barnabyosborne-cmyk/Hp42s_calc/firmware/components/plus42core/core_main.cc

/*****************************************************************************
 * Plus42 -- an enhanced HP-42S calculator simulator
 * Copyright (C) 2004-2026  Thomas Okken
 *
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
 * You should have received a copy of the GNU General Public License
 * along with this program; if not, see http://www.gnu.org/licenses/.
 *****************************************************************************/

#include <stdio.h>
#include <stdlib.h>
#include <string.h>
#include <stdarg.h>
#include <errno.h>

#include "core_main.h"
#include "core_commands2.h"
#include "core_commands4.h"
#include "core_commands7.h"
#include "core_commands8.h"
#include "core_commandsa.h"
#include "core_display.h"
#include "core_display.h"
#include "core_equations.h"
#include "core_helpers.h"
#include "core_keydown.h"
#include "core_math1.h"
#include "core_sto_rcl.h"
#include "core_tables.h"
#include "core_variables.h"
#include "shell.h"
#include "shell_spool.h"

#ifndef BCD_MATH
// We need these locally for BID128->double conversion
#include "bid_conf.h"
#include "bid_functions.h"
#endif

#ifdef WINDOWS
FILE *my_fopen(const char *name, const char *mode);
int my_rename(const char *oldname, const char *newname);
int my_remove(const char *name);
#else
#define my_fopen fopen
#define my_rename rename
#define my_remove remove
#endif


void set_shift(bool state) {
    if (mode_shift != state) {
        mode_shift = state;
        set_annunciators(-1, state, -1, -1, -1, -1);
    }
}

static bool initialized = false;
bool quitting = false;

static void continue_running();
static void stop_interruptible();
static bool handle_error(int error);

int repeating = 0;
int repeating_shift;
int repeating_key;

static int4 oldpc;
static char ann_hold = 0; // 0 = delay; 1 = flush; 2 = normal
bool start_eqn_cursor = false;
int skin_flags = -1;
bool force_redisplay = false;

core_settings_struct core_settings;

struct pending_equation {
    pgm_index idx;
    int4 pc;
    int4 length;
    char *text;
    pending_equation *next;
    bool compatMode;
    bool eval;
};

static pending_equation *eq_queue = NULL;

static void delete_pending_equations() {
    while (eq_queue != NULL) {
        pending_equation *peq = eq_queue;
        eq_queue = peq->next;
        free(peq->text);
        free(peq);
    }
}

static void handle_pending_equations() {
    while (eq_queue != NULL) {
        pending_equation *peq = eq_queue;
        int errpos;
        equation_data *eqd = new_equation_data(peq->text, peq->length, peq->compatMode, &errpos, -1);
        if (eqd == NULL && errpos == -1) {
            /* TODO: Insufficient Memory message */
            delete_pending_equations();
            return;
        }
        pgm_index saved_prgm = current_prgm;
        current_prgm = peq->idx;
        arg_struct arg;
        if (eqd != NULL) {
            arg.type = peq->eval ? ARGTYPE_IND_NUM : ARGTYPE_NUM;
            arg.val.num = eqd->eqn_index;
            store_command_after(&peq->pc, CMD_EMBED, &arg, NULL);
        } else {
            arg.type = ARGTYPE_XSTR;
            arg.length = peq->length;
            arg.val.xstr = peq->text;
            store_command_after(&peq->pc, CMD_XSTR, &arg, NULL);
        }
        current_prgm = saved_prgm;

        eq_queue = peq->next;
        free(peq->text);
        free(peq);
    }
}

void core_init(int *rows, int *cols, int read_saved_state, const char *state_file_name) {

    /* Possible values for read_saved_state:
     * 0: state file not present (Memory Clear)
     * 1: state file present and looks OK so far
     * 2: state file present but not OK (State File Corrupt)
     */

    phloat_init();

    char *state_file_name_crash = NULL;
    if (read_saved_state == 1) {
        // Before loading state, rename the state file by appending .crash
        // to its name. We'll rename it back, right after loading is done.
        // This way, if we crash while loading state, we end up with a
        // renamed state file, so the next time the app is run, it will
        // launch with Memory Clear rather than just crashing on startup over
        // and over, and, on iOS and Android, needing to be deleted and
        // reinstalled.
        size_t bufsize = strlen(state_file_name) + 24;
        state_file_name_crash = (char *) malloc(bufsize);
        uint4 date, time;
        int weekday;
        shell_get_time_date(&time, &date, &weekday);
        snprintf(state_file_name_crash, bufsize, "%s.%08u%08u.crash", state_file_name, date, time);
        my_rename(state_file_name, state_file_name_crash);
        gfile = my_fopen(state_file_name_crash, "rb");
        if (gfile == NULL)
            read_saved_state = 0;
    } else
        gfile = NULL;

    bool clear, too_new = false;
    int reason = 0;
    if (read_saved_state != 1 || !load_state(&clear, &too_new)) {
        reason = too_new ? 2 : (read_saved_state != 0 && !clear) ? 1 : 0;
        requested_disp_r = 8;
        requested_disp_c = 22;
        if (!display_exists())
            display_alloc(requested_disp_r, requested_disp_c);
        hard_reset(reason);
        force_redisplay = true;
    }
    if (gfile != NULL)
        fclose(gfile);
    if (state_file_name_crash != NULL) {
        if (reason == 0) {
            my_rename(state_file_name_crash, state_file_name);
        } else {
            char *tmp = (char *) malloc(strlen(state_file_name_crash) + 3);
            strcpy(tmp, state_file_name_crash);
            tmp[strlen(state_file_name_crash) - 6] = 0;
            strcat(tmp, reason == 1 ? ".corrupt" : ".too_new");
            my_rename(state_file_name_crash, tmp);
            free(tmp);
        }
        free(state_file_name_crash);
    }

    initialized = true;
    quitting = false;

    *rows = requested_disp_r;
    *cols = requested_disp_c;
    shell_set_skin_mode(eqn_alt_keys() ? flags.f.decimal_point ? 1 : 2 : 0);
    #if defined(ANDROID) || defined(IPHONE)
    mode_popup_unknown = true;
    #endif

    ann_hold = 1;
}

void core_save_state(const char *state_file_name) {
    if (mode_interruptible != NULL)
        stop_interruptible();
    set_running(false);

    size_t bufsize = strlen(state_file_name) + 24;
    char *state_file_name_crash = (char *) malloc(bufsize);
    uint4 date, time;
    int weekday;
    shell_get_time_date(&time, &date, &weekday);
    snprintf(state_file_name_crash, bufsize, "%s.%08u%08u.crash", state_file_name, date, time);

    gfile = my_fopen(state_file_name_crash, "wb");
    if (gfile != NULL) {
        bool success = save_state();
        fclose(gfile);
        if (success) {
            my_remove(state_file_name);
            my_rename(state_file_name_crash, state_file_name);
        }
    }
}

void core_cleanup() {
    if (!initialized)
        return;

    initialized = false;
    reset_math();
    free_vartype(varmenu_eqn);
    varmenu_eqn = NULL;
    free_vartype(matedit_x);
    matedit_x = NULL;
    current_prgm.set(root->id, 0);
    for (int i = 0; i <= sp; i++)
        free_vartype(stack[i]);
    sp = -1;
    free(stack);
    stack = NULL;
    stack_capacity = 0;
    free_vartype(lastx);
    lastx = NULL;
    clear_rtns_vars_and_prgms();
    clean_vartype_pools();
}

void set_annunciators(int updn, int shf, int prt, int run, int g, int rad) {
    if (!initialized || quitting)
        return;

    if (ann_hold == 2)
        shell_annunciators(updn, shf, prt, run, g, rad);
}

void core_repaint_display(int rows, int cols, int sflags) {
    if (!initialized || quitting)
        return;

    if (ann_hold == 1) {
        /* This used to be at the end of core_init(), but now that we're
         * calling that function before loading the skin, the initial
         * annunciator update has to be delayed.
         */
        shell_annunciators(mode_updown,
                           mode_shift,
                           0 /*print*/,
                           mode_running,
                           !flags.f.rad && flags.f.grad,
                           flags.f.rad || flags.f.grad);
        ann_hold = 2;
    }

    if (start_eqn_cursor) {
        eqn_restart_cursor();
        start_eqn_cursor = false;
    }

    if (sflags != -1 && sflags != skin_flags) {
        skin_flags = sflags;
        force_redisplay = true;
    }

    if (display_alloc(rows, cols) || (force_redisplay && !mode_plot_viewer))
        redisplay();
    else
        repaint_display();
    force_redisplay = false;
}

bool core_menu() {
    return mode_clall || get_front_menu() != MENU_NONE || eqn_active();
}

bool alpha_active() {
    int menu = get_front_menu();
    return menu >= MENU_ALPHA1 && menu <= MENU_ALPHA_MISC2;
}

int core_alpha_menu() {
    return !mode_getkey && alpha_active() ? 1 : eqn_editing() ? 2 : 0;
}

bool core_hex_menu() {
    return get_front_menu() == MENU_BASE_A_THRU_F;
}

int core_special_menu_key(int which) {
    return special_menu_key(which);
}

static bool core_keydown_2(int key, bool *enqueued, int *repeat);

bool core_keydown(int key, bool *enqueued, int *repeat) {
    if (key >= 1024 && key != 1034) {
        int code = key - 1024;
        char ubuf[5];
        int n = 0;
        if (code < 128) {
            ubuf[n++] = code;
        } else if (code < 2048) {
            ubuf[n++] = (code >> 6) | 0xc0;
            ubuf[n++] = (code & 63) | 0x80;
        } else if (code < 65536) {
            ubuf[n++] = (code >> 12) | 0xe0;
            ubuf[n++] = ((code >> 6) & 63) | 0x80;
            ubuf[n++] = (code & 63) | 0x80;
        } else if (code < 1114112) {
            ubuf[n++] = (code >> 18) | 0xf0;
            ubuf[n++] = ((code >> 12) & 63) | 0x80;
            ubuf[n++] = ((code >> 6) & 63) | 0x80;
            ubuf[n++] = (code & 63) | 0x80;
        } else {
            fail:
            set_shift(false);
            squeak();
            return core_keydown_2(0, enqueued, repeat);
        }
        ubuf[n] = 0;
        char hpbuf[5];
        int len = ascii2hp(hpbuf, 1, ubuf);
        if (len == 0)
            goto fail;
        if (hpbuf[0] == 31 && code != 0x2022 && code != 0xb7)
            // Unsupported character
            goto fail;
        key = 1024 + (hpbuf[0] & 255);
    }
    return core_keydown_2(key, enqueued, repeat);
}

bool core_keydown_command(const char *name, int type, bool *enqueued, int *repeat) {
    char hpname[70];
    int len = ascii2hp(hpname, 63, name);
    if (type == 2) {
        int ch = hpname[0] & 255;
        if (len == 0) {
            ch = 0;
            set_shift(false);
            squeak();
        }
        return core_keydown_2(ch == 0 ? 0 : ch + 1024, enqueued, repeat);
    } else {
        int cmd;
        if (type == 0) {
            if (string_equals(hpname, len, "NULL", 4)) {
                cmd = CMD_NONE;
                set_shift(false);
            } else {
                cmd = find_builtin(hpname, len);
                if (cmd == CMD_NONE) {
                    set_shift(false);
                    squeak();
                }
            }
        } else {
            if (len == 0 || len > 7) {
                cmd = CMD_NONE;
                set_shift(false);
                squeak();
            } else {
                memcpy(dcm_lbl + 1, hpname, len);
                dcm_lbl[0] = len;
                cmd = CMD_NULL; // Magic value to trigger XEQ "dcm_lbl"
            }
        }
        return core_keydown_2(cmd == CMD_NONE ? 0 : cmd + 2048, enqueued, repeat);
    }
}

static bool core_keydown_2(int key, bool *enqueued, int *repeat) {

    *enqueued = 0;
    *repeat = 0;

    if (!initialized || quitting)
        return false;

    if (key != 0)
        no_keystrokes_yet = false;

    int eqr = eqn_keydown(key, repeat);
    if (eqr != 0) {
        if (eqr != 2)
            // CALC not pressed; prevent key timeouts
            *enqueued = 1;
        return eqr == 3;
    }

    if (mode_plot_viewer) {
        *enqueued = 1;
        return plot_keydown(key, repeat);
    }

    if (key == KEY_SHIFT) {
        set_shift(!mode_shift);
        if (!mode_menu_static) {
            int menuid = get_front_menu();
            if (menuid == MENU_TOP_FCN || menuid == MENU_PGM_FCN1 || menuid == MENU_STAT1
                    || menuid == MENU_BASE2 || menuid == MENU_BASE3
                    || menuid == MENU_CUSTOM1 || menuid == MENU_CUSTOM2 || menuid == MENU_CUSTOM3)
                redisplay();
        }
        return (mode_running && !mode_getkey && !mode_pause) || keybuf_head != keybuf_tail;
    }

    if (mode_pause) {
        if (key == 0)
            return false;
        mode_pause = false;
        set_running(false);
        if (!mode_shift && (key == KEY_RUN || key == KEY_EXIT)) {
            redisplay();
            return false;
        }
    }

    if (mode_interruptible != NULL) {
        /* We're in the middle of an interruptible function
         * (e.g., INVRT, PRP); queue up any keystrokes and invoke
         * the appropriate callback to keep the function moving along
         */
        int error;
        bool keep_running;
        if (key != 0) {
            /* Enqueue... */
            *enqueued = 1;
            if (key == KEY_EXIT ||
                    (mode_stoppable && !mode_shift && key == KEY_RUN)) {
                keybuf_tail = keybuf_head;
                stop_interruptible();
                return false;
            } else {
                if (((keybuf_head + 1) & 15) != keybuf_tail) {
                    if (mode_shift)
                        key = -key;
                    keybuf[keybuf_head] = key;
                    keybuf_head = (keybuf_head + 1) & 15;
                }
            }
            set_shift(false);
        }
        error = mode_interruptible(false);
        if (error == ERR_INTERRUPTIBLE)
            /* Still not done */
            return true;
        mode_interruptible = NULL;
        keep_running = handle_error(error);
        if (mode_running) {
            if (!keep_running)
                set_running(false);
        } else {
            set_annunciators(-1, -1, -1, 0, -1, -1);
            pending_command = CMD_NONE;
        }
        if (mode_running || keybuf_tail != keybuf_head)
            return true;
        else {
            redisplay();
            return false;
        }
    }

    if (mode_running && !mode_getkey) {
        /* We're running; queue up any keystrokes and invoke
         * continue_running() to keep the program moving along
         */
        if (key != 0) {
            if (key == KEY_EXIT) {
                keybuf_tail = keybuf_head;
                set_shift(false);
                set_running(false);
                pending_command = CMD_CANCELLED;
                return false;
            }
            /* Enqueue... */
            *enqueued = 1;
            if (!mode_shift && key == KEY_RUN) {
                keybuf_tail = keybuf_head;
                set_running(false);
                redisplay();
                return false;
            }
            if (((keybuf_head + 1) & 15) != keybuf_tail) {
                if (mode_shift)
                    key = -key;
                keybuf[keybuf_head] = key;
                keybuf_head = (keybuf_head + 1) & 15;
            }
            set_shift(false);
        }
        continue_running();
        if ((mode_running && !mode_getkey && !mode_pause) || keybuf_tail != keybuf_head)
            return true;
        else {
            if (mode_getkey)
                /* Technically, the program is still running, but we turn
                 * off the 'running' annunciator so that the user has some
                 * cue that they may now type. (Actually, I'm doing it
                 * purely because the HP-42S does it, too!)
                 */
                set_annunciators(-1, -1, -1, 0, -1, -1);
            else if (!mode_pause)
                redisplay();
            return false;
        }
    }

    /* If we get here, mode_running must be false.
     * or a program is running but hanging in GETKEY;
     */

    if (keybuf_tail != keybuf_head) {
        /* We're not running, or a program is waiting in GETKEY;
         * feed queued-up keystroke to keydown()
         */
        int oldshift = 0;
        int oldkey = keybuf[keybuf_tail];
        if (oldkey < 0) {
            oldkey = -oldkey;
            oldshift = 1;
        }
        keybuf_tail = (keybuf_tail + 1) & 15;
        /* If we're in GETKEY mode, the 'running' annunciator is off;
         * see the code circa 30 lines back.
         * We now turn it back on since program execution resumes.
         */
        if (mode_getkey && mode_running)
            set_annunciators(-1, -1, -1, 1, -1, -1);
        /* Feed the dequeued key to the usual suspects */
        keydown(oldshift, oldkey);
        core_keyup();
        /* We've just de-queued a key; may have to enqueue
         * one as well, if the user is actually managing to
         * type while we're unwinding the keyboard buffer
         */
        if (key != 0) {
            if (((keybuf_head + 1) & 15) != keybuf_tail) {
                if (mode_shift)
                    key = -key;
                keybuf[keybuf_head] = key;
                keybuf_head = (keybuf_head + 1) & 15;
            }
            set_shift(false);
        }
        return (mode_running && !mode_getkey) || keybuf_head != keybuf_tail;
    }

    /* No program is running, or it is running but waiting for a
     * keystroke (GETKEY); handle any new keystroke that has just come in
     */
    if (key != 0) {
        int shift = mode_shift;
        set_shift(false);
        if (mode_getkey && mode_running)
            set_annunciators(-1, -1, -1, 1, -1, -1);
        keydown(shift, key);
        if (repeating != 0) {
            *repeat = repeating;
            repeating = 0;
        }
        return mode_running && !mode_getkey;
    }

    /* Nothing going on at all! */
    return false;
}

int dequeue_key() {
    if (keybuf_tail == keybuf_head)
        return 0;
    int key = keybuf[keybuf_tail];
    keybuf_tail = (keybuf_tail + 1) & 15;
    bool shift = key < 0;
    if (shift)
        key = -key;
    if (key > 2048) {
        key = find_cmd_getkey_mapping(key - 2048);
        if (key == 0)
            squeak();
    }
    else if (shift)
        key += 37;
    return key;
}

int core_repeat() {
    if (!initialized || quitting)
        return 0;

    int r = eqn_repeat();
    if (r != -1)
        return r;
    if (mode_plot_viewer) {
        r = plot_repeat();
        if (r != -1)
            return r;
    }
    keydown(repeating_shift, repeating_key);
    int rpt = repeating;
    repeating = 0;
    return rpt;
}

void core_keytimeout1() {
    if (!initialized || quitting)
        return;

    if (pending_command == CMD_LINGER1 || pending_command == CMD_LINGER2)
        return;
    if (pending_command == CMD_RUN || pending_command == CMD_SST
            || pending_command == CMD_SST_UP || pending_command == CMD_SST_RT) {
        int saved_pending_command = pending_command;
        if (pc == -1)
            pc = 0;
        move_prgm_highlight(1);
        flags.f.prgm_mode = 2; /* HACK - magic value to tell redisplay() */
                               /* not to suppress option menu highlights */
        pending_command = CMD_NONE;
        redisplay();
        flags.f.prgm_mode = 0;
        pending_command = saved_pending_command;
    } else if (pending_command != CMD_NONE && pending_command != CMD_CANCELLED
            && (cmd_array[pending_command].flags & FLAG_NO_SHOW) == 0) {
        bool saved_prgm_mode = flags.f.prgm_mode;
        flags.f.prgm_mode = 0;
        redisplay(2);
        flags.f.prgm_mode = saved_prgm_mode;
    }
}

void core_keytimeout2() {
    if (!initialized || quitting)
        return;

    if (pending_command == CMD_LINGER1 || pending_command == CMD_LINGER2)
        return;
    remove_program_catalog = 0;
    if (pending_command != CMD_NONE && pending_command != CMD_CANCELLED
            && (cmd_array[pending_command].flags & FLAG_NO_SHOW) == 0) {
        pending_command = CMD_NULL;
        bool saved_prgm_mode = flags.f.prgm_mode;
        flags.f.prgm_mode = 0;
        redisplay(2);
        flags.f.prgm_mode = saved_prgm_mode;
        pending_command = CMD_CANCELLED;
    }
}

bool core_timeout3(bool repaint) {
    if (!initialized || quitting)
        return false;

    if (eqn_timeout())
        return false;
    if (mode_pause) {
        if (repaint) {
            /* The PSE ended normally */
            mode_pause = false;
            if (mode_goose >= 0)
                mode_goose = -1 - mode_goose;
        }
        return true;
    }
    /* Remove the output of SHOW, MEM, or shift-VARMENU from the display */
    if (pending_command == CMD_LINGER1)
        pending_command = CMD_CANCELLED;
    else if (pending_command == CMD_LINGER2) {
        clear_message();
        pending_command = CMD_NONE;
        if (repaint)
            redisplay();
    }
    return false;
}

static void print_equation_segment(int4 pc) {
    if (current_prgm.dir != eq_dir->id)
        return;
    equation_data *eqd = eq_dir->prgms[current_prgm.idx].eq_data;
    if (eqd->map == NULL)
        return;
    int4 pos = eqd->map->lookup(pc2line(pc));
    if (pos == -1)
        return;
    static int4 last_eqn = -1;
    static int4 last_pos = -1;
    if (eqd->eqn_index == last_eqn && pos == last_pos)
        return;
    last_eqn = eqd->eqn_index;
    last_pos = pos;
    int w = flags.f.double_wide_print ? 12 : 24;
    int apos = flags.f.double_wide_print ? 4 : 9;
    char line[24];
    for (int i = 0; i < apos; i++) {
        int n = i + pos - apos;
        line[i] = n < 0 ? ' ' : eqd->text[n];
    }
    line[apos] = 6;
    for (int i = apos + 1; i < w; i++) {
        int n = i + pos - apos - 1;
        line[i] = n >= eqd->length ? ' ' : eqd->text[n];
    }
    print_text(line, w, true);
}

bool core_keyup() {
    if (!initialized || quitting)
        return false;

    if (mode_pause) {
        /* The only way this can happen is if they key in question was Shift */
        return false;
    }

    int error = ERR_NONE;

    if (pending_command == CMD_LINGER1 || pending_command == CMD_LINGER2) {
        pending_command = CMD_LINGER2;
        return mode_running || keybuf_head != keybuf_tail;
    }

    if (pending_command == CMD_SILENT_OFF) {
#ifdef IPHONE
        if (off_enabled()) {
            shell_always_on(0);
            quitting = true;
            shell_powerdown();
        } else {
            set_running(false);
            squeak();
        }
#else
        shell_always_on(0);
        quitting = true;
        shell_powerdown();
#endif
        pending_command = CMD_NONE;
        return false;
    }

    if (pending_command == CMD_NONE)
        return mode_running || mode_interruptible != NULL || keybuf_head != keybuf_tail;

    if (remove_program_catalog) {
        if (mode_transientmenu == MENU_CATALOG)
            set_menu(MENULEVEL_TRANSIENT, MENU_NONE);
        else if (mode_plainmenu == MENU_CATALOG)
            set_menu(MENULEVEL_PLAIN, MENU_NONE);
        remove_program_catalog = 0;
    }

    if (pending_command == CMD_CANCELLED || pending_command == CMD_NULL) {
        pending_command = CMD_NONE;
        redisplay();
        return mode_running || keybuf_head != keybuf_tail;
    }

    mode_varmenu = pending_command == CMD_VMSTO
                    || pending_command == CMD_VMSTO2
                    || pending_command == CMD_VMSOLVE
                    || pending_command == CMD_VMEXEC;

    if (input_length > 0) {
        /* INPUT active */
        if (pending_command == CMD_RUN || pending_command == CMD_SST
                || pending_command == CMD_SST_UP || pending_command == CMD_SST_RT) {
            int err;
            if (sp == -1) {
                vartype_real zero;
                zero.type = TYPE_REAL;
                zero.x = 0;
                stack[++sp] = (vartype *) &zero;
                err = generic_sto(&input_arg, 0);
                sp--;
            } else {
                err = generic_sto(&input_arg, 0);
            }
            input_length = 0;
            if (err != ERR_NONE) {
                pending_command = CMD_NONE;
                display_error(err);
                redisplay();
                return mode_running || keybuf_head != keybuf_tail;
            }
        } else if (pending_command == CMD_GTO
                || pending_command == CMD_GTODOT
                || pending_command == CMD_GTODOTDOT
                || pending_command == CMD_RTN)
            /* NOTE: set_running(true) also ends INPUT mode, so commands that
             * cause program execution to start do not have to be handled here.
             */
            input_length = 0;
    }

    if (pending_command == CMD_VMEXEC) {
        eqn_end();
        string_copy(reg_alpha, &reg_alpha_length,
                    pending_command_arg.val.text, pending_command_arg.length);
        goto do_run;
    }
    if (pending_command == CMD_PMEXEC) {
        eqn_end();
        vartype *v;
        if (pending_command_arg.type == ARGTYPE_EQN) {
            equation_data *eqdata = eq_dir->prgms[pending_command_arg.val.num].eq_data;
            int len = eqdata->length > 44 ? 44 : eqdata->length;
            string_copy(reg_alpha, &reg_alpha_length, eqdata->text, len);
            v = new_equation(eqdata);
        } else {
            string_copy(reg_alpha, &reg_alpha_length,
                        pending_command_arg.val.text, pending_command_arg.length);
            v = new_string(pending_command_arg.val.text, pending_command_arg.length);
        }
        // This is an incompatible change from the original PGMMENU, strictly speaking,
        // since it only returned the label name in ALPHA. I have to do something in
        // order to accommodate equations, though. So, if a program is selected, I
        // return it in ALPHA, as before, but I *also* return it as a string in X.
        // My hope is that no one will depend on the contents of the stack right after
        // PGMMENU, since the user is in normal interactive mode while the menu is
        // active.
        // Of course the scenario of the user going into the equation editor, selecting
        // an equation, and pressing CALC, is entirely new, so what we do in that case
        // isn't really an issue from a compatibility point of view. So, I'm copying as
        // much of the equation as I can into ALPHA, and placing the equation itself
        // in X.
        if (v != NULL)
            recall_result(v);
        goto do_run;
    }
    if (pending_command == CMD_RUN || pending_command == CMD_SST_UP) {
        do_run:
        if ((flags.f.trace_print || flags.f.normal_print)
                && flags.f.printer_exists)
            print_command(pending_command, &pending_command_arg);
        if (pending_command == CMD_SST_UP)
            step_out();
        pending_command = CMD_NONE;
        if (pc == -1)
            pc = 0;
        set_running(true);
        return true;
    }

    if (pending_command == CMD_SST || pending_command == CMD_SST_RT) {
        int cmd;
        arg_struct arg;
        oldpc = pc;
        if (pc == -1)
            pc = 0;
        get_next_command(&pc, &cmd, &arg, 1, NULL);
        if (pending_command == CMD_SST_RT
                && (cmd == CMD_XEQ || cmd == CMD_XEQL || cmd == CMD_EVAL
                    || cmd == CMD_EVALN || cmd == CMD_SOLVE || cmd == CMD_INTEG)) {
            pc = oldpc;
            step_over();
            goto do_run;
        }
        if ((flags.f.trace_print || flags.f.normal_print)
                && flags.f.printer_exists) {
            if (cmd == CMD_LBL)
                print_text(NULL, 0, true);
            print_equation_segment(oldpc);
            print_program_line(current_prgm, oldpc);
        }
        mode_disable_stack_lift = false;
        set_running(true);
        error = handle(cmd, &arg);
        set_running(false);
        mode_pause = false;
    } else {
        if ((flags.f.trace_print || flags.f.normal_print)
                && flags.f.printer_exists)
            print_command(pending_command, &pending_command_arg);
        mode_disable_stack_lift = false;
        error = handle(pending_command, &pending_command_arg);
        mode_pause = false;
        if (pending_command >= CMD_ROW_PLUS && pending_command <= CMD_COL_MINUS || pending_command == CMD_SETDS) {
            pending_command = CMD_LINGER2;
            shell_request_timeout3(2000);
            redisplay();
            return false;
        }
    }

    if (quitting)
        return false;

    if (error == ERR_INTERRUPTIBLE) {
        set_annunciators(-1, -1, -1, 1, -1, -1);
        pending_command = CMD_NONE;
        return true;
    }

    handle_error(error);
    pending_command = CMD_NONE;
    if (!mode_getkey && !mode_pause)
        redisplay();
    return (mode_running && !mode_getkey && !mode_pause) || keybuf_head != keybuf_tail;
}

bool core_powercycle() {
    bool need_redisplay = false;

    if (mode_interruptible != NULL)
        stop_interruptible();

    no_keystrokes_yet = true;

    keybuf_tail = keybuf_head;
    set_shift(false);
    #if (!defined(ANDROID) && !defined(IPHONE))
    shell_always_on(0);
    #endif
    pending_command = CMD_NONE;

    if (mode_getkey) {
        /* A real HP-42S can't be switched off while GETKEY is active: pressing
         * OFF on the keyboard returns code 70 and stops program execution; and
         * when the auto-poweroff timeout expires, code 70 is returned but
         * program execution continues.
         * Since Free42 can be shut down in a way the HP-42S can't, by exiting
         * the application, I have to fake it a bit; I put 70 in X as if the
         * user had done OFF twice on a real 42S.
         */
        vartype *seventy = new_real(70);
        if (seventy != NULL) {
            if (recall_result(seventy) != ERR_NONE)
                goto nomem;
            flags.f.stack_lift_disable = 0;
        } else {
            nomem:
            display_error(ERR_INSUFFICIENT_MEMORY);
            flags.f.auto_exec = 0;
        }
        if (!flags.f.auto_exec)
            need_redisplay = true;
        mode_getkey = false;
    }

    if (flags.f.auto_exec) {
        if (mode_command_entry)
            finish_command_entry(false);
        if (flags.f.prgm_mode) {
            if (mode_alpha_entry) {
                pc = incomplete_saved_pc;
                prgm_highlight_row = incomplete_saved_highlight_row;
            } else if (mode_number_entry) {
                arg_struct arg;
                arg.type = ARGTYPE_DOUBLE;
                arg.val_d = entered_number;
                cmdline[cmdline_length] = 0;
                store_command(pc, CMD_NUMBER, &arg, cmdline);
                move_prgm_highlight(1);
            }
            flags.f.prgm_mode = false;
        }
        mode_alpha_entry = false;
        mode_number_entry = false;
        set_menu(MENULEVEL_ALPHA, MENU_NONE);
        set_running(true);
        flags.f.auto_exec = 0;
        need_redisplay = false;
    } else {
        if (mode_running) {
            set_running(false);
            need_redisplay = true;
        }
    }

#ifdef BCD_MATH
    if (need_redisplay || state_file_number_format != NUMBER_FORMAT_BID128)
        redisplay();
#else
    if (need_redisplay || state_file_number_format != NUMBER_FORMAT_BINARY)
        redisplay();
#endif

    return mode_running;
}

char *core_list_programs() {
    int bufsize = 1024;
    char *buf = (char *) malloc(bufsize);
    if (buf == NULL)
        return NULL;
    int lastidx = -1;
    int bufptr = 4;
    int label;
    int count = 0;
    for (label = 0; label < cwd->labels_count; label++) {
        int len = cwd->labels[label].length;
        char name[51];
        int namelen = 0;
        int end = 0;
        int i;

        if (len == 0) {
            if (cwd->labels[label].prgm == lastidx)
                continue;
            if (label == cwd->labels_count - 1) {
                string2buf(name, 51, &namelen, ".END.", 5);
                namelen = 5;
            } else {
                string2buf(name, 51, &namelen, "END", 3);
                namelen = 3;
            }
            end = 1;
        } else {
            name[namelen++] = '"';
            namelen += hp2ascii(name + namelen, cwd->labels[label].name, len);
            name[namelen++] = '"';
            end = cwd->labels[label + 1].length == 0;
        }

        lastidx = cwd->labels[label].prgm;

        if (bufptr + namelen + 1 >= bufsize) {
            bufsize += 1024;
            char *newbuf = (char *) realloc(buf, bufsize);
            if (newbuf == NULL) {
                if (bufptr > 0 && buf[bufptr - 1] != 0) {
                    buf[bufptr - 1] = 0;
                    count++;
                }
                goto done;
            }
            buf = newbuf;
        }
        for (i = 0; i < namelen; i++)
            buf[bufptr++] = name[i];
        if (end) {
            buf[bufptr++] = 0;
            count++;
        } else {
            buf[bufptr++] = ' ';
        }
    }
    done:
    buf[0] = (char) (count >> 24);
    buf[1] = (char) (count >> 16);
    buf[2] = (char) (count >> 8);
    buf[3] = (char) count;
    return buf;
}

static void export_hp42s(int index) {
    int4 pc = 0;
    int cmd;
    arg_struct arg;
    pgm_index saved_prgm = current_prgm;
    unsigned char code_flags, code_name, code_std_1, code_std_2;
    char cmdbuf[50];
    int cmdlen;
    char buf[1000];
    int buflen = 0;
    int i;

    current_prgm.set(cwd->id, index);
    do {
        const char *orig_num;
        get_next_command(&pc, &cmd, &arg, 0, &orig_num);
        code_flags = (cmd_array[cmd].flags & (FLAG_SPECIAL | FLAG_ILLEGAL)) >> 5;
        code_name = cmd_array[cmd].scode;
        code_std_1 = cmd_array[cmd].code1;
        code_std_2 = cmd_array[cmd].code2;
        cmdlen = 0;
        switch (code_flags) {
            case 1:
                /* A command that requires some special attention */
                if (cmd == CMD_STO) {
                    if (arg.type == ARGTYPE_NUM && arg.val.num <= 15)
                        cmdbuf[cmdlen++] = 0x30 + arg.val.num;
                    else
                        goto normal;
                } else if (cmd == CMD_RCL) {
                    if (arg.type == ARGTYPE_NUM && arg.val.num <= 15)
                        cmdbuf[cmdlen++] = 0x20 + arg.val.num;
                    else
                        goto normal;
                } else if (cmd == CMD_FIX || cmd == CMD_SCI || cmd == CMD_ENG) {
                    char byte2;
                    if (arg.type != ARGTYPE_NUM || arg.val.num <= 9)
                        goto normal;
                    cmdbuf[cmdlen++] = (char) 0xf1;
                    if (arg.val.num == 10) {
                        switch (cmd) {
                            case CMD_FIX: byte2 = (char) 0xd5; break;
                            case CMD_SCI: byte2 = (char) 0xd6; break;
                            case CMD_ENG: byte2 = (char) 0xd7; break;
                        }
                    } else {
                        switch (cmd) {
                            case CMD_FIX: byte2 = (char) 0xe5; break;
                            case CMD_SCI: byte2 = (char) 0xe6; break;
                            case CMD_ENG: byte2 = (char) 0xe7; break;
                        }
                    }
                    cmdbuf[cmdlen++] = byte2;
                } else if (cmd == CMD_SIZE) {
                    cmdbuf[cmdlen++] = (char) 0xf3;
                    cmdbuf[cmdlen++] = (char) 0xf7;
                    cmdbuf[cmdlen++] = arg.val.num >> 8;
                    cmdbuf[cmdlen++] = arg.val.num;
                } else if (cmd == CMD_EMBED) {
                    int4 id = saving_state ? arg.val.num
                            : eq_dir->prgms[arg.val.num].eq_data->compatMode ? -2 : -1;
                    cmdbuf[cmdlen++] = (char) 0xf6;
                    cmdbuf[cmdlen++] = (char) 0xa7;
                    cmdbuf[cmdlen++] = (char) (arg.type == ARGTYPE_NUM ? 0x76 : 0x7e);
                    cmdbuf[cmdlen++] = id >> 24;
                    cmdbuf[cmdlen++] = id >> 16;
                    cmdbuf[cmdlen++] = id >> 8;
                    cmdbuf[cmdlen++] = id;
                    if (!saving_state) {
                        /* Flush cmdbuf, because the XSTR logic bypasses it */
                        for (i = 0; i < cmdlen; i++)
                            buf[buflen++] = cmdbuf[i];
                        cmdlen = 0;
                        equation_data *eqd = eq_dir->prgms[arg.val.num].eq_data;
                        arg.val.xstr = eqd->text;
                        arg.length = eqd->length > 65535 ? 65535 : eqd->length;
                        goto do_xstr;
                    }
                } else if (cmd == CMD_LBL) {
                    if (arg.type == ARGTYPE_NUM) {
                        if (arg.val.num <= 14)
                            cmdbuf[cmdlen++] = 0x01 + arg.val.num;
                        else
                            goto normal;
                    } else if (arg.type == ARGTYPE_STR) {
                        cmdbuf[cmdlen++] = (char) 0xc0;
                        cmdbuf[cmdlen++] = 0x00;
                        cmdbuf[cmdlen++] = 0xf1 + arg.length;
                        cmdbuf[cmdlen++] = 0x00;
                        for (i = 0; i < arg.length; i++)
                            cmdbuf[cmdlen++] = arg.val.text[i];
                    } else
                        goto normal;
                } else if (cmd == CMD_INPUT) {
                    if (arg.type == ARGTYPE_IND_NUM
                            || arg.type == ARGTYPE_IND_STK)
                        code_std_2 = 0xee;
                    goto normal;
                } else if (cmd == CMD_XEQ) {
                    if (arg.type == ARGTYPE_NUM || arg.type == ARGTYPE_STK
                                                || arg.type == ARGTYPE_LCLBL) {
                        code_std_1 = 0xe0;
                        code_std_2 = 0x00;
                        goto normal;
                    } else if (arg.type == ARGTYPE_STR) {
                        cmdbuf[cmdlen++] = 0x1e;
                        cmdbuf[cmdlen++] = 0xf0 + arg.length;
                        for (i = 0; i < arg.length; i++)
                            cmdbuf[cmdlen++] = arg.val.text[i];
                    } else
                        goto normal;
                } else if (cmd == CMD_GTO) {
                    if (arg.type == ARGTYPE_NUM && arg.val.num <= 14) {
                        cmdbuf[cmdlen++] = 0xb1 + arg.val.num;
                        cmdbuf[cmdlen++] = 0x00;
                    } else if (arg.type == ARGTYPE_NUM
                                        || arg.type == ARGTYPE_STK
                                        || arg.type == ARGTYPE_LCLBL) {
                        code_std_1 = 0xd0;
                        code_std_2 = 0x00;
                        goto normal;
                    } else if (arg.type == ARGTYPE_IND_NUM
                                        || arg.type == ARGTYPE_IND_STK) {
                        cmdbuf[cmdlen++] = (char) 0xae;
                        if (arg.type == ARGTYPE_IND_NUM)
                            arg.type = ARGTYPE_NUM;
                        else
                            arg.type = ARGTYPE_STK;
                        goto non_string_suffix;
                    } else if (arg.type == ARGTYPE_STR) {
                        cmdbuf[cmdlen++] = 0x1d;
                        cmdbuf[cmdlen++] = 0xf0 + arg.length;
                        for (i = 0; i < arg.length; i++)
                            cmdbuf[cmdlen++] = arg.val.text[i];
                    } else
                        goto normal;
                } else if (cmd == CMD_END) {
                    cmdbuf[cmdlen++] = (char) 0xc0;
                    cmdbuf[cmdlen++] = 0x00;
                    cmdbuf[cmdlen++] = 0x0d;
                } else if (cmd == CMD_N_PLUS_U) {
                    cmdbuf[cmdlen++] = (char) 0xa6;
                    cmdbuf[cmdlen++] = (char) 0xf7;
                    if (arg.type != ARGTYPE_NONE)
                        goto do_number;
                } else if (cmd == CMD_NUMBER) {
                    do_number:
                    const char *p;
                    if (orig_num != NULL)
                        p = orig_num;
                    else
                        p = phloat2program(arg.val_d);
                    char c;
                    while ((c = *p++) != 0) {
                        if (c >= '0' && c <= '9')
                            cmdbuf[cmdlen++] = 0x10 + c - '0';
                        else if (c == '.' || c == ',')
                            cmdbuf[cmdlen++] = 0x1a;
                        else if (c == 24)
                            cmdbuf[cmdlen++] = 0x1b;
                        else if (c == '-')
                            cmdbuf[cmdlen++] = 0x1c;
                        else
                            /* Should not happen */
                            continue;
                    }
                    cmdbuf[cmdlen++] = 0x00;
                    if (cmd == CMD_N_PLUS_U) {
                        for (i = 0; i < cmdlen; i++)
                            buf[buflen++] = cmdbuf[i];
                        cmdlen = 0;
                        goto do_xstr;
                    }
                } else if (cmd == CMD_STRING) {
                    cmdbuf[cmdlen++] = 0xf0 + arg.length;
                    for (i = 0; i < arg.length; i++)
                        cmdbuf[cmdlen++] = arg.val.text[i];
                } else if (cmd >= CMD_ASGN01 && cmd <= CMD_ASGN18) {
                    cmdbuf[cmdlen++] = 0xf2 + arg.length;
                    cmdbuf[cmdlen++] = (char) 0xc0;
                    for (i = 0; i < arg.length; i++)
                        cmdbuf[cmdlen++] = arg.val.text[i];
                    cmdbuf[cmdlen++] = cmd - CMD_ASGN01;
                } else if ((cmd >= CMD_KEY1G && cmd <= CMD_KEY9G)
                            || (cmd >= CMD_KEY1X && cmd <= CMD_KEY9X)) {
                    int keyg = cmd <= CMD_KEY9G;
                    int keynum = cmd - (keyg ? CMD_KEY1G : CMD_KEY1X) + 1;
                    if (arg.type == ARGTYPE_STR || arg.type == ARGTYPE_IND_STR){
                        cmdbuf[cmdlen++] = 0xf2 + arg.length;
                        cmdbuf[cmdlen++] = keyg ? 0xc3 : 0xc2;
                        if (arg.type == ARGTYPE_IND_STR)
                            cmdbuf[cmdlen - 1] += 8;
                        cmdbuf[cmdlen++] = keynum;
                        for (i = 0; i < arg.length; i++)
                            cmdbuf[cmdlen++] = arg.val.text[i];
                    } else {
                        cmdbuf[cmdlen++] = (char) 0xf3;
                        cmdbuf[cmdlen++] = keyg ? 0xe3 : 0xe2;
                        cmdbuf[cmdlen++] = keynum;
                        goto non_string_suffix;
                    }
                } else if (cmd == CMD_XROM) {
                    if (arg.type == ARGTYPE_NUM) {
                        cmdbuf[cmdlen++] = (char) (0xa0 + ((arg.val.num >> 8) & 7));
                        cmdbuf[cmdlen++] = (char) arg.val.num;
                    } else {
                        cmdbuf[cmdlen++] = (char) (0xf0 + arg.length);
                        for (int i = 0; i < arg.length; i++)
                            cmdbuf[cmdlen++] = arg.val.text[i];
                    }
                } else if (cmd == CMD_XSTR) {
                    do_xstr:
                    int len = arg.length;
                    if (len == 0) {
                        cmdbuf[cmdlen++] = (char) 0xf2;
                        cmdbuf[cmdlen++] = (char) 0xa7;
                        cmdbuf[cmdlen++] = (char) 0x41;
                    } else {
                        /* Writing directly to 'buf' here, not using 'cmdbuf', */
                        /* since XSTR can be very long and may not fit in one  */
                        /* piece.                                              */
                        const char *ptr = arg.val.xstr;
                        while (len > 0) {
                            if (buflen + 16 > 1000 - 50) {
                                if (fwrite(buf, 1, buflen, gfile) != buflen)
                                    goto done;
                                buflen = 0;
                            }
                            int slen = len <= 13 ? len : 13;
                            buf[buflen++] = (char) (0xf2 + slen);
                            buf[buflen++] = (char) 0xa7;
                            buf[buflen++] = (char) (slen < len ? 0x49 : 0x41);
                            memcpy(buf + buflen, ptr, slen);
                            buflen += slen;
                            ptr += slen;
                            len -= slen;
                        }
                    }
                } else if (cmd == CMD_GTOL) {
                    cmdbuf[cmdlen++] = (char) 0xf4;
                    cmdbuf[cmdlen++] = (char) 0xa7;
                    cmdbuf[cmdlen++] = (char) 0x32;
                    cmdbuf[cmdlen++] = arg.val.num >> 8;
                    cmdbuf[cmdlen++] = arg.val.num;
                } else if (cmd == CMD_XEQL) {
                    cmdbuf[cmdlen++] = (char) 0xf4;
                    cmdbuf[cmdlen++] = (char) 0xa7;
                    cmdbuf[cmdlen++] = (char) 0x33;
                    cmdbuf[cmdlen++] = arg.val.num >> 8;
                    cmdbuf[cmdlen++] = arg.val.num;
                } else {
                    /* Shouldn't happen */
                    continue;
                }
                break;
            case 0:
            normal:
                if (arg.type == ARGTYPE_STR || arg.type == ARGTYPE_IND_STR) {
                    int i;
                    if ((code_name & 0x80) == 0) {
                        cmdbuf[cmdlen++] = 0xf0 + arg.length + 2;
                        cmdbuf[cmdlen++] = (char) 0xa7;
                    } else {
                        cmdbuf[cmdlen++] = 0xf0 + arg.length + 1;
                    }
                    cmdbuf[cmdlen++] = arg.type == ARGTYPE_STR ? code_name
                                                            : code_name + 8;
                    for (i = 0; i < arg.length; i++)
                        cmdbuf[cmdlen++] = arg.val.text[i];
                } else {
                    unsigned char suffix;
                    if (code_std_1 != 0) {
                        if (code_std_1 == 0xf2 && (code_std_2 & 0x80) == 0) {
                            cmdbuf[cmdlen++] = (char) 0xf3;
                            cmdbuf[cmdlen++] = (char) 0xa7;
                        } else {
                            cmdbuf[cmdlen++] = code_std_1;
                        }
                    }
                    cmdbuf[cmdlen++] = code_std_2;

                    non_string_suffix:
                    suffix = 0;
                    switch (arg.type) {
                        case ARGTYPE_NONE:
                            goto no_suffix;
                        case ARGTYPE_IND_NUM:
                            suffix = 0x80;
                        case ARGTYPE_NUM:
                            suffix += arg.val.num;
                            break;
                        case ARGTYPE_IND_STK:
                            suffix = 0x80;
                        case ARGTYPE_STK:
                            switch (arg.val.stk) {
                                case 'X': suffix += 0x73; break;
                                case 'Y': suffix += 0x72; break;
                                case 'Z': suffix += 0x71; break;
                                case 'T': suffix += 0x70; break;
                                case 'L': suffix += 0x74; break;
                                default:
                                    /* Shouldn't happen */
                                    continue;
                            }
                            break;
                        case ARGTYPE_LCLBL:
                            if (arg.val.lclbl >= 'A' && arg.val.lclbl <= 'J')
                                suffix = arg.val.lclbl - 'A' + 0x66;
                            else if (arg.val.lclbl >= 'a' &&
                                                        arg.val.lclbl <= 'e')
                                suffix = arg.val.lclbl - 'a' + 0x7b;
                            else
                                /* Shouldn't happen */
                                continue;
                            break;
                        default:
                            /* Shouldn't happen */
                            /* Values not handled above are ARGTYPE_NEG_NUM,
                             * which is converted to ARGTYPE_NUM by
                             * get_next_command(); ARGTYPE_DOUBLE, which only
                             * occurs with CMD_NUMBER, which is handled in the
                             * special-case section, above;
                             * and ARGTYPE_LBLINDEX, which is converted to
                             * ARGTYPE_STR before being stored in a program.
                             */
                            continue;
                    }
                    cmdbuf[cmdlen++] = suffix;
                    no_suffix:
                    ;
                }
                break;
            case 2:
            default:
                /* Illegal command */
                continue;
        }
        if (buflen + cmdlen > 1000 - 50) {
            if (fwrite(buf, 1, buflen, gfile) != buflen)
                goto done;
            buflen = 0;
        }
        for (i = 0; i < cmdlen; i++)
            buf[buflen++] = cmdbuf[i];
    } while (cmd != CMD_END && pc < cwd->prgms[index].size);
    if (buflen > 0)
        fwrite(buf, 1, buflen, gfile);
    done:
    current_prgm = saved_prgm;
}

int4 core_program_size(int prgm_index) {
    int4 pc = 0;
    int cmd;
    arg_struct arg;
    pgm_index saved_prgm = current_prgm;
    unsigned char code_flags, code_name, code_std_1, code_std_2;
    int4 size = 0;

    current_prgm.set(cwd->id, prgm_index);
    do {
        const char *orig_num;
        get_next_command(&pc, &cmd, &arg, 0, &orig_num);
        code_flags = (cmd_array[cmd].flags & (FLAG_SPECIAL | FLAG_ILLEGAL)) >> 5;
        code_name = cmd_array[cmd].scode;
        code_std_1 = cmd_array[cmd].code1;
        code_std_2 = cmd_array[cmd].code2;
        switch (code_flags) {
            case 1:
                /* A command that requires some special attention */
                if (cmd == CMD_STO) {
                    if (arg.type == ARGTYPE_NUM && arg.val.num <= 15)
                        size += 1;
                    else
                        goto normal;
                } else if (cmd == CMD_RCL) {
                    if (arg.type == ARGTYPE_NUM && arg.val.num <= 15)
                        size += 1;
                    else
                        goto normal;
                } else if (cmd == CMD_FIX || cmd == CMD_SCI || cmd == CMD_ENG) {
                    goto normal;
                } else if (cmd == CMD_SIZE) {
                    size += 4;
                } else if (cmd == CMD_LBL) {
                    if (arg.type == ARGTYPE_NUM) {
                        if (arg.val.num <= 14)
                            size += 1;
                        else
                            goto normal;
                    } else if (arg.type == ARGTYPE_STR) {
                        size += arg.length + 4;
                    } else
                        goto normal;
                } else if (cmd == CMD_INPUT) {
                    goto normal;
                } else if (cmd == CMD_XEQ) {
                    if (arg.type == ARGTYPE_NUM || arg.type == ARGTYPE_STK
                                                || arg.type == ARGTYPE_LCLBL) {
                        size += 3;
                    } else if (arg.type == ARGTYPE_STR) {
                        size += arg.length + 2;
                    } else
                        goto normal;
                } else if (cmd == CMD_GTO) {
                    if (arg.type == ARGTYPE_NUM && arg.val.num <= 14) {
                        size += 2;
                    } else if (arg.type == ARGTYPE_NUM
                                        || arg.type == ARGTYPE_STK
                                        || arg.type == ARGTYPE_LCLBL) {
                        size += 3;
                    } else if (arg.type == ARGTYPE_STR) {
                        size += arg.length + 2;
                    } else
                        goto normal;
                } else if (cmd == CMD_END) {
                    /* Not counted for the line 00 total */
                } else if (cmd == CMD_NUMBER) {
                    const char *p;
                    if (orig_num != NULL)
                        p = orig_num;
                    else
                        p = phloat2program(arg.val_d);
                    size += (int) strlen(p) + 1;
                } else if (cmd == CMD_STRING) {
                    size += arg.length + 1;
                } else if (cmd >= CMD_ASGN01 && cmd <= CMD_ASGN18) {
                    size += arg.length + 3;
                } else if ((cmd >= CMD_KEY1G && cmd <= CMD_KEY9G)
                            || (cmd >= CMD_KEY1X && cmd <= CMD_KEY9X)) {
                    if (arg.type == ARGTYPE_STR || arg.type == ARGTYPE_IND_STR)
                        size += arg.length + 3;
                    else
                        size += 4;
                } else if (cmd == CMD_N_PLUS_U) {
                    size += 2;
                    if (arg.type != ARGTYPE_NONE) {
                        /* Add NUMBER and XSTR */
                        const char *p;
                        if (orig_num != NULL)
                            p = orig_num;
                        else
                            p = phloat2program(arg.val_d);
                        size += (int) strlen(p) + 1;
                        int n = (arg.length + 12) / 13;
                        if (n == 0)
                            n = 1;
                        size += arg.length + n * 3;
                    }
                } else if (cmd == CMD_XROM) {
                    if (arg.type == ARGTYPE_NUM)
                        size += 2;
                    else
                        size += arg.length + 1;
                } else if (cmd == CMD_XSTR) {
                    int n = (arg.length + 12) / 13;
                    if (n == 0)
                        n = 1;
                    size += arg.length + n * 3;
                } else if (cmd == CMD_EMBED) {
                    equation_data *eqd = eq_dir->prgms[arg.val.num].eq_data;
                    int len = eqd->length > 65535 ? 65535 : eqd->length;
                    int n = (len + 12) / 13;
                    size += len + n * 3 + 7;
                } else if (cmd == CMD_GTOL || cmd == CMD_XEQL) {
                    size += 5;
                } else {
                    /* Shouldn't happen */
                    continue;
                }
                break;
            case 0:
            normal:
                if (arg.type == ARGTYPE_STR || arg.type == ARGTYPE_IND_STR) {
                    size += arg.length + 2;
                    if ((code_name & 0x80) == 0)
                        /* Extra extension */
                        size += 1;
                } else {
                    size += code_std_1 == 0 ? 1 : 2;
                    if (arg.type != ARGTYPE_NONE)
                        size += 1;
                    if (code_std_1 == 0xf2 && (code_std_2 & 0x80) == 0)
                        /* Extra extension */
                        size += 1;
                }
                break;
            case 2:
            default:
                /* Illegal command */
                continue;
        }
    } while (cmd != CMD_END && pc < cwd->prgms[prgm_index].size);
    current_prgm = saved_prgm;
    return size;
}

void core_export_programs(int count, const int *indexes, const char *raw_file_name) {
    if (raw_file_name != NULL) {
#ifdef IPHONE
        if (strncmp(raw_file_name, "mem:", 4) == 0) {
            char *buf;
            ssize_t size;
            memcpy(&buf, raw_file_name + 5, sizeof(char *));
            memcpy(&size, raw_file_name + 13, sizeof(ssize_t));
            gfile = fmemopen(buf, size, "wb");
        } else {
#endif
            gfile = my_fopen(raw_file_name, "wb");
            if (gfile == NULL) {
                char msg[1024];
                int err = errno;
                snprintf(msg, 1024, "Could not open \"%s\" for writing: %s (%d)", raw_file_name, strerror(err), err);
                shell_message(msg);
                return;
            }
#ifdef IPHONE
        }
#endif
    }
    for (int i = 0; i < count; i++) {
        int p = indexes[i];
        export_hp42s(p);
    }
    if (raw_file_name != NULL) {
        if (ferror(gfile))
            shell_message("An error occurred during program export.");
        fclose(gfile);
    }
}

static int hp42tofree42[] = {
    /* Flag values: 0 = simple 1-byte command; 1 = 1-byte command with
     * embedded argument; 2 = 2-byte command, argument follows;
     * 3 = everything else, special case handling required.
     */

    /* 00-0F */
    /* NULL, LBL 00-14 */
    CMD_NULL  | 0x3000,
    CMD_LBL   | 0x1000,
    CMD_LBL   | 0x1000,
    CMD_LBL   | 0x1000,
    CMD_LBL   | 0x1000,
    CMD_LBL   | 0x1000,
    CMD_LBL   | 0x1000,
    CMD_LBL   | 0x1000,
    CMD_LBL   | 0x1000,
    CMD_LBL   | 0x1000,
    CMD_LBL   | 0x1000,
    CMD_LBL   | 0x1000,
    CMD_LBL   | 0x1000,
    CMD_LBL   | 0x1000,
    CMD_LBL   | 0x1000,
    CMD_LBL   | 0x1000,

    /* 10-1F */
    /* 0-9, ., E, -, GTO "", XEQ "", W "" */
    CMD_NULL  | 0x3000,
    CMD_NULL  | 0x3000,
    CMD_NULL  | 0x3000,
    CMD_NULL  | 0x3000,
    CMD_NULL  | 0x3000,
    CMD_NULL  | 0x3000,
    CMD_NULL  | 0x3000,
    CMD_NULL  | 0x3000,
    CMD_NULL  | 0x3000,
    CMD_NULL  | 0x3000,
    CMD_NULL  | 0x3000,
    CMD_NULL  | 0x3000,
    CMD_NULL  | 0x3000,
    CMD_NULL  | 0x3000,
    CMD_NULL  | 0x3000,
    CMD_NULL  | 0x3000,

    /* 20-2F */
    /* RCL 00-15 */
    CMD_RCL   | 0x1000,
    CMD_RCL   | 0x1000,
    CMD_RCL   | 0x1000,
    CMD_RCL   | 0x1000,
    CMD_RCL   | 0x1000,
    CMD_RCL   | 0x1000,
    CMD_RCL   | 0x1000,
    CMD_RCL   | 0x1000,
    CMD_RCL   | 0x1000,
    CMD_RCL   | 0x1000,
    CMD_RCL   | 0x1000,
    CMD_RCL   | 0x1000,
    CMD_RCL   | 0x1000,
    CMD_RCL   | 0x1000,
    CMD_RCL   | 0x1000,
    CMD_RCL   | 0x1000,

    /* 30-3F */
    /* STO 00-15 */
    CMD_STO   | 0x1000,
    CMD_STO   | 0x1000,
    CMD_STO   | 0x1000,
    CMD_STO   | 0x1000,
    CMD_STO   | 0x1000,
    CMD_STO   | 0x1000,
    CMD_STO   | 0x1000,
    CMD_STO   | 0x1000,
    CMD_STO   | 0x1000,
    CMD_STO   | 0x1000,
    CMD_STO   | 0x1000,
    CMD_STO   | 0x1000,
    CMD_STO   | 0x1000,
    CMD_STO   | 0x1000,
    CMD_STO   | 0x1000,
    CMD_STO   | 0x1000,

    /* 40-4F */
    CMD_ADD         | 0x0000,
    CMD_SUB         | 0x0000,
    CMD_MUL         | 0x0000,
    CMD_DIV         | 0x0000,
    CMD_X_LT_Y      | 0x0000,
    CMD_X_GT_Y      | 0x0000,
    CMD_X_LE_Y      | 0x0000,
    CMD_SIGMAADD    | 0x0000,
    CMD_SIGMASUB    | 0x0000,
    CMD_HMSADD      | 0x0000,
    CMD_HMSSUB      | 0x0000,
    CMD_MOD         | 0x0000,
    CMD_PERCENT     | 0x0000,
    CMD_PERCENT_CH  | 0x0000,
    CMD_TO_REC      | 0x0000,
    CMD_TO_POL      | 0x0000,

    /* 50-5F */
    CMD_LN         | 0x0000,
    CMD_SQUARE     | 0x0000,
    CMD_SQRT       | 0x0000,
    CMD_Y_POW_X    | 0x0000,
    CMD_CHS        | 0x0000,
    CMD_E_POW_X    | 0x0000,
    CMD_LOG        | 0x0000,
    CMD_10_POW_X   | 0x0000,
    CMD_E_POW_X_1  | 0x0000,
    CMD_SIN        | 0x0000,
    CMD_COS        | 0x0000,
    CMD_TAN        | 0x0000,
    CMD_ASIN       | 0x0000,
    CMD_ACOS       | 0x0000,
    CMD_ATAN       | 0x0000,
    CMD_TO_DEC     | 0x0000,

    /* 60-6F */
    CMD_INV     | 0x0000,
    CMD_ABS     | 0x0000,
    CMD_FACT    | 0x0000,
    CMD_X_NE_0  | 0x0000,
    CMD_X_GT_0  | 0x0000,
    CMD_LN_1_X  | 0x0000,
    CMD_X_LT_0  | 0x0000,
    CMD_X_EQ_0  | 0x0000,
    CMD_IP      | 0x0000,
    CMD_FP      | 0x0000,
    CMD_TO_RAD  | 0x0000,
    CMD_TO_DEG  | 0x0000,
    CMD_TO_HMS  | 0x0000,
    CMD_TO_HR   | 0x0000,
    CMD_RND     | 0x0000,
    CMD_TO_OCT  | 0x0000,

    /* 70-7F */
    CMD_CLSIGMA  | 0x0000,
    CMD_SWAP     | 0x0000,
    CMD_PI       | 0x0000,
    CMD_CLST     | 0x0000,
    CMD_RUP      | 0x0000,
    CMD_RDN      | 0x0000,
    CMD_LASTX    | 0x0000,
    CMD_CLX      | 0x0000,
    CMD_X_EQ_Y   | 0x0000,
    CMD_X_NE_Y   | 0x0000,
    CMD_SIGN     | 0x0000,
    CMD_X_LE_0   | 0x0000,
    CMD_MEAN     | 0x0000,
    CMD_SDEV     | 0x0000,
    CMD_AVIEW    | 0x0000,
    CMD_CLD      | 0x0000,

    /* 80-8F */
    CMD_DEG     | 0x0000,
    CMD_RAD     | 0x0000,
    CMD_GRAD    | 0x0000,
    CMD_ENTER   | 0x0000,
    CMD_STOP    | 0x0000,
    CMD_RTN     | 0x0000,
    CMD_BEEP    | 0x0000,
    CMD_CLA     | 0x0000,
    CMD_ASHF    | 0x0000,
    CMD_PSE     | 0x0000,
    CMD_CLRG    | 0x0000,
    CMD_AOFF    | 0x0000,
    CMD_AON     | 0x0000,
    CMD_OFF     | 0x0000,
    CMD_PROMPT  | 0x0000,
    CMD_ADV     | 0x0000,

    /* 90-9F */
    CMD_RCL       | 0x2000,
    CMD_STO       | 0x2000,
    CMD_STO_ADD   | 0x2000,
    CMD_STO_SUB   | 0x2000,
    CMD_STO_MUL   | 0x2000,
    CMD_STO_DIV   | 0x2000,
    CMD_ISG       | 0x2000,
    CMD_DSE       | 0x2000,
    CMD_VIEW      | 0x2000,
    CMD_SIGMAREG  | 0x2000,
    CMD_ASTO      | 0x2000,
    CMD_ARCL      | 0x2000,
    CMD_FIX       | 0x2000,
    CMD_SCI       | 0x2000,
    CMD_ENG       | 0x2000,
    CMD_TONE      | 0x2000,

    /* A0-AF */
    /* XROM (+ 42S ext), GTO/XEQ IND, SPARE1 */
    CMD_NULL   | 0x3000,
    CMD_NULL   | 0x3000,
    CMD_NULL   | 0x3000,
    CMD_NULL   | 0x3000,
    CMD_NULL   | 0x3000,
    CMD_NULL   | 0x3000,
    CMD_NULL   | 0x3000,
    CMD_NULL   | 0x3000,
    CMD_SF     | 0x2000,
    CMD_CF     | 0x2000,
    CMD_FSC_T  | 0x2000,
    CMD_FCC_T  | 0x2000,
    CMD_FS_T   | 0x2000,
    CMD_FC_T   | 0x2000,
    CMD_NULL   | 0x3000,
    CMD_NULL   | 0x3000,

    /* B0-BF */
    /* SPARE2, GTO 00-14 */
    CMD_NULL  | 0x3000,
    CMD_NULL  | 0x3000,
    CMD_NULL  | 0x3000,
    CMD_NULL  | 0x3000,
    CMD_NULL  | 0x3000,
    CMD_NULL  | 0x3000,
    CMD_NULL  | 0x3000,
    CMD_NULL  | 0x3000,
    CMD_NULL  | 0x3000,
    CMD_NULL  | 0x3000,
    CMD_NULL  | 0x3000,
    CMD_NULL  | 0x3000,
    CMD_NULL  | 0x3000,
    CMD_NULL  | 0x3000,
    CMD_NULL  | 0x3000,
    CMD_NULL  | 0x3000,

    /* C0-CF */
    /* GLOBAL */
    CMD_NULL    | 0x3000,
    CMD_NULL    | 0x3000,
    CMD_NULL    | 0x3000,
    CMD_NULL    | 0x3000,
    CMD_NULL    | 0x3000,
    CMD_NULL    | 0x3000,
    CMD_NULL    | 0x3000,
    CMD_NULL    | 0x3000,
    CMD_NULL    | 0x3000,
    CMD_NULL    | 0x3000,
    CMD_NULL    | 0x3000,
    CMD_NULL    | 0x3000,
    CMD_NULL    | 0x3000,
    CMD_NULL    | 0x3000,
    CMD_X_SWAP  | 0x2000,
    CMD_LBL     | 0x2000,

    /* D0-DF */
    /* 3-byte GTO */
    CMD_NULL  | 0x3000,
    CMD_NULL  | 0x3000,
    CMD_NULL  | 0x3000,
    CMD_NULL  | 0x3000,
    CMD_NULL  | 0x3000,
    CMD_NULL  | 0x3000,
    CMD_NULL  | 0x3000,
    CMD_NULL  | 0x3000,
    CMD_NULL  | 0x3000,
    CMD_NULL  | 0x3000,
    CMD_NULL  | 0x3000,
    CMD_NULL  | 0x3000,
    CMD_NULL  | 0x3000,
    CMD_NULL  | 0x3000,
    CMD_NULL  | 0x3000,
    CMD_NULL  | 0x3000,

    /* E0-EF */
    /* 3-byte XEQ */
    CMD_NULL  | 0x3000,
    CMD_NULL  | 0x3000,
    CMD_NULL  | 0x3000,
    CMD_NULL  | 0x3000,
    CMD_NULL  | 0x3000,
    CMD_NULL  | 0x3000,
    CMD_NULL  | 0x3000,
    CMD_NULL  | 0x3000,
    CMD_NULL  | 0x3000,
    CMD_NULL  | 0x3000,
    CMD_NULL  | 0x3000,
    CMD_NULL  | 0x3000,
    CMD_NULL  | 0x3000,
    CMD_NULL  | 0x3000,
    CMD_NULL  | 0x3000,
    CMD_NULL  | 0x3000,

    /* F0-FF */
    /* Strings + 42S ext */
    CMD_NOP  | 0x0000,
    CMD_NULL  | 0x3000,
    CMD_NULL  | 0x3000,
    CMD_NULL  | 0x3000,
    CMD_NULL  | 0x3000,
    CMD_NULL  | 0x3000,
    CMD_NULL  | 0x3000,
    CMD_NULL  | 0x3000,
    CMD_NULL  | 0x3000,
    CMD_NULL  | 0x3000,
    CMD_NULL  | 0x3000,
    CMD_NULL  | 0x3000,
    CMD_NULL  | 0x3000,
    CMD_NULL  | 0x3000,
    CMD_NULL  | 0x3000,
    CMD_NULL  | 0x3000
};

static int hp42ext[] = {
    /* Flag values: 0 = string, 1 = IND string, 2 = suffix, 3 = special,
     * 4 = illegal
     * Values 80-ff are the space used on the HP-42S, that is, strings whose
     * first character has its high bit set. Since the gaps left in that
     * scheme ran out when development of Plus42 started, additional
     * extensions had to be defined, and they are encoded using a7 as the
     * first character, and the opcode in the second character. By keeping
     * that second-character opcode in the range 00-7f, we can still
     * use a single byte lookup for all these extensions.
     */

    /* 00-0F */
    CMD_NULL    | 0x4000,
    CMD_XASTO   | 0x0000,
    CMD_LXASTO  | 0x0000,
    CMD_HEAD    | 0x0000,
    CMD_X_EQ_NN | 0x0000,
    CMD_X_NE_NN | 0x0000,
    CMD_X_LT_NN | 0x0000,
    CMD_X_GT_NN | 0x0000,
    CMD_RENAME  | 0x2000,
    CMD_XASTO   | 0x1000,
    CMD_LXASTO  | 0x1000,
    CMD_HEAD    | 0x1000,
    CMD_X_EQ_NN | 0x1000,
    CMD_X_NE_NN | 0x1000,
    CMD_X_LT_NN | 0x1000,
    CMD_X_GT_NN | 0x1000,

    /* 10-1F */
    CMD_CHDIR   | 0x2000,
    CMD_XASTO   | 0x2000,
    CMD_LXASTO  | 0x2000,
    CMD_HEAD    | 0x2000,
    CMD_X_EQ_NN | 0x2000,
    CMD_X_NE_NN | 0x2000,
    CMD_X_LT_NN | 0x2000,
    CMD_X_GT_NN | 0x2000,
    CMD_X_LE_NN | 0x2000,
    CMD_X_GE_NN | 0x2000,
    CMD_0_EQ_NN | 0x2000,
    CMD_0_NE_NN | 0x2000,
    CMD_0_LT_NN | 0x2000,
    CMD_0_GT_NN | 0x2000,
    CMD_0_LE_NN | 0x2000,
    CMD_0_GE_NN | 0x2000,

    /* 20-2F */
    CMD_X_LE_NN | 0x0000,
    CMD_X_GE_NN | 0x0000,
    CMD_0_EQ_NN | 0x0000,
    CMD_0_NE_NN | 0x0000,
    CMD_0_LT_NN | 0x0000,
    CMD_0_GT_NN | 0x0000,
    CMD_0_LE_NN | 0x0000,
    CMD_0_GE_NN | 0x0000,
    CMD_X_LE_NN | 0x1000,
    CMD_X_GE_NN | 0x1000,
    CMD_0_EQ_NN | 0x1000,
    CMD_0_NE_NN | 0x1000,
    CMD_0_LT_NN | 0x1000,
    CMD_0_GT_NN | 0x1000,
    CMD_0_LE_NN | 0x1000,
    CMD_0_GE_NN | 0x1000,

    /* 30-3F */
    CMD_PGMVAR  | 0x2000,
    CMD_VARMNU1 | 0x2000,
    CMD_NULL    | 0x3000, /* GTOL */
    CMD_NULL    | 0x3000, /* XEQL */
    CMD_GSTO    | 0x0000,
    CMD_GRCL    | 0x0000,
    CMD_EVALN   | 0x2000,
    CMD_EQNSLV  | 0x2000,
    CMD_EQNINT  | 0x2000,
    CMD_EQNVAR  | 0x2000,
    CMD_EQNMENU | 0x2000,
    CMD_EQNMNU1 | 0x2000,
    CMD_RAISE   | 0x1000,
    CMD_RAISE   | 0x2000,
    CMD_CRDIR   | 0x2000,
    CMD_PGDIR   | 0x2000,

    /* 40-4F */
    CMD_PGMVAR  | 0x0000,
    CMD_XSTR    | 0x0000,
    CMD_VARMNU1 | 0x0000,
    CMD_EVALN   | 0x0000,
    CMD_EQNSLV  | 0x0000,
    CMD_EQNINT  | 0x0000,
    CMD_EQNVAR  | 0x0000,
    CMD_EQNMENU | 0x0000,
    CMD_PGMVAR  | 0x1000,
    CMD_XSTR    | 0x1000,
    CMD_VARMNU1 | 0x1000,
    CMD_EVALN   | 0x1000,
    CMD_EQNSLV  | 0x1000,
    CMD_EQNINT  | 0x1000,
    CMD_EQNVAR  | 0x1000,
    CMD_EQNMENU | 0x1000,

    /* 50-5F */
    CMD_EQNMNU1 | 0x0000,
    CMD_CRDIR   | 0x0000,
    CMD_PGDIR   | 0x0000,
    CMD_CHDIR   | 0x0000,
    CMD_RENAME  | 0x0000,
    CMD_PGMPLOT | 0x0000,
    CMD_EQNPLOT | 0x0000,
    CMD_XAXIS   | 0x0000,
    CMD_EQNMNU1 | 0x1000,
    CMD_CRDIR   | 0x1000,
    CMD_PGDIR   | 0x1000,
    CMD_CHDIR   | 0x1000,
    CMD_RENAME  | 0x1000,
    CMD_PGMPLOT | 0x1000,
    CMD_EQNPLOT | 0x1000,
    CMD_XAXIS   | 0x1000,

    /* 60-6F */
    CMD_PGMPLOT | 0x2000,
    CMD_EQNPLOT | 0x2000,
    CMD_XAXIS   | 0x2000,
    CMD_YAXIS   | 0x2000,
    CMD_LCLV    | 0x2000,
    CMD_GETMI   | 0x2000,
    CMD_PUTMI   | 0x2000,
    CMD_GETLI   | 0x2000,
    CMD_PUTLI   | 0x2000,
    CMD_NULL    | 0x4000,
    CMD_NULL    | 0x4000,
    CMD_NULL    | 0x4000,
    CMD_NULL    | 0x4000,
    CMD_NULL    | 0x4000,
    CMD_NULL    | 0x4000,
    CMD_NULL    | 0x4000,

    /* 70-7F */
    CMD_YAXIS | 0x0000,
    CMD_LCLV  | 0x0000,
    CMD_GETMI | 0x0000,
    CMD_PUTMI | 0x0000,
    CMD_GETLI | 0x0000,
    CMD_PUTLI | 0x0000,
    CMD_EMBED | 0x3000,
    CMD_NULL  | 0x4000,
    CMD_YAXIS | 0x1000,
    CMD_LCLV  | 0x1000,
    CMD_GETMI | 0x1000,
    CMD_PUTMI | 0x1000,
    CMD_GETLI | 0x1000,
    CMD_PUTLI | 0x1000,
    CMD_EMBED | 0x3000,
    CMD_NULL  | 0x4000,

    /* 80-8F */
    CMD_VIEW    | 0x0000,
    CMD_STO     | 0x0000,
    CMD_STO_ADD | 0x0000,
    CMD_STO_SUB | 0x0000,
    CMD_STO_MUL | 0x0000,
    CMD_STO_DIV | 0x0000,
    CMD_X_SWAP  | 0x0000,
    CMD_INDEX   | 0x0000,
    CMD_VIEW    | 0x1000,
    CMD_STO     | 0x1000,
    CMD_STO_ADD | 0x1000,
    CMD_STO_SUB | 0x1000,
    CMD_STO_MUL | 0x1000,
    CMD_STO_DIV | 0x1000,
    CMD_X_SWAP  | 0x1000,
    CMD_INDEX   | 0x1000,

    /* 90-9F */
    CMD_MVAR    | 0x0000,
    CMD_RCL     | 0x0000,
    CMD_RCL_ADD | 0x0000,
    CMD_RCL_SUB | 0x0000,
    CMD_RCL_MUL | 0x0000,
    CMD_RCL_DIV | 0x0000,
    CMD_ISG     | 0x0000,
    CMD_DSE     | 0x0000,
    CMD_MVAR    | 0x1000,
    CMD_RCL     | 0x1000,
    CMD_RCL_ADD | 0x1000,
    CMD_RCL_SUB | 0x1000,
    CMD_RCL_MUL | 0x1000,
    CMD_RCL_DIV | 0x1000,
    CMD_ISG     | 0x1000,
    CMD_DSE     | 0x1000,

    /* A0-AF */
    CMD_RTNERR | 0x2000,
    CMD_DROPN  | 0x2000,
    CMD_DUPN   | 0x2000,
    CMD_PICK   | 0x2000,
    CMD_UNPICK | 0x2000,
    CMD_RDNN   | 0x2000,
    CMD_RUPN   | 0x2000,
    CMD_NULL   | 0x3000, /* Extra extensions */
    CMD_SF     | 0x1000,
    CMD_CF     | 0x1000,
    CMD_FSC_T  | 0x1000,
    CMD_FCC_T  | 0x1000,
    CMD_FS_T   | 0x1000,
    CMD_FC_T   | 0x1000,
    CMD_GTO    | 0x1000,
    CMD_XEQ    | 0x1000,

    /* B0-BF */
    CMD_CLV    | 0x0000,
    CMD_PRV    | 0x0000,
    CMD_ASTO   | 0x0000,
    CMD_ARCL   | 0x0000,
    CMD_PGMINT | 0x0000,
    CMD_PGMSLV | 0x0000,
    CMD_INTEG  | 0x0000,
    CMD_SOLVE  | 0x0000,
    CMD_CLV    | 0x1000,
    CMD_PRV    | 0x1000,
    CMD_ASTO   | 0x1000,
    CMD_ARCL   | 0x1000,
    CMD_PGMINT | 0x1000,
    CMD_PGMSLV | 0x1000,
    CMD_INTEG  | 0x1000,
    CMD_SOLVE  | 0x1000,

    /* CO-CF */
    CMD_NULL    | 0x3000, /* ASSIGN */
    CMD_VARMENU | 0x0000,
    CMD_NULL    | 0x3000, /* KEYX name */
    CMD_NULL    | 0x3000, /* KEYG name */
    CMD_DIM     | 0x0000,
    CMD_INPUT   | 0x0000,
    CMD_EDITN   | 0x0000,
    CMD_LSTO    | 0x0000,
    CMD_LASTO   | 0x2000,
    CMD_VARMENU | 0x1000,
    CMD_NULL    | 0x3000, /* KEYX IND name */
    CMD_NULL    | 0x3000, /* KEYG IND name */
    CMD_DIM     | 0x1000,
    CMD_INPUT   | 0x1000,
    CMD_EDITN   | 0x1000,
    CMD_LSTO    | 0x1000,

    /* DO-DF */
    CMD_INPUT    | 0x2000,
    CMD_RCL_ADD  | 0x2000,
    CMD_RCL_SUB  | 0x2000,
    CMD_RCL_MUL  | 0x2000,
    CMD_RCL_DIV  | 0x2000,
    CMD_NULL     | 0x4000, /* FIX 10 */
    CMD_NULL     | 0x4000, /* SCI 10 */
    CMD_NULL     | 0x4000, /* ENG 10 */
    CMD_CLV      | 0x2000,
    CMD_PRV      | 0x2000,
    CMD_INDEX    | 0x2000,
    CMD_SIGMAREG | 0x1000,
    CMD_FIX      | 0x1000,
    CMD_SCI      | 0x1000,
    CMD_ENG      | 0x1000,
    CMD_TONE     | 0x1000,

    /* E0-EF */
    CMD_FUNC   | 0x2000,
    CMD_NULL   | 0x4000,
    CMD_NULL   | 0x3000, /* KEYX suffix */
    CMD_NULL   | 0x3000, /* KEYG suffix */
    CMD_RTNERR | 0x1000,
    CMD_NULL   | 0x4000, /* FIX 11 */
    CMD_NULL   | 0x4000, /* SCI 11 */
    CMD_NULL   | 0x4000, /* ENG 11 */
    CMD_PGMINT | 0x2000,
    CMD_PGMSLV | 0x2000,
    CMD_INTEG  | 0x2000,
    CMD_SOLVE  | 0x2000,
    CMD_DIM    | 0x2000,
    CMD_LSTO   | 0x2000,
    CMD_INPUT  | 0x2000,
    CMD_EDITN  | 0x2000,

    /* F0-FF */
    CMD_CLP     | 0x0000,
    CMD_NULL    | 0x4000, /* XFCN */
    CMD_NULL    | 0x4000, /* GTO . nnnn */
    CMD_NULL    | 0x4000, /* GTO .. */
    CMD_NULL    | 0x4000, /* GTO . "name" */
    CMD_LASTO   | 0x0000,
    CMD_NULL    | 0x4000, /* DEL */
    CMD_NULL    | 0x3000, /* SIZE */
    CMD_VARMENU | 0x2000,
    CMD_DROPN   | 0x1000,
    CMD_DUPN    | 0x1000,
    CMD_PICK    | 0x1000,
    CMD_UNPICK  | 0x1000,
    CMD_LASTO   | 0x1000,
    CMD_RDNN    | 0x1000,
    CMD_RUPN    | 0x1000
};


static bool looks_like_zero(const char *buf) {
    char c;
    while ((c = *buf++) != 0) {
        if (c >= '1' && c <= '9')
            return false;
        if (c == 'E')
            return true;
    }
    return true;
}

static bool parse_number_line(char *buf, phloat *res) {
    if (buf[0] == 'E' || buf[0] == '-' && buf[1] == 'E') {
        char *buf2 = (char *) malloc(strlen(buf) + 2);
        strcpy(buf2 + 1, buf);
        if (buf[0] == 'E') {
            buf2[0] = '1';
        } else {
            buf2[0] = '-';
            buf2[1] = '1';
        }
        int len2 = (int) strlen(buf2);
        if (buf2[len2 - 1] == 'E')
            buf2[len2 - 1] = 0;
        bool success = parse_number_line(buf2, res);
        free(buf2);
        return success;
    }

    /* This isn't very thorough, but the aim is simply to prevent things
     * that start with a valid number character but are clearly not valid
     * numbers from being accepted as number lines. Things like
     * EXACTAMUNDO, for instance, or numbers with attached text like
     * 20five.
     */
    bool seen_e = false;
    for (char *cp = buf; *cp != 0; cp++) {
        char c = *cp;
        if (seen_e && (c == 'E' || c == '.'))
            return false;
        if (c == 'E')
            seen_e = true;
        else if ((c < '0' || c > '9') && c != '.' && c != '+' && c != '-')
            return false;
    }

#ifdef BCD_MATH
    *res = Phloat(buf);
#else
    BID_UINT128 d;
    bid128_from_string(&d, buf);
    bid128_to_binary64(res, &d);
#endif
    if (p_isinf(*res) != 0)
        *res = NAN_1_PHLOAT;
    else if (*res == 0 && !looks_like_zero(buf))
        *res = NAN_2_PHLOAT;
    return true;
}

static void decode_xrom(int byte1, int byte2, int *cmd, arg_struct *arg) {
    /* XROM & parameterless HP-42S extensions.
     * I don't want to build a reverse look-up table
     * for these, so instead I just do a linear search
     * on the cmd_array table.
     */
    uint4 code = (((unsigned int) byte1) << 8) | byte2;
    if (code >= 0x0a679 && code <= 0x0a67e) {
        /* HP-41CX: X=NN? etc. */
        switch (code & 0xf) {
            case 0x9: *cmd = CMD_X_EQ_NN; break;
            case 0xa: *cmd = CMD_X_NE_NN; break;
            case 0xb: *cmd = CMD_X_LT_NN; break;
            case 0xc: *cmd = CMD_X_LE_NN; break;
            case 0xd: *cmd = CMD_X_GT_NN; break;
            case 0xe: *cmd = CMD_X_GE_NN; break;
        }
        arg->type = ARGTYPE_IND_STK;
        arg->val.stk = 'Y';
        return;
    }
    for (int i = 0; i < CMD_SENTINEL; i++)
        if (cmd_array[i].code1 == byte1 && cmd_array[i].code2 == byte2) {
            if ((cmd_array[i].flags & FLAG_HIDDEN) != 0)
                break;
            *cmd = i;
            arg->type = ARGTYPE_NONE;
            return;
        }
    /* Not found; insert XROM instruction */
    *cmd = CMD_XROM;
    arg->type = ARGTYPE_NUM;
    arg->val.num = code & 0x07ff;
}

static void decode_suffix(int cmd, int suffix, arg_struct *arg) {
    bool ind = (suffix & 0x80) != 0;
    suffix &= 0x7f;
    if (!ind && (cmd == CMD_LBL || cmd == CMD_GTO || cmd == CMD_XEQ
                || cmd >= CMD_KEY1G && cmd <= CMD_KEY9X)
            && suffix >= 102 && suffix <= 111) {
        arg->type = ARGTYPE_LCLBL;
        arg->val.lclbl = 'A' + (suffix - 102);
    } else if (!ind && (cmd == CMD_LBL || cmd == CMD_GTO || cmd == CMD_XEQ
                || cmd >= CMD_KEY1G && cmd <= CMD_KEY9X)
            && suffix >= 123) {
        arg->type = ARGTYPE_LCLBL;
        arg->val.lclbl = 'a' + (suffix - 123);
    } else if (suffix >= 112 && suffix <= 116) {
        arg->type = ind ? ARGTYPE_IND_STK : ARGTYPE_STK;
        switch (suffix) {
            case 112: arg->val.stk = 'T'; break;
            case 113: arg->val.stk = 'Z'; break;
            case 114: arg->val.stk = 'Y'; break;
            case 115: arg->val.stk = 'X'; break;
            case 116: arg->val.stk = 'L'; break;
        }
    } else {
        arg->type = ind ? ARGTYPE_IND_NUM : ARGTYPE_NUM;
        arg->val.num = suffix;
    }
}

static void decode_string(unsigned char *buf, int *cmd, arg_struct *arg, char **xstr_buf, int *xstr_len, int *eq_mode, bool *after_end, bool force_new, bool sw_30_94) {
    int pos = 0;
    int byte1 = buf[pos++];
    int byte2 = buf[pos++];
    int str_len = 0;
    bool extra_extension = false;
    bool assign = false;

    if ((byte2 & 0x80) == 0) {
        /* String */
        int i;
        *cmd = CMD_STRING;
        goto string_2;
        xrom_string:
        *cmd = CMD_XROM;
        string_2:
        str_len = byte1 - 0xf0;
        pos--;
        arg->type = ARGTYPE_STR;
        do_string:
        for (i = 0; i < str_len; i++)
            arg->val.text[i] = buf[pos++];
        if (extra_extension) {
            memmove(arg->val.text + 1, arg->val.text, str_len);
            arg->val.text[0] = (char) 0xa7;
            str_len++;
        }
        arg->length = str_len;
        if (assign) {
            assign = false;
            int key = buf[pos++];
            if (key > 17) {
                /* Bad assign... Fix the command to the string
                 * it would have been if I had known this
                 * earlier.
                 */
                for (i = arg->length; i > 0; i--)
                    arg->val.text[i] = arg->val.text[i - 1];
                arg->val.text[0] = (char) 0xc0;
                arg->val.text[arg->length + 1] = key;
                arg->length += 2;
            } else {
                *cmd += key;
            }
        }
        if (*cmd == CMD_XSTR) {
            // XSTR is stored as a sequence of instructions, since
            // it may encode a string of up to 65535 characters, while
            // instructions are limited to 16 bytes, giving a payload
            // of up to 13 characters per instruction.
            char *newbuf;
            newbuf = (char *) realloc(*xstr_buf, *xstr_len + arg->length);
            if (newbuf == NULL && *xstr_len + arg->length != 0) {
                no_mem:
                *cmd = CMD_CANCELLED;
                return;
            }
            *xstr_buf = newbuf;
            memcpy(*xstr_buf + *xstr_len, arg->val.text, arg->length);
            *xstr_len += arg->length;
            if (arg->type == ARGTYPE_IND_STR) {
                *cmd = CMD_NONE;
                return;
            }
            if (sw_30_94)
                switch_30_and_94(*xstr_buf, *xstr_len);
            
            if (*eq_mode == 0) {
                arg->type = ARGTYPE_XSTR;
                arg->length = *xstr_len;
                arg->val.xstr = *xstr_buf;
            } else {
                /* Imported equation */

                /* Queue up equation, to be parsed later and inserted into the code */
                pending_equation *peq = (pending_equation *) malloc(sizeof(pending_equation));
                if (peq == NULL)
                    goto no_mem;
                
                if (*after_end) {
                    goto_dot_dot(force_new);
                    *after_end = false;
                }

                peq->idx = current_prgm;
                peq->pc = pc;
                peq->length = *xstr_len;
                peq->text = *xstr_buf;
                peq->compatMode = *eq_mode == 2 || *eq_mode == 4;
                peq->eval = *eq_mode == 3 || *eq_mode == 4;
                peq->next = eq_queue;
                eq_queue = peq;

                *xstr_buf = NULL;
                *xstr_len = 0;
                *cmd = CMD_NONE;
            }
        }
    } else {
        /* Parameterized HP-42S extension */
        if (byte1 == 0xf1) {
            switch (byte2) {
                case 0xd5: *cmd = CMD_FIX; arg->val.num = 10; break;
                case 0xd6: *cmd = CMD_SCI; arg->val.num = 10; break;
                case 0xd7: *cmd = CMD_ENG; arg->val.num = 10; break;
                case 0xe5: *cmd = CMD_FIX; arg->val.num = 11; break;
                case 0xe6: *cmd = CMD_SCI; arg->val.num = 11; break;
                case 0xe7: *cmd = CMD_ENG; arg->val.num = 11; break;
                default: goto xrom_string;
            }
            arg->type = ARGTYPE_NUM;
            return;
        }
        if (byte2 == 0xa7) {
            byte2 = buf[pos++];
            byte1--;
            extra_extension = true;
        }
        *cmd = hp42ext[byte2];
        int flag = *cmd >> 12;
        *cmd &= 0x0fff;
        if (flag == 0 || flag == 1) {
            arg->type = flag == 0 ? ARGTYPE_STR
                                    : ARGTYPE_IND_STR;
            str_len = byte1 - 0xf1;
            extra_extension = false;
            goto do_string;
        } else if (flag == 2) {
            if (byte1 != 0xf2)
                goto xrom_string;
            int suffix = buf[pos++];
            decode_suffix(*cmd, suffix, arg);
        } else if (flag == 3) {
            int key;
            if (byte2 == 0xc0) {
                /* ASSIGN */
                str_len = byte1 - 0xf2;
                assign = 1;
                *cmd = CMD_ASGN01;
                arg->type = ARGTYPE_STR;
                goto do_string;
            } else if (byte2 == 0xc2 || byte2 == 0xc3
                    || byte2 == 0xca || byte2 == 0xcb) {
                /* KEYG/KEYX name, KEYG/KEYX IND name */
                str_len = byte1 - 0xf2;
                if (str_len == 0)
                    goto xrom_string;
                *cmd = byte2 == 0xc2 || byte2 == 0xca
                        ? CMD_KEY1X : CMD_KEY1G;
                key = buf[pos++];
                if (key < 1 || key > 9) {
                    /* Treat as plain string. Alas, it is
                     * not safe to back up 2 positions, so
                     * I do the whole thing here.
                     */
                    int i;
                    bad_keyg_keyx:
                    *cmd = CMD_STRING;
                    arg->type = ARGTYPE_STR;
                    arg->length = str_len + 2;
                    arg->val.text[0] = byte2;
                    arg->val.text[1] = key;
                    for (i = 2; i < arg->length; i++)
                        arg->val.text[i] = buf[pos++];
                    if (sw_30_94)
                        switch_30_and_94(arg->val.text, arg->length);
                    return;
                }
                *cmd += key - 1;
                arg->type = byte2 == 0xc2 || byte2 == 0xc3
                            ? ARGTYPE_STR : ARGTYPE_IND_STR;
                goto do_string;
            } else if (byte2 == 0xe2 || byte2 == 0xe3) {
                /* KEYG/KEYX suffix */
                if (byte1 != 0xf3)
                    goto xrom_string;
                key = buf[pos++];
                if (key < 1 || key > 9)
                    goto bad_keyg_keyx;
                *cmd = byte2 == 0xe2 ? CMD_KEY1X : CMD_KEY1G;
                *cmd += key - 1;
                int suffix = buf[pos++];
                decode_suffix(*cmd, suffix, arg);
            } else if (byte2 == 0x32 || byte2 == 0x33) {
                /* GTOL/XEQL */
                *cmd = byte2 == 0x32 ? CMD_GTOL : CMD_XEQL;
                two_byte_num:
                if (byte1 != 0xf3)
                    goto xrom_string;
                int hi = buf[pos++];
                int lo = buf[pos++];
                int sz = (hi << 8) | lo;
                arg->type = ARGTYPE_NUM;
                arg->val.num = sz;
            } else if (byte2 == 0x76 || byte2 == 0x7e) {
                /* EMBED */
                if (byte1 != 0xf5)
                    goto xrom_string;
                int4 id = 0;
                for (int i = 0; i < 4; i++)
                    id = (id << 8) | buf[pos++];
                if (id == -1) {
                    *eq_mode = byte2 == 0x76 ? 1 : 3;
                    *cmd = CMD_NONE;
                } else if (id == -2) {
                    *eq_mode = byte2 == 0x76 ? 2 : 4;
                    *cmd = CMD_NONE;
                } else if (id < 0 || !loading_state) {
                    *cmd = CMD_XSTR;
                    arg->type = ARGTYPE_XSTR;
                    arg->length = 18;
                    arg->val.xstr = "<Missing Equation>";
                } else {
                    *cmd = CMD_EMBED;
                    arg->type = byte2 == 0x76 ? ARGTYPE_NUM : ARGTYPE_IND_NUM;
                    arg->val.num = id;
                }
            } else /* byte2 == 0xf7 */ {
                /* SIZE */
                *cmd = CMD_SIZE;
                goto two_byte_num;
            }
        } else /* flag == 4 */ {
            /* Unknown value; store as string XROM */
            goto xrom_string;
        }
    }

    if (sw_30_94 && (arg->type == ARGTYPE_STR || arg->type == ARGTYPE_IND_STR))
        switch_30_and_94(arg->val.text, arg->length);
}

// From core_globals.cc: version of state being imported
extern int4 ver;

void core_import_programs(int num_progs, const char *raw_file_name) {
    int byte1, byte2, suffix;
    int cmd, flag, str_len;
    int done_flag = 0;
    arg_struct arg;
    bool pending_end;
    int eq_mode = 0;

    if (raw_file_name != NULL) {
#ifdef IPHONE
        if (strncmp(raw_file_name, "mem:", 4) == 0) {
            char *buf;
            ssize_t size;
            memcpy(&buf, raw_file_name + 5, sizeof(char *));
            memcpy(&size, raw_file_name + 13, sizeof(ssize_t));
            gfile = fmemopen(buf, size, "rb");
        } else {
#endif
            gfile = my_fopen(raw_file_name, "rb");
            if (gfile == NULL) {
                char msg[1024];
                int err = errno;
                snprintf(msg, 1024, "Could not open \"%s\" for reading: %s (%d)", raw_file_name, strerror(err), err);
                shell_message(msg);
                return;
            }
#ifdef IPHONE
        }
#endif
    }

    set_running(false);
    if (!loading_state)
        clear_all_rtns();

    /* Set print mode to MAN during the import, to prevent store_command()
     * from printing programs as they load
     */
    int saved_trace = flags.f.trace_print;
    int saved_normal = flags.f.normal_print;
    flags.f.trace_print = 0;
    flags.f.normal_print = 0;

    if (loading_state) {
        goto_dot_dot(true);
        pending_end = false;
    } else {
        current_prgm.set(cwd->id, cwd->prgms_count - 1);
        // No initial END needed if last program is empty
        pending_end = cwd->prgms[current_prgm.idx].size > 2;
        if (!pending_end)
            pc = -1;
    }

    char numbuf[50];
    char *xstr_buf = NULL;
    int xstr_len = 0;

    while (!done_flag) {
        skip:
        byte1 = fgetc(gfile);
        if (byte1 == EOF)
            goto done;
        cmd = hp42tofree42[byte1];
        flag = cmd >> 12;
        cmd &= 0x0fff;
        if (flag == 0) {
            arg.type = ARGTYPE_NONE;
        } else if (flag == 1) {
            arg.type = ARGTYPE_NUM;
            arg.val.num = byte1 & 15;
            if (cmd == CMD_LBL)
                arg.val.num--;
        } else if (flag == 2) {
            suffix = fgetc(gfile);
            if (suffix == EOF)
                goto done;
            decode_suffix(cmd, suffix, &arg);
        } else /* flag == 3 */ {
            if (byte1 == 0x00)
                /* NULL */
                goto skip;
            else if (byte1 >= 0x10 && byte1 <= 0x1c) {
                /* Number */
                int numlen = 0;
                do {
                    if (byte1 == 0x1a)
                        byte1 = '.';
                    else if (byte1 == 0x1b)
                        byte1 = 'E';
                    else if (byte1 == 0x1c)
                        byte1 = '-';
                    else
                        byte1 += '0' - 0x10;
                    numbuf[numlen++] = byte1;
                    byte1 = fgetc(gfile);
                } while (byte1 >= 0x10 && byte1 <= 0x1c);
                if (byte1 == EOF)
                    done_flag = 1;
                else if (byte1 != 0x00)
                    ungetc(byte1, gfile);
                numbuf[numlen++] = 0;
                parse_number_line(numbuf, &arg.val_d);
                cmd = CMD_NUMBER;
                arg.type = ARGTYPE_DOUBLE;
            } else if (byte1 == 0x1d || byte1 == 0x1e) {
                cmd = byte1 == 0x1d ? CMD_GTO : CMD_XEQ;
                str_len = fgetc(gfile);
                if (str_len == EOF)
                    goto done;
                else if (str_len < 0xf1) {
                    ungetc(str_len, gfile);
                    goto skip;
                } else
                    str_len -= 0xf0;
                arg.type = ARGTYPE_STR;
                do_string:
                for (int i = 0; i < str_len; i++) {
                    suffix = fgetc(gfile);
                    if (suffix == EOF)
                        goto done;
                    arg.val.text[i] = suffix;
                }
                arg.length = str_len;
                if (raw_file_name == NULL && ver < 44)
                    switch_30_and_94(arg.val.text, arg.length);
            } else if (byte1 == 0x1f) {
                /* "W" function (see HP-41C instruction table */
                goto skip;
            } else if (byte1 >= 0xa0 && byte1 <= 0xa7) {
                /* XROM mm,nn */
                byte2 = fgetc(gfile);
                if (byte2 == EOF)
                    goto done;
                decode_xrom(byte1, byte2, &cmd, &arg);
            } else if (byte1 == 0xae) {
                /* GTO/XEQ IND */
                suffix = fgetc(gfile);
                if (suffix == EOF)
                    goto done;
                if ((suffix & 0x80) != 0)
                    cmd = CMD_XEQ;
                else {
                    cmd = CMD_GTO;
                    suffix |= 0x80;
                }
                decode_suffix(cmd, suffix, &arg);
            } else if (byte1 == 0xaf || byte1 == 0xb0) {
                /* SPARE functions (see HP-41C instruction table */
                goto skip;
            } else if (byte1 >= 0xb1 && byte1 <= 0xbf) {
                /* 2-byte GTO */
                byte2 = fgetc(gfile);
                if (byte2 == EOF)
                    goto done;
                cmd = CMD_GTO;
                arg.type = ARGTYPE_NUM;
                arg.val.num = (byte1 & 15) - 1;
            } else if (byte1 >= 0xc0 && byte1 <= 0xcd) {
                /* GLOBAL */
                byte2 = fgetc(gfile);
                if (byte2 == EOF)
                    goto done;
                str_len = fgetc(gfile);
                if (str_len == EOF)
                    goto done;
                if (str_len < 0xf1) {
                    /* END */
                    cmd = CMD_END;
                    arg.type = ARGTYPE_NONE;
                } else {
                    /* LBL "" */
                    str_len -= 0xf1;
                    byte2 = fgetc(gfile);
                    if (byte2 == EOF)
                        goto done;
                    cmd = CMD_LBL;
                    arg.type = ARGTYPE_STR;
                    goto do_string;
                }
            } else if (byte1 >= 0xd0 && byte1 <= 0xef) {
                /* 3-byte GTO & XEQ */
                byte2 = fgetc(gfile);
                if (byte2 == EOF)
                    goto done;
                suffix = fgetc(gfile);
                if (suffix == EOF)
                    goto done;
                cmd = byte1 <= 0xdf ? CMD_GTO : CMD_XEQ;
                suffix &= 0x7f;
                decode_suffix(cmd, suffix, &arg);
            } else /* byte1 >= 0xf1 && byte1 <= 0xff */ {
                /* Strings and parameterized HP-42S extensions */
                unsigned char buf[16];
                buf[0] = byte1;
                str_len = byte1 - 0xf0;
                for (int i = 0; i < str_len; i++) {
                    int c = fgetc(gfile);
                    if (c == EOF)
                        goto done;
                    buf[i + 1] = c;
                }
                decode_string(buf, &cmd, &arg, &xstr_buf, &xstr_len, &eq_mode, &pending_end, true, raw_file_name == NULL && ver < 44);
                if (cmd == CMD_CANCELLED)
                    goto done;
                if (cmd == CMD_NONE)
                    continue;
            }
        }
        if (pending_end) {
            goto_dot_dot(true);
            pending_end = false;
        }
        eq_mode = 0;
        if (cmd == CMD_END) {
            if (num_progs > 0 && --num_progs == 0)
                break;
            pending_end = true;
        } else {
            store_command_after(&pc, cmd, &arg, numbuf);
            free(xstr_buf);
            xstr_buf = NULL;
            xstr_len = 0;
        }
    }

    done:
    if (!loading_state) {
        rebuild_label_table();
        update_catalog();
    }

    flags.f.trace_print = saved_trace;
    flags.f.normal_print = saved_normal;

    if (raw_file_name != NULL) {
        if (ferror(gfile))
            shell_message("An error occurred during program import.");
        fclose(gfile);
    }
    free(xstr_buf);

    handle_pending_equations();
}

static int complex2buf(char *buf, phloat re, phloat im, bool always_rect, const char *format = NULL) {
    bool polar = !always_rect && flags.f.polar;
    phloat x, y;
    if (polar) {
        generic_r2p(re, im, &x, &y);
        if (p_isinf(x))
            x = POS_HUGE_PHLOAT;
    } else {
        x = re;
        y = im;
    }
    int bufptr = phloat2string(x, buf, 99, 0, 0, 3, 0, MAX_MANT_DIGITS, format);
    if (polar) {
        string2buf(buf, 99, &bufptr, " \342\210\240 ", 5);
    } else {
        if (y >= 0 || p_isinf(y) != 0 || p_isnan(y))
            buf[bufptr++] = '+';
    }
    bufptr += phloat2string(y, buf + bufptr, 99 - bufptr, 0, 0, 3, 0, MAX_MANT_DIGITS, format);
    if (!polar)
        buf[bufptr++] = 'i';
    /* Convert small-caps 'E' to regular 'e' */
    for (int i = 0; i < bufptr; i++)
        if (buf[i] == 24)
            buf[i] = 'e';
    return bufptr;
}

static void serialize_list(textbuf *tb, vartype_list *list, int indent) {
    char buf[50];
    tb_indent(tb, indent);
    tb_write(tb, "{\n", 2);
    indent += 2;
    tb_indent(tb, indent);
    int n = int2string(list->size, buf, 49);
    tb_write(tb, buf, n);
    tb_write(tb, "-Elem List\n", 11);
    for (int i = 0; i < list->size; i++) {
        vartype *elem = list->array->data[i];
        switch (elem->type) {
            case TYPE_NULL: {
                tb_indent(tb, indent);
                tb_write(tb, "null\n", 5);
                break;
            }
            case TYPE_REAL: {
                vartype_real *r = (vartype_real *) elem;
                tb_indent(tb, indent);
                n = real2buf(buf, r->x);
                tb_write(tb, buf, n);
                tb_write(tb, "\n", 1);
                break;
            }
            case TYPE_COMPLEX: {
                vartype_complex *c = (vartype_complex *) elem;
                tb_indent(tb, indent);
                n = complex2buf(buf, c->re, c->im, true);
                tb_write(tb, buf, n);
                tb_write(tb, "\n", 1);
                break;
            }
            case TYPE_STRING:
            case TYPE_EQUATION: {
                const char *text;
                int length;
                char d;
                if (elem->type == TYPE_STRING) {
                    vartype_string *s = (vartype_string *) elem;
                    text = s->txt();
                    length = s->length;
                    d = '"';
                } else {
                    vartype_equation *eq = (vartype_equation *) elem;
                    equation_data *eqd = eq->data;
                    text = eqd->text;
                    length = eqd->length;
                    d = eqd->compatMode ? '`' : '\'';
                }
                tb_indent(tb, indent);
                tb_write(tb, &d, 1);
                char cbuf[5];
                for (int j = 0; j < length; j++) {
                    unsigned char c = text[j];
                    if (c == 10)
                        c = 138;
                    else if (undefined_char(c))
                        c &= 127;
                    if (c == d) {
                        tb_write(tb, "\\", 1);
                        tb_write(tb, &d, 1);
                    } else if (c == '\\') {
                        tb_write(tb, "\\\\", 2);
                    } else {
                        n = hp2ascii(cbuf, (const char *) &c, 1);
                        tb_write(tb, cbuf, n);
                    }
                }
                tb_write(tb, &d, 1);
                tb_write(tb, "\n", 1);
                break;
            }
            case TYPE_REALMATRIX: {
                vartype_realmatrix *rm = (vartype_realmatrix *) elem;
                tb_indent(tb, indent);
                tb_write(tb, "[\n", 2);
                indent += 2;
                tb_indent(tb, indent);
                n = int2string(rm->rows, buf, 49);
                tb_write(tb, buf, n);
                tb_write(tb, "x", 1);
                n = int2string(rm->columns, buf, 49);
                tb_write(tb, buf, n);
                tb_write(tb, " Matrix\n", 8);
                for (int j = 0; j < rm->rows * rm->columns; j++) {
                    tb_indent(tb, indent);
                    if (rm->array->is_string[j]) {
                        tb_write(tb, "\"", 1);
                        char *text;
                        int4 len;
                        get_matrix_string(rm, j, &text, &len);
                        char cbuf[5];
                        for (int k = 0; k < len; k++) {
                            unsigned char c = text[k];
                            if (c == 10)
                                c = 138;
                            else if (undefined_char(c))
                                c &= 127;
                            if (c == '"') {
                                tb_write(tb, "\\\"", 2);
                            } else if (c == '\\') {
                                tb_write(tb, "\\\\", 2);
                            } else {
                                n = hp2ascii(cbuf, (const char *) &c, 1);
                                tb_write(tb, cbuf, n);
                            }
                        }
                        tb_write(tb, "\"\n", 2);
                    } else {
                        n = real2buf(buf, rm->array->data[j]);
                        tb_write(tb, buf, n);
                        tb_write(tb, "\n", 1);
                    }
                }
                indent -= 2;
                tb_indent(tb, indent);
                tb_write(tb, "]\n", 2);
                break;
            }
            case TYPE_COMPLEXMATRIX: {
                vartype_complexmatrix *cm = (vartype_complexmatrix *) elem;
                tb_indent(tb, indent);
                tb_write(tb, "[\n", 2);
                indent += 2;
                tb_indent(tb, indent);
                n = int2string(cm->rows, buf, 49);
                tb_write(tb, buf, n);
                tb_write(tb, "x", 1);
                n = int2string(cm->columns, buf, 49);
                tb_write(tb, buf, n);
                tb_write(tb, " Cpx Matrix\n", 12);
                for (int j = 0; j < cm->rows * cm->columns * 2; j += 2) {
                    tb_indent(tb, indent);
                    n = complex2buf(buf, cm->array->data[j], cm->array->data[j + 1], true);
                    tb_write(tb, buf, n);
                    tb_write(tb, "\n", 1);
                }
                indent -= 2;
                tb_indent(tb, indent);
                tb_write(tb, "]\n", 2);
                break;
            }
            case TYPE_LIST: {
                serialize_list(tb, (vartype_list *) elem, indent);
                break;
            }
            case TYPE_UNIT: {
                vartype_unit *u = (vartype_unit *) elem;
                tb_indent(tb, indent);
                n = real2buf(buf, u->x);
                tb_write(tb, buf, n);
                tb_write(tb, "_", 1);
                char cbuf[5];
                for (int k = 0; k < u->length; k++) {
                    unsigned char c = u->text[k];
                    n = hp2ascii(cbuf, (const char *) &c, 1);
                    tb_write(tb, cbuf, n);
                }
                tb_write(tb, "\n", 1);
                break;
            }
            case TYPE_DIR_REF: {
                tb_indent(tb, indent);
                tb_write(tb, "\"DIR_REF\"\n", 10);
                break;
            }
            case TYPE_PGM_REF: {
                tb_indent(tb, indent);
                tb_write(tb, "\"PGM_REF\"\n", 10);
                break;
            }
            case TYPE_VAR_REF: {
                tb_indent(tb, indent);
                tb_write(tb, "\"VAR_REF\"\n", 10);
                break;
            }
        }
    }
    indent -= 2;
    tb_indent(tb, indent);
    tb_write(tb, "}\n", 2);
}

char *core_copy() {
    if (eqn_active())
        return eqn_copy();

    if (mode_interruptible != NULL)
        stop_interruptible();
    set_running(false);

    textbuf tb;
    tb.buf = NULL;
    tb.size = 0;
    tb.capacity = 0;
    tb.fail = false;

    if (flags.f.prgm_mode) {
        tb_print_current_program(&tb);
        textbuf_finish:
        tb_write_null(&tb);
        if (tb.fail) {
            free(tb.buf);
            display_error(ERR_INSUFFICIENT_MEMORY);
            redisplay();
            return NULL;
        } else
            return tb.buf;
    } else if (alpha_active()) {
        char *buf = (char *) malloc(5 * reg_alpha_length + 1);
        int bufptr = hp2ascii(buf, reg_alpha, reg_alpha_length);
        buf[bufptr] = 0;
        return buf;
    } else if (sp == -1) {
        char *buf = (char *) malloc(1);
        buf[0] = 0;
        return buf;
    } else if (stack[sp]->type == TYPE_REAL) {
        const char *format = core_settings.localized_copy_paste ? number_format() : NULL;
        char *buf = (char *) malloc(50);
        int bufptr = real2buf(buf, ((vartype_real *) stack[sp])->x, format, false);
        buf[bufptr] = 0;
        return buf;
    } else if (stack[sp]->type == TYPE_COMPLEX) {
        const char *format = core_settings.localized_copy_paste ? number_format() : NULL;
        char *buf = (char *) malloc(100);
        vartype_complex *c = (vartype_complex *) stack[sp];
        int bufptr = complex2buf(buf, c->re, c->im, false, format);
        buf[bufptr] = 0;
        return buf;
    } else if (stack[sp]->type == TYPE_STRING) {
        vartype_string *s = (vartype_string *) stack[sp];
        char *buf = (char *) malloc(5 * s->length + 1);
        int bufptr = hp2ascii(buf, s->txt(), s->length);
        buf[bufptr] = 0;
        return buf;
    } else if (stack[sp]->type == TYPE_REALMATRIX) {
        const char *format = core_settings.localized_copy_paste ? number_format() : NULL;
        vartype_realmatrix *rm = (vartype_realmatrix *) stack[sp];
        phloat *data = rm->array->data;
        char *is_string = rm->array->is_string;
        char buf[50];
        int n = 0;
        for (int r = 0; r < rm->rows; r++) {
            for (int c = 0; c < rm->columns; c++) {
                int bufptr;
                if (is_string[n] == 0) {
                    bufptr = real2buf(buf, data[n], format);
                    tb_write(&tb, buf, bufptr);
                } else {
                    char *text;
                    int4 len;
                    get_matrix_string(rm, n, &text, &len);
                    for (int4 i = 0; i < len; i += 10) {
                        int4 seg_len = len - i;
                        if (seg_len > 10)
                            seg_len = 10;
                        bufptr = hp2ascii(buf, text + i, seg_len);
                        tb_write(&tb, buf, bufptr);
                    }
                }
                if (c < rm->columns - 1)
                    tb_write(&tb, "\t", 1);
                n++;
            }
            if (r < rm->rows - 1)
                tb_write(&tb, "\n", 1);
        }
        goto textbuf_finish;
    } else if (stack[sp]->type == TYPE_COMPLEXMATRIX) {
        const char *format = core_settings.localized_copy_paste ? number_format() : NULL;
        vartype_complexmatrix *cm = (vartype_complexmatrix *) stack[sp];
        phloat *data = cm->array->data;
        char buf[100];
        int n = 0;
        for (int r = 0; r < cm->rows; r++) {
            for (int c = 0; c < cm->columns; c++) {
                int bufptr = complex2buf(buf, data[n], data[n + 1], true, format);
                if (c < cm->columns - 1)
                    buf[bufptr++] = '\t';
                tb_write(&tb, buf, bufptr);
                n += 2;
            }
            if (r < cm->rows - 1)
                tb_write(&tb, "\n", 1);
        }
        goto textbuf_finish;
    } else if (stack[sp]->type == TYPE_LIST) {
        serialize_list(&tb, (vartype_list *) stack[sp], 0);
        goto textbuf_finish;
    } else if (stack[sp]->type == TYPE_EQUATION) {
        vartype_equation *eq = (vartype_equation *) stack[sp];
        equation_data *eqd = eq->data;
        char *buf = (char *) malloc(5 * eqd->length + 1);
        int bufptr = hp2ascii(buf, eqd->text, eqd->length);
        buf[bufptr] = 0;
        return buf;
    } else if (stack[sp]->type == TYPE_UNIT) {
        const char *format = core_settings.localized_copy_paste ? number_format() : NULL;
        vartype_unit *u = (vartype_unit *) stack[sp];
        char *buf = (char *) malloc(50 + u->length);
        if (buf == NULL) {
            display_error(ERR_INSUFFICIENT_MEMORY);
            redisplay();
            return NULL;
        }
        int bufptr = real2buf(buf, u->x, format);
        buf[bufptr++] = ' ';
        bufptr += hp2ascii(buf + bufptr, u->text, u->length);
        buf[bufptr] = 0;
        return buf;
    } else if (stack[sp]->type == TYPE_DIR_REF || stack[sp]->type == TYPE_PGM_REF || stack[sp]->type == TYPE_VAR_REF) {
        char *buf = (char *) malloc(8);
        if (buf != NULL) {
            switch (stack[sp]->type) {
                case TYPE_DIR_REF: strcpy(buf, "DIR_REF"); break;
                case TYPE_PGM_REF: strcpy(buf, "PGM_REF"); break;
                case TYPE_VAR_REF: strcpy(buf, "VAR_REF"); break;
            }
        }
        return buf;
    } else {
        // Shouldn't happen: unrecognized data type
        return NULL;
    }
}

const char *STR_INF = "<Infinity>";
const char *STR_NEG_INF = "<-Infinity>";
const char *STR_NAN = "<Not a Number>";

static int scan_number(const char *buf, int len, int pos, const char *format, bool no_sep = false) {
    if (buf[pos] == '<' || len > 1 && (buf[pos] == '-' || buf[pos] == '+') && buf[pos + 1] == '<') {
        int off = buf[pos] == '<' ? 0 : 1;
        if (len >= 10 + off && strncmp(buf + pos + off, STR_INF, 10) == 0)
            return pos + off + 10;
        else if (len >= 11 + off && strncmp(buf + pos + off, STR_NEG_INF, 11) == 0)
            return pos + off + 11;
        else if (len >= 14 + off && strncmp(buf + pos + off, STR_NAN, 14) == 0)
            return pos + off + 14;
        else
            return pos;
    }
    // 0: before number
    // 1: in mantissa, before decimal
    // 2: in mantissa, after decimal
    // 3: after E
    // 4: in exponent
    int state = 0;
    char dec, sep;
    if (format == NULL) {
        dec = flags.f.decimal_point ? '.' : ',';
        sep = flags.f.decimal_point ? ',' : '.';
    } else {
        dec = format[0];
        sep = format[1];
    }
    for (int p = pos; p < len; p++) {
        char c = buf[p];
        switch (state) {
            case 0:
                if (c >= '0' && c <= '9' || c == '+' || c == '-')
                    state = 1;
                else if (c == dec)
                    state = 2;
                else if (c == 'e' || c == 'E' || c == 24)
                    state = 3;
                else
                    return p;
                break;
            case 1:
                if (c >= '0' && c <= '9' || !no_sep && (c == sep || c == ' '))
                    /* state = 1 */;
                else if (c == dec)
                    state = 2;
                else if (c == 'e' || c == 'E' || c == 24)
                    state = 3;
                else
                    return p;
                break;
            case 2:
                if (c >= '0' && c <= '9')
                    /* state = 2 */;
                else if (c == 'e' || c == 'E' || c == 24)
                    state = 3;
                else
                    return p;
                break;
            case 3:
                if ((c >= '0' && c <= '9')
                        || c == '+' || c == '-')
                    state = 4;
                else
                    return p;
                break;
            case 4:
                if (c >= '0' && c <= '9')
                    /* state = 4 */;
                else
                    return p;
                break;
        }
    }
    return len;
}

static bool parse_phloat(const char *p, int len, phloat *res, const char *format) {
    if (p[0] == '<' || len > 1 && (p[0] == '-' || p[0] == '+') && p[1] == '<') {
        int off = p[0] == '<' ? 0 : 1;
        bool neg = p[0] == '-';
        if (len >= 10 + off && strncmp(p + off, STR_INF, 10) == 0) {
            goto return_inf;
        } else if (len >= 11 + off && strncmp(p + off, STR_NEG_INF, 11) == 0) {
            neg = !neg;
            return_inf:
            *res = (neg ? NEG_HUGE_PHLOAT : POS_HUGE_PHLOAT) * 2;
            return true;
        } else if (len >= 14 + off && strncmp(p + off, STR_NAN, 14) == 0) {
            *res = NAN_PHLOAT;
            return true;
        } else
            return false;
    }
    // We can't pass the string on to string2phloat() unchanged, because
    // that function is picky: it does not allow '+' signs, and it does
    // not allow the mantissa to be more than 34 or 16 digits long (including
    // leading zeroes). So, we massage the string a bit to make it
    // comply with those restrictions.
    // Note that this function does not check well-formedness;
    // that part should be checked beforehand using scan_number().
    const size_t BSIZE = 100;
    char buf[BSIZE];
    bool in_mant = true;
    bool leading_zero = true;
    int exp_offset = 0;
    int exp = 0;
    bool neg_exp = false;
    int mant_digits = 0;
    bool in_int_mant = true;
    bool empty_mant = true;
    int i = 0, j = 0;
    char decimal, separator;
    if (format == NULL) {
        decimal = flags.f.decimal_point ? '.' : ',';
        separator = flags.f.decimal_point ? ',' : '.';
    } else {
        decimal = format[0];
        separator = format[1];
    }
    while (i < BSIZE - 1 && j < len) {
        char c = p[j++];
        if (c == 0)
            break;
        if (c == '+' || c == ' ' || c == separator) {
            continue;
        } else if (c == 'e' || c == 'E' || c == 24) {
            if (!empty_mant && mant_digits == 0)
                buf[i++] = '0';
            in_mant = false;
        } else if (c == decimal) {
            in_int_mant = false;
            buf[i++] = flags.f.decimal_point ? '.' : ',';
        } else if (c >= '0' && c <= '9') {
            if (in_mant) {
                empty_mant = false;
                if (in_int_mant) {
                    if (mant_digits < MAX_MANT_DIGITS) {
                        if (c != '0' || !leading_zero) {
                            buf[i++] = c;
                            leading_zero = false;
                            mant_digits++;
                        }
                    } else {
                        exp_offset++;
                    }
                } else {
                    if (mant_digits < MAX_MANT_DIGITS) {
                        if (c != '0' || !leading_zero) {
                            buf[i++] = c;
                            leading_zero = false;
                            mant_digits++;
                        } else {
                            exp_offset--;
                        }
                    }
                }
            } else {
                exp = exp * 10 + c - '0';
            }
        } else if (c == '-') {
            if (in_mant)
                buf[i++] = c;
            else
                neg_exp = true;
        }
    }
    if (in_mant && empty_mant)
        return false;
    if (in_mant && mant_digits == 0 && i < BSIZE - 1)
        buf[i++] = '0';
    if (neg_exp)
        exp = -exp;
    exp += exp_offset;
    if (exp != 0) {
        i += snprintf(buf + i, BSIZE - i, "\030%d", exp);
        if (i > BSIZE - 1)
            i = BSIZE - 1;
    }
    if (i == 0)
        return false;
    int err = string2phloat(buf, i, res);
    if (err == 0)
        return true;
    else if (err == 1) {
        *res = POS_HUGE_PHLOAT;
        return true;
    } else if (err == 2) {
        *res = NEG_HUGE_PHLOAT;
        return true;
    } else if (err == 3 || err == 4) {
        *res = 0;
        return true;
    } else
        return false;
}
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
