barnabyosborne-cmyk/Hp42s_calc/firmware/components/plus42core/core_keydown.cc

/*****************************************************************************
 * Plus42 -- an enhanced HP-42S calculator simulator
 * Copyright (C) 2004-2026  Thomas Okken
 *
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
 * You should have received a copy of the GNU General Public License
 * along with this program; if not, see http://www.gnu.org/licenses/.
 *****************************************************************************/

#include <stdlib.h>
#include <string.h>

#include "core_keydown.h"
#include "core_commands2.h"
#include "core_commands3.h"
#include "core_commands4.h"
#include "core_commands8.h"
#include "core_commands9.h"
#include "core_commandsa.h"
#include "core_display.h"
#include "core_equations.h"
#include "core_helpers.h"
#include "core_main.h"
#include "core_math1.h"
#include "core_tables.h"
#include "core_variables.h"
#include "shell.h"


// Buffer used to pass LBL name, for direct XEQ "LBL" mapping
char dcm_lbl[8];

static void handle_dcm_xeq() {
    pending_command = CMD_XEQ;
    pending_command_arg.type = ARGTYPE_STR;
    pending_command_arg.length = dcm_lbl[0];
    for (int i = 0; i < pending_command_arg.length; i++)
        pending_command_arg.val.text[i] = dcm_lbl[i + 1];
    if (flags.f.prgm_mode) {
        if (!current_prgm.is_editable()) {
            display_error(ERR_RESTRICTED_OPERATION);
        } else if (current_prgm.is_locked()) {
            display_error(ERR_PROGRAM_LOCKED);
        } else {
            store_command_after(&pc, pending_command,
                                        &pending_command_arg, NULL);
            move_prgm_highlight(1);
        }
        pending_command = CMD_NONE;
        redisplay();
    }
}

static bool is_number_key(int shift, int key, bool *invalid) {
    *invalid = false;
    if (get_front_menu() == MENU_BASE_A_THRU_F
            && (key == KEY_SIGMA || key == KEY_INV || key == KEY_SQRT
                || key == KEY_LOG || key == KEY_LN || key == KEY_XEQ))
        return true;
    if (shift)
        return false;
    if (key == KEY_0 || key == KEY_1)
        return true;
    int base = get_base();
    if (key == KEY_DOT || key == KEY_E) {
        *invalid = base != 10;
        return true;
    }
    if (key == KEY_2 || key == KEY_3 || key == KEY_4
            || key == KEY_5 || key == KEY_6 || key == KEY_7) {
        *invalid = base == 2;
        return true;
    }
    if (key == KEY_8 || key == KEY_9) {
        *invalid = base == 2 || base == 8;
        return true;
    }
    return false;
}

static bool basekeys() {
    if (!baseapp)
        return false;
    int menu = get_front_menu();
    return menu >= MENU_BASE1 && menu <= MENU_BASE_DISP;
}

static void set_solve_integ(int solve) {
    if (solve)
        print_menu_trace("SOLVER", 6);
    else
        print_menu_trace("\3f(x)", 5);
    if (flags.f.prgm_mode || !mvar_prgms_exist()) {
        set_menu(MENULEVEL_APP, solve ? MENU_SOLVE : MENU_INTEG);
        if (!flags.f.prgm_mode)
            display_error(ERR_NO_MENU_VARIABLES);
    } else {
        int err = set_menu_return_err(MENULEVEL_APP, MENU_CATALOG, false);
        if (err == ERR_NONE) {
            set_cat_section(solve ? CATSECT_PGM_SOLVE : CATSECT_PGM_INTEG);
            move_cat_row(0);
            if (solve)
                draw_message(0, "Select Solve Program", 20, false);
            else
                draw_message(0, "Select \3f(x) Program", 20, false);
        } else
            display_error(err);
    }
    redisplay();
}

static void view(const char *varname, int varlength) {
    arg_struct arg;
    int i, err;
    arg.type = ARGTYPE_STR;
    arg.length = varlength;
    for (i = 0; i < varlength; i++)
        arg.val.text[i] = varname[i];
    err = view_helper(&arg, 0);
    if (err != ERR_NONE) {
        display_error(err);
        flush_display();
        pending_command = CMD_NONE;
    } else {
        clear_message();
        pending_command = CMD_LINGER1;
        shell_request_timeout3(2000);
    }
}

struct cmd_getkey_mapping_struct {
    int2 key;
    int2 cmd;
};

static cmd_getkey_mapping_struct cmd_getkey_mapping[] = {
    {  1, CMD_SIGMAADD },
    {  2, CMD_INV },
    {  3, CMD_SQRT },
    {  4, CMD_LOG },
    {  5, CMD_LN },
    {  6, CMD_XEQ },
    {  7, CMD_STO },
    {  8, CMD_RCL },
    {  9, CMD_RDN },
    { 10, CMD_SIN },
    { 11, CMD_COS },
    { 12, CMD_TAN },
    { 13, CMD_ENTER },
    { 14, CMD_SWAP },
    { 15, CMD_CHS },
    { 22, CMD_DIV },
    { 27, CMD_MUL },
    { 32, CMD_SUB },
    { 37, CMD_ADD },
    { 38, CMD_SIGMASUB },
    { 39, CMD_Y_POW_X },
    { 40, CMD_SQUARE },
    { 41, CMD_10_POW_X },
    { 42, CMD_E_POW_X },
    { 43, CMD_GTO },
    { 44, CMD_COMPLEX },
    { 45, CMD_PERCENT },
    { 46, CMD_PI },
    { 47, CMD_ASIN },
    { 48, CMD_ACOS },
    { 49, CMD_ATAN },
    { 51, CMD_LASTX },
    { 55, CMD_BST },
    { 60, CMD_SST },
    { 66, CMD_ASSIGNa },
    { 70, CMD_OFF },
    {  0, CMD_NONE }
};

int find_cmd_getkey_mapping(int cmd) {
    cmd_getkey_mapping_struct *gm = cmd_getkey_mapping;
    while (true) {
        if (gm->key == 0)
            // Command that's not on the standard keyboard
            return 0;
        else if (gm->cmd == cmd)
            return gm->key;
        gm++;
    }
}

void keydown(int shift, int key) {
    // Preserve state of Shift, to allow MENU handlers to implement
    // different behaviors for unshifted and shifted menu keys.
    flags.f.shift_state = shift;

    pending_command = CMD_NONE;

    if (key >= 1024 && key < 2048) {
        /* TODO: is this actually needed?
         * Filtering out ASCII key events if the alpha menu is not actually
         * active, just in case the subsequent key handling code doesn't
         * handle them properly in all cases. Using a code coverage tool on
         * the keydown handler might be an idea...
         */
        int menu = get_front_menu();
        if (menu < MENU_ALPHA1 || menu > MENU_ALPHA_MISC2)
            return;
    } else if (key < 1 || key > 37 && key < 2048) {
        /* Bad key code */
        squeak();
        return;
    }

    if (mode_clall) {
        if (!shift && key == KEY_SIGMA)
            pending_command = CMD_CLALLb;
        else if (key == KEY_EXIT)
            pending_command = CMD_CANCELLED;
        else
            pending_command = CMD_NULL;
        mode_clall = false;
        return;
    }

    if (mode_getkey) {
        if (key >= 2048) {
            // Direct command mapping
            int cmd = key - 2048;
            key = find_cmd_getkey_mapping(cmd);
            if (key == 0) {
                squeak();
                set_annunciators(-1, -1, -1, 0, -1, -1);
                return;
            }
        } else {
            if (shift)
                key += 37;
        }
        vartype *result = new_real(key);
        if (result != NULL) {
            if (recall_result(result) != ERR_NONE)
                goto nomem;
            flags.f.stack_lift_disable = 0;
        } else {
            nomem:
            display_error(ERR_INSUFFICIENT_MEMORY);
            set_running(false);
        }
        if (key == KEY_RUN || !mode_getkey1 && (key == KEY_EXIT || key == KEY_EXIT + 37))
            set_running(false);
        mode_getkey = false;
        if (!mode_running)
            redisplay();
        return;
    }

    if (shift && key == KEY_EXIT) {
        pending_command = CMD_SILENT_OFF;
        return;
    }

    if (shift && key == KEY_RUN) {
        if (mode_command_entry || mode_number_entry && alpha_active()) {
            squeak();
            return;
        }
        if (flags.f.prgm_mode) {
            if (mode_alpha_entry)
                finish_alpha_prgm_line();
            else if (mode_number_entry) {
                arg_struct arg;
                arg.type = ARGTYPE_DOUBLE;
                arg.val_d = entered_number;
                cmdline[cmdline_length] = 0;
                store_command(pc, CMD_NUMBER, &arg, cmdline);
                move_prgm_highlight(1);
            }
        } else if (mode_alpha_entry) {
            if ((flags.f.trace_print || flags.f.normal_print)
                    && flags.f.printer_exists)
                docmd_pra(NULL);
        } else if (mode_number_entry) {
            if ((flags.f.trace_print || flags.f.normal_print)
                    && flags.f.printer_exists) {
                deferred_print = 1;
                print_command(CMD_NULL, NULL);
            }
        }

        print_menu_trace("PRGM", 4);

        mode_alpha_entry = false;
        mode_number_entry = false;
        flags.f.prgm_mode = !flags.f.prgm_mode;

        mode_varmenu = false;
        if (flags.f.prgm_mode) {
            if (mode_appmenu == MENU_BASE_A_THRU_F)
                set_menu(MENULEVEL_APP, MENU_BASE1);
            else if (mode_plainmenu == MENU_PROGRAMMABLE)
                set_menu(MENULEVEL_PLAIN, MENU_NONE);
            input_length = 0;
        }
        clear_message();
        redisplay();
        return;
    }

    if (mode_message_lines > 0 && !shift && key == KEY_BSP) {
        clear_message();
        redisplay();
        return;
    }

    clear_message();

    if (mode_number_entry && get_base() == 16 && key == KEY_SIGMA
            && get_front_menu() == MENU_BASE1) {
        /* Special case -- entering the A...F menu while in base 16
         * does *not* cancel number entry mode (unlike all other menu
         * keys)... So we intercept and handle it before all the other
         * logic can mess things up.
         */
        keydown_number_entry(-1, -1);
        return;
    }

    bool invalid;
    if (mode_number_entry
            && !is_number_key(shift, key, &invalid)
            && (key != KEY_CHS || shift || basekeys() || get_base() != 10)
            && (key != KEY_BSP || shift)
            // starting attached unit
            && (key != KEY_DOT || !shift || get_base() != 10)
            // entering an attached unit
            && (key == KEY_ENTER || !alpha_active())) {
        if (invalid)
            return;
        /* Leaving number entry mode */
        mode_number_entry = false;
        if (flags.f.prgm_mode) {
            arg_struct arg;
            arg.type = ARGTYPE_DOUBLE;
            arg.val_d = entered_number;
            cmdline[cmdline_length] = 0;
            move_prgm_highlight(1);
            if (cmdline_unit == -1) {
                store_command(pc, CMD_NUMBER, &arg, cmdline);
            } else {
                std::string u;
                int ulen = cmdline_length - cmdline_unit - 1;
                if (ulen > 0) {
                    if (!normalize_unit(std::string(cmdline + cmdline_unit + 1, ulen), &u)) {
                        mode_number_entry = true;
                        squeak();
                        return;
                    }
                }
                if (u == "")
                    u = std::string(cmdline, cmdline_unit);
                else
                    u = std::string(cmdline, cmdline_unit + 1) + u;
                store_command(pc, CMD_NUMBER, &arg, u.c_str());
                set_menu(MENULEVEL_COMMAND, MENU_NONE);
                redisplay();
                return;
            }
        } else if ((flags.f.trace_print || flags.f.normal_print)
                && flags.f.printer_exists)
            deferred_print = 1;
        if (!flags.f.prgm_mode && alpha_active()) {
            /* Attach unit to the entered number, which is already in X */
            int ulen = cmdline_length - cmdline_unit - 1;
            if (ulen > 0) {
                std::string u;
                if (!normalize_unit(std::string(cmdline + cmdline_unit + 1, ulen), &u)) {
                    mode_number_entry = true;
                    deferred_print = 0;
                    squeak();
                    return;
                }
                vartype_real *x = (vartype_real *) stack[sp];
                vartype *new_x = new_unit(x->x, u.c_str(), (int) u.length());
                if (new_x == NULL) {
                    squeak();
                } else {
                    free_vartype(stack[sp]);
                    stack[sp] = new_x;
                }
            }
            set_menu(MENULEVEL_COMMAND, MENU_NONE);
            redisplay();
            return;
        }
        if (flags.f.big_stack && !shift && key == KEY_ENTER) {
            redisplay();
            return;
        }
    }

    if (mode_command_entry
            && (shift || get_front_menu() == MENU_NONE)
            && (key == KEY_UP || key == KEY_DOWN)) {
        /* Trying to do SST or BST while in command entry mode */
        squeak();
        return;
    }

    if (key == KEY_UP || (key == KEY_DOWN &&
                (flags.f.prgm_mode || (!shift && get_front_menu() != MENU_NONE)))) {
        /* UP, DOWN, BST, or prgm-mode SST */
        repeating = 1;
        repeating_shift = shift;
        repeating_key = key;
    }

    if (flags.f.prgm_mode && (key == KEY_UP || key == KEY_DOWN)
            && (shift || get_front_menu() == MENU_NONE)) {
        /* Stepping through the program in prgm mode */
        if (flags.f.prgm_mode && mode_alpha_entry)
            finish_alpha_prgm_line();
        clear_all_rtns();
        if (key == KEY_UP)
            bst();
        else
            sst();
        redisplay();
        return;
    }

    if (!shift && (key == KEY_UP || key == KEY_DOWN) && get_front_menu() == MENU_CATALOG) {
        int sect = get_cat_section();
        switch (sect) {
            case CATSECT_TOP:
                sect = key == KEY_UP ? CATSECT_EXT_2 : CATSECT_MORE;
                break;
            case CATSECT_MORE:
                sect = key == KEY_UP ? CATSECT_TOP : CATSECT_EXT_1;
                break;
            case CATSECT_EXT_1:
                sect = key == KEY_UP ? CATSECT_MORE : CATSECT_EXT_2;
                break;
            case CATSECT_EXT_2:
                sect = key == KEY_UP ? CATSECT_EXT_1 : CATSECT_TOP;
                break;
            case CATSECT_UNITS_1:
                sect = key == KEY_UP ? CATSECT_UNITS_3 : CATSECT_UNITS_2;
                break;
            case CATSECT_UNITS_2:
                sect = key == KEY_UP ? CATSECT_UNITS_1 : CATSECT_UNITS_3;
                break;
            case CATSECT_UNITS_3:
                sect = key == KEY_UP ? CATSECT_UNITS_2 : CATSECT_UNITS_1;
                break;
            default:
                sect = -1;
                break;
        }
        if (sect != -1) {
            set_cat_section(sect);
            redisplay();
            return;
        }
    }

    if (!flags.f.prgm_mode && key == KEY_UP
            && (shift || get_front_menu() == MENU_NONE)) {
        /* BST in normal or alpha mode */
        if (mode_alpha_entry
                && (flags.f.trace_print || flags.f.normal_print)
                && flags.f.printer_exists)
            docmd_pra(NULL);
        mode_alpha_entry = false;
        clear_all_rtns();
        bst();
        flags.f.prgm_mode = 1;
        redisplay();
        flags.f.prgm_mode = 0;
        pending_command = CMD_CANCELLED;
        return;
    }

    if (mode_number_entry)
        keydown_number_entry(shift, key);
    else if (mode_command_entry)
        keydown_command_entry(shift, key);
    else if (alpha_active())
        keydown_alpha_mode(shift, key);
    else
        keydown_normal_mode(shift, key);
}

void keydown_number_entry(int shift, int key) {
    phloat x;
    int base = get_base();

    if (key == -1) {
        /* Hack... The user is switching to the A...F menu */
        set_menu(MENULEVEL_APP, MENU_BASE_A_THRU_F);
        redisplay();
        goto draw_number;
    }

    if (base != 10 && (key == KEY_E || key == KEY_DOT))
        return;

    /* NOTE: 'key' can only be KEY_CHS at this point in the code
     * if 'baseapp' is false and get_base() returns 10; in all other
     * cases, the +/- key will end number entry mode and we won't
     * get here, and the CMD_CHS or CMD_BASECHS function will be
     * invoked instead.
     */

    if (key == KEY_BSP && cmdline_length == 1) {
        char pne = mode_number_entry;
        mode_number_entry = false;
        if (flags.f.prgm_mode) {
            pc = line2pc(pc2line(pc) - 1);
            move_prgm_highlight(-1);
            redisplay();
            return;
        } else {
            pending_command = flags.f.big_stack ? pne == 2 ? CMD_DROP_CANCL : CMD_DROP : CMD_CLX;
            return;
        }
    }

    if (key == KEY_BSP) {
        if (shift) {
            squeak();
            return;
        }
        cmdline_length--;
        if (!flags.f.prgm_mode)
            if (base == 10)
                fix_thousands_separators(cmdline, &cmdline_length);
            else
                fix_base_separators(cmdline, &cmdline_length);
        if (core_settings.auto_repeat) {
            repeating = 2;
            repeating_key = key;
            repeating_shift = shift;
        }
        if (cmdline_length <= cmdline_unit) {
            remove_unit:
            cmdline_unit = -1;
            set_menu(MENULEVEL_COMMAND, MENU_NONE);
            vartype *r = new_real(((vartype_unit *) stack[sp])->x);
            if (r != NULL) {
                free_vartype(stack[sp]);
                stack[sp] = r;
            }
            redisplay();
        }
        if (cmdline_unit != -1)
            goto draw_number;
    } else if (alpha_active()) {
        char c;
        int menukey;
        const menu_spec *m = NULL;
        if (key >= 1024 && key < 2048) {
            c = key - 1024;
            goto handle_char;
        } else if ((menukey = find_menu_key(key)) != -1) {
            const menu_item_spec *mi;
            m = menus + mode_commandmenu;
            mi = m->child + menukey;
            if (mi->menuid != MENU_NONE) {
                set_menu(MENULEVEL_COMMAND, mi->menuid);
            } else {
                c = mi->title[0];
                if (shift && c >= 'A' && c <= 'Z')
                    c += 'a' - 'A';
                handle_char:
                if (cmdline_length < 100)
                    cmdline[cmdline_length++] = c;
                if (m != NULL)
                    set_menu(MENULEVEL_COMMAND, m->parent);
                if (core_settings.auto_repeat) {
                    repeating = 2;
                    repeating_key = c + 1024;
                    repeating_shift = 0;
                }
            }
            redisplay();
        } else {
            if (key == KEY_UP || key == KEY_DOWN) {
                if (shift) {
                    squeak();
                    return;
                }
                m = menus + mode_commandmenu;
                int id = key == KEY_UP ? m->prev : m->next;
                if (id != MENU_NONE) {
                    set_menu(MENULEVEL_COMMAND, id);
                    redisplay();
                }
            } else if (key == KEY_EXIT) {
                m = menus + mode_commandmenu;
                int id = m->parent;
                if (id == MENU_NONE) {
                    cmdline_length = cmdline_unit;
                    goto remove_unit;
                } else {
                    set_menu(MENULEVEL_COMMAND, id);
                    redisplay();
                }
            } else if (!shift) {
                switch (key) {
                    case KEY_0:   c = '0'; break;
                    case KEY_1:   c = '1'; break;
                    case KEY_2:   c = '2'; break;
                    case KEY_3:   c = '3'; break;
                    case KEY_4:   c = '4'; break;
                    case KEY_5:   c = '5'; break;
                    case KEY_6:   c = '6'; break;
                    case KEY_7:   c = '7'; break;
                    case KEY_8:   c = '8'; break;
                    case KEY_9:   c = '9'; break;
                    case KEY_DOT: c = '.'; break;
                    case KEY_E:   c = 24;  break;
                    case KEY_DIV: c = 0;   break;
                    case KEY_MUL: c = 1;   break;
                    case KEY_SUB: c = '-'; break;
                    case KEY_ADD: c = '+'; break;
                    default: squeak(); return;
                }
                goto handle_char;
            } else {
                switch (key) {
                    case KEY_RCL: c = '%'; break;
                    case KEY_RDN: c = 7;   break;
                    default: squeak(); return;
                }
                goto handle_char;
            }
        }
        goto draw_number;
    } else if (key == KEY_CHS) {
        /* Check if mantissa or exponent gets the sign change */
        int i;
        int exp_pos = -1;
        for (i = 0; i < cmdline_length; i++)
            if (cmdline[i] == 24) {
                exp_pos = i;
                break;
            }
        if (exp_pos != -1) {
            /* Change exponent sign */
            int failed = 0;
            phloat d;
            undo_chs_exp:
            if (cmdline_length > exp_pos + 1
                    && cmdline[exp_pos + 1] == '-') {
                for (i = exp_pos + 1; i < cmdline_length - 1; i++)
                    cmdline[i] = cmdline[i + 1];
                cmdline_length--;
            } else {
                for (i = cmdline_length; i > exp_pos + 1; i--)
                    cmdline[i] = cmdline[i - 1];
                cmdline[exp_pos + 1] = '-';
                cmdline_length++;
            }
            if (!failed) {
                if (string2phloat(cmdline, cmdline_length, &d) != 0) {
                    failed = 1;
                    goto undo_chs_exp;
                }
            } else
                return;
        } else {
            /* Change mantissa sign */
            if (cmdline[0] == '-') {
                if (cmdline_length == 1) {
                    if (flags.f.prgm_mode) {
                        mode_number_entry = false;
                        pc = line2pc(pc2line(pc) - 1);
                            move_prgm_highlight(-1);
                        redisplay();
                        return;
                    } else {
                        /* This is a bit odd, but it's how the HP-42S
                         * does it, so there.
                         */
                        free_vartype(stack[sp]);
                        stack[sp] = new_real(0);
                        pending_command = flags.f.big_stack ? CMD_DROP : CMD_CLX;
                        pending_command = flags.f.big_stack ? mode_number_entry == 2 ? CMD_DROP_CANCL : CMD_DROP : CMD_CLX;
                        mode_number_entry = false;
                        return;
                    }
                }
                for (i = 0; i < cmdline_length - 1; i++)
                    cmdline[i] = cmdline[i + 1];
                cmdline_length--;
            } else {
                for (i = cmdline_length; i > 0; i--)
                    cmdline[i] = cmdline[i - 1];
                cmdline[0] = '-';
                cmdline_length++;
            }
        }
    } else if (key == KEY_E) {
        int exp_pos = -1;
        int only_zeroes = 1;
        int seen_dot = 0;
        char dot = flags.f.decimal_point ? '.' : ',';
        int i;
        for (i = 0; i < cmdline_length; i++) {
            char c = cmdline[i];
            if (c >= '1' && c <= '9')
                only_zeroes = 0;
            else if (c == dot)
                seen_dot = 1;
            else if (c == 24) {
                exp_pos = i;
                break;
            }
        }
        if (exp_pos == -1) {
            if (only_zeroes) {
                if (cmdline_length > 0 && cmdline[0] == '-')
                    cmdline_length = 1;
                else
                    cmdline_length = 0;
                cmdline[cmdline_length++] = '1';
                if (seen_dot)
                    cmdline[cmdline_length++] = dot;
            }
            cmdline[cmdline_length++] = 24;
        } else
            return;
    } else if (key == KEY_DOT && shift && get_base() == 10) {
        /* Only allow _ if there isn't one already.
         * Also, require at least one digit.
         */
        bool digit = false;
        for (int i = 0; i < cmdline_length; i++) {
            char c = cmdline[i];
            if (c == '_')
                return;
            if (c >= '0' && c <= '9')
                digit = true;
        }
        if (!digit)
            return;
        cmdline_unit = cmdline_length;
        cmdline[cmdline_length++] = '_';
        set_menu(MENULEVEL_COMMAND, MENU_ALPHA1);
        redisplay();
        goto draw_number;
    } else if (key == KEY_DOT) {
        if (cmdline_length == 0 ||
                (cmdline_length == 1 && cmdline[0] == '-')) {
            cmdline[cmdline_length++] = '0';
            cmdline[cmdline_length++] = flags.f.decimal_point ? '.' : ',';
        } else {
            /* Only allow dot if there isn't one already, and
             * there is no exponent either
             */
            int dot_or_exp_pos = -1;
            int i;
            char dot = flags.f.decimal_point ? '.' : ',';
            for (i = 0; i < cmdline_length; i++)
                if (cmdline[i] == dot || cmdline[i] == 24) {
                    dot_or_exp_pos = i;
                    break;
                }
            if (dot_or_exp_pos == -1)
                cmdline[cmdline_length++] = dot;
            else
                return;
        }
    } else /* KEY_0 .. KEY_9 or hex A-F */ {
        int digit;
        char c;
        switch (key) {
            case KEY_0: digit = 0; break;
            case KEY_1: digit = 1; break;
            case KEY_2: digit = 2; break;
            case KEY_3: digit = 3; break;
            case KEY_4: digit = 4; break;
            case KEY_5: digit = 5; break;
            case KEY_6: digit = 6; break;
            case KEY_7: digit = 7; break;
            case KEY_8: digit = 8; break;
            case KEY_9: digit = 9; break;
            case KEY_SIGMA: digit = 10; break;
            case KEY_INV:   digit = 11; break;
            case KEY_SQRT:  digit = 12; break;
            case KEY_LOG:   digit = 13; break;
            case KEY_LN:    digit = 14; break;
            case KEY_XEQ:   digit = 15; break;
        }
        if (digit >= base)
            return;
        if (core_settings.auto_repeat) {
            repeating = 2;
            repeating_key = key;
            repeating_shift = shift;
        }
        c = digit < 10 ? '0' + digit : 'A' + digit - 10;
        cmdline[cmdline_length++] = c;
        if (base == 10) {
            if (string2phloat(cmdline, cmdline_length, &x) == 0) {
                if (!flags.f.prgm_mode)
                    fix_thousands_separators(cmdline, &cmdline_length);
            } else {
                cmdline_length--;
                return;
            }
        } else {
            bool zero = true;
            int bits = 0;
            int bits_per_digit = base == 2 ? 1 : base == 8 ? 3 : 4;
            for (int i = 0; i < cmdline_length; i++) {
                char c = cmdline[i];
                if (c == ' ')
                    continue;
                if (!zero) {
                    bits += bits_per_digit;
                    continue;
                }
                int d = c < 'A' ? c - '0' : c - 'A' + 10;
                if (d >= 8)
                    bits = 4;
                else if (d >= 4)
                    bits = 3;
                else if (d >= 2)
                    bits = 2;
                else
                    bits = d;
                zero = false;
            }
            if (bits > effective_wsize()) {
                cmdline_length--;
                return;
            }
            fix_base_separators(cmdline, &cmdline_length);
        }
    }

    if (base == 10) {
        if (string2phloat(cmdline, cmdline_length, &x) != 0)
            /* Should never happen */
            x = 0;
    } else {
        uint8 n = 0;
        int i;
        for (i = 0; i < cmdline_length; i++) {
            char c = cmdline[i];
            if (c == ' ')
                continue;
            int digit = c <= '9' ? c - '0' : c - 'A' + 10;
            n = n * base + digit;
        }
        int wsize = effective_wsize();
        if (!flags.f.base_signed)
            x = (phloat) n;
        else if ((n & (1ULL << (wsize - 1))) == 0)
            x = (phloat) n;
        else
            x = (phloat) (int8) (n | (-1LL << (wsize - 1)));
    }

    if (flags.f.prgm_mode)
        entered_number = x;
    else {
        free_vartype(stack[sp]);
        stack[sp] = new_real(x);
    }

    draw_number:
    redisplay();
    return;
}

void keydown_command_entry(int shift, int key) {
    if (mode_commandmenu == MENU_ST || mode_commandmenu == MENU_IND_ST) {
        int menukey;
        if (!shift && key == KEY_BSP) {
            pending_command = CMD_NULL;
            finish_command_entry(false);
            return;
        }
        if (key == KEY_EXIT) {
            pending_command = CMD_CANCELLED;
            finish_command_entry(false);
            return;
        }
        menukey = find_menu_key(key);
        if (!shift && ((menukey >= 0 && menukey <= 4)
                || (menukey == 5 && mode_commandmenu == MENU_IND_ST))) {
            if (mode_commandmenu == MENU_IND_ST && menukey == 0) {
                incomplete_ind = true;
                incomplete_alpha = false;
                incomplete_maxdigits = 2;
                set_catalog_menu(CATSECT_REAL_ONLY);
                redisplay();
                return;
            }
            if (mode_commandmenu == MENU_IND_ST)
                menukey--;
            pending_command = incomplete_command;
            pending_command_arg.type =
                        incomplete_ind ? ARGTYPE_IND_STK : ARGTYPE_STK;
            pending_command_arg.val.stk = "LXYZT"[menukey];
            finish_command_entry(true);
            return;
        }
        squeak();
        return;
    }

    if (incomplete_command == CMD_LBL && incomplete_length == 0
            && mode_commandmenu != MENU_CATALOG) {
        /* LBL is weird. It's sort of like you have alpha and numeric
         * at the same time. When we're at length 0, we have to handle
         * both possibilities and pick the right one.
         */
        if ((mode_commandmenu == MENU_ALPHA1 || mode_commandmenu == MENU_ALPHA2)
                && key >= 1024 + '0' && key <= 1024 + '9')
            switch (key - 1024) {
                case '0': key = KEY_0; break;
                case '1': key = KEY_1; break;
                case '2': key = KEY_2; break;
                case '3': key = KEY_3; break;
                case '4': key = KEY_4; break;
                case '5': key = KEY_5; break;
                case '6': key = KEY_6; break;
                case '7': key = KEY_7; break;
                case '8': key = KEY_8; break;
                case '9': key = KEY_9; break;
            }

        if (key >= 1024 && key < 2048
            || (key == KEY_SIGMA || key == KEY_INV || key == KEY_SQRT
                    || key == KEY_LOG || key == KEY_LN || key == KEY_XEQ)
            || (!shift &&
                (key == KEY_E || key == KEY_UP || key == KEY_DOWN
                    || key == KEY_DIV || key == KEY_MUL || key == KEY_SUB
                    || key == KEY_ADD || key == KEY_DOT))
            || (shift &&
                (key == KEY_RCL || key == KEY_RDN))
            || (mode_commandmenu >= MENU_ALPHA_ABCDE1 &&
                mode_commandmenu <= MENU_ALPHA_MISC2 && (
                    key == KEY_0 || key == KEY_1 || key == KEY_2
                    || key == KEY_3 || key == KEY_4 || key == KEY_5
                    || key == KEY_6 || key == KEY_7 || key == KEY_8
                    || key == KEY_9)))
            goto do_incomplete_alpha;
        if (shift && key == KEY_ADD) {
            if (mode_commandmenu == MENU_CATALOG)
                squeak();
            else {
                incomplete_alpha = true;
                set_catalog_menu(CATSECT_TOP);
                redisplay();
            }
            return;
        }
        if (key == KEY_EXIT && mode_commandmenu >= MENU_ALPHA_ABCDE1
                            && mode_commandmenu <= MENU_ALPHA_MISC2) {
            if (mode_commandmenu <= MENU_ALPHA_WXYZ)
                mode_commandmenu = MENU_ALPHA1;
            else
                mode_commandmenu = MENU_ALPHA2;
            redisplay();
            return;
        }
    }

    if (incomplete_command == CMD_LBL && !incomplete_alpha && incomplete_length == 1
            && shift && key == KEY_ENTER) {
        /* More LBL weirdness: you can switch to ALPHA mode while entering
         * a numeric LBL
         */
        incomplete_alpha = true;
        incomplete_str[0] = '0' + incomplete_num;
        incomplete_num = 0;
        mode_commandmenu = MENU_ALPHA1;
        redisplay();
        return;
    }

    if ((incomplete_command == CMD_ASTO || incomplete_command == CMD_ARCL)
            && mode_commandmenu == MENU_NONE
            && mode_alphamenu >= MENU_ALPHA1 && mode_alphamenu <= MENU_ALPHA_MISC2) {
        /* ASTO and ARCL in ALPHA mode: When no variables menu is shown, either
         * because one digit has already been typed, or because no variables
         * exist, you can type digits for a numeric argument, even though the
         * ALPHA menu is active. Note that this behaves similarly to LBL, but
         * different.
         */
        switch (key - 1024) {
            case '0': key = KEY_0; break;
            case '1': key = KEY_1; break;
            case '2': key = KEY_2; break;
            case '3': key = KEY_3; break;
            case '4': key = KEY_4; break;
            case '5': key = KEY_5; break;
            case '6': key = KEY_6; break;
            case '7': key = KEY_7; break;
            case '8': key = KEY_8; break;
            case '9': key = KEY_9; break;
        }
    }


    /* Another oddity: ASSIGN... */
    if (incomplete_argtype == ARG_CKEY) {
        int menukey = find_menu_key(key);
        if (menukey != -1) {
            pending_command = CMD_ASGN01 + menukey
                            + 6 * (mode_commandmenu - MENU_CUSTOM1);
            finish_command_entry(true);
        } else if (!shift && key == KEY_BSP) {
            pending_command = CMD_NULL;
            finish_command_entry(false);
        } else if (key == KEY_EXIT) {
            pending_command = CMD_CANCELLED;
            finish_command_entry(false);
        } else if (!shift && (key == KEY_UP || key == KEY_DOWN)) {
            mode_commandmenu += key == KEY_UP ? -1 : 1;
            if (mode_commandmenu < MENU_CUSTOM1)
                set_menu(MENULEVEL_COMMAND, MENU_CUSTOM3);
            else if (mode_commandmenu > MENU_CUSTOM3)
                set_menu(MENULEVEL_COMMAND, MENU_CUSTOM1);
            redisplay();
        } else
            squeak();
        return;
    }

    /* And yet another oddity: KEYG and KEYX */
    if (incomplete_argtype == ARG_MKEY) {
        int cmd = incomplete_command == CMD_KEYG ? CMD_KEY1G : CMD_KEY1X;
        if (shift) {
            squeak();
            return;
        }
        switch (key) {
            case KEY_SIGMA: case KEY_1: break;
            case KEY_INV: case KEY_2: cmd++; break;
            case KEY_SQRT: case KEY_3: cmd += 2; break;
            case KEY_LOG: case KEY_4: cmd += 3; break;
            case KEY_LN: case KEY_5: cmd += 4; break;
            case KEY_XEQ: case KEY_6: cmd += 5; break;
            case KEY_UP: case KEY_7: cmd += 6; break;
            case KEY_DOWN: case KEY_8: cmd += 7; break;
            case KEY_EXIT: case KEY_9: cmd += 8; break;
            case KEY_BSP:
                pending_command = CMD_NULL;
                finish_command_entry(false);
                return;
            default:
                squeak();
                return;
        }
        start_incomplete_command(cmd);
        return;
    }

    if (mode_commandmenu == MENU_CATALOG) {
        int menukey = find_menu_key(key);
        int catsect = get_cat_section();
        if (menukey != -1) {
            if (catsect == CATSECT_TOP) {
                switch (menukey) {
                    case 0:
                        if ((skin_flags & 1) != 0) {
                            set_cat_section(CATSECT_FCN);
                            break;
                        } else {
                            if (incomplete_command == CMD_ASSIGNa || cwd->children_count == 0) {
                                squeak();
                                return;
                            } else {
                                set_cat_section(CATSECT_DIRS_ONLY);
                                move_cat_row(0);
                                break;
                            }
                        }
                    case 1:
                        set_cat_section(CATSECT_PGM);
                        move_cat_row(0);
                        break;
                    case 2:
                        if (!vars_exist(CATSECT_REAL)) {
                            squeak();
                            return;
                        } else {
                            set_cat_section(CATSECT_REAL);
                            move_cat_row(0);
                            break;
                        }
                    case 3:
                        if (!vars_exist(CATSECT_CPX)) {
                            squeak();
                            return;
                        } else {
                            set_cat_section(CATSECT_CPX);
                            move_cat_row(0);
                            break;
                        }
                    case 4:
                        if (!vars_exist(CATSECT_MAT)) {
                            squeak();
                            return;
                        } else {
                            set_cat_section(CATSECT_MAT);
                            move_cat_row(0);
                            break;
                        }
                    case 5:
                        if ((skin_flags & 2) != 0) {
                            display_mem();
                            pending_command = CMD_LINGER1;
                            shell_request_timeout3(2000);
                            return;
                        } else {
                            if (incomplete_command == CMD_ASSIGNa) {
                                set_cat_section(CATSECT_UNITS_1);
                                break;
                            } else {
                                squeak();
                                return;
                            }
                        }
                }
                redisplay();
                return;
            } else if (catsect == CATSECT_MORE) {
                switch (menukey) {
                    case 0:
                        if (!vars_exist(CATSECT_LIST)) {
                            squeak();
                            return;
                        } else {
                            set_cat_section(CATSECT_LIST);
                            break;
                        }
                    case 1:
                        if (!vars_exist(CATSECT_EQN)) {
                            squeak();
                            return;
                        } else {
                            set_cat_section(CATSECT_EQN);
                            break;
                        }
                    case 2:
                        // There are no commands that take equation names,
                        // so there's not much point entering this section
                        squeak();
                        return;
                    case 3:
                        if (!vars_exist(CATSECT_OTHER)) {
                            squeak();
                            return;
                        } else {
                            set_cat_section(CATSECT_OTHER);
                            break;
                        }
                    case 4:
                        if ((skin_flags & 1) == 0) {
                            set_cat_section(CATSECT_FCN);
                            break;
                        } else {
                            if (incomplete_command == CMD_ASSIGNa || cwd->children_count == 0) {
                                squeak();
                                return;
                            } else {
                                set_cat_section(CATSECT_DIRS_ONLY);
                                move_cat_row(0);
                                break;
                            }
                        }
                    case 5:
                        if ((skin_flags & 2) == 0) {
                            display_mem();
                            pending_command = CMD_LINGER1;
                            shell_request_timeout3(2000);
                            return;
                        } else {
                            if (incomplete_command == CMD_ASSIGNa) {
                                set_cat_section(CATSECT_UNITS_1);
                                break;
                            } else {
                                squeak();
                                return;
                            }
                        }
                }
                move_cat_row(0);
                redisplay();
                return;
            } else if (catsect == CATSECT_EXT_1) {
                switch (menukey) {
                    case 0: set_cat_section(CATSECT_EXT_TIME); break;
                    case 1: set_cat_section(CATSECT_EXT_XFCN); break;
                    case 2: set_cat_section(CATSECT_EXT_BASE); break;
                    case 3: set_cat_section(CATSECT_EXT_PRGM); break;
                    case 4: set_cat_section(CATSECT_EXT_STR); break;
                    case 5: set_cat_section(CATSECT_EXT_STK); break;
                }
                move_cat_row(0);
                redisplay();
                return;
            } else if (catsect == CATSECT_EXT_2) {
                switch (menukey) {
                    case 0:
                        set_cat_section(CATSECT_EXT_EQN);
                        move_cat_row(0);
                        break;
                    case 1:
                        set_cat_section(CATSECT_EXT_UNIT);
                        move_cat_row(0);
                        break;
                    case 2:
                        set_cat_section(CATSECT_EXT_STAT);
                        move_cat_row(0);
                        break;
                    case 3:
                        set_cat_section(CATSECT_EXT_DIR);
                        move_cat_row(0);
                        break;
                    case 4:
                        set_cat_section(CATSECT_EXT_DISP);
                        move_cat_row(0);
                        break;
                    case 5:
                        set_cat_section(CATSECT_EXT_MISC);
                        move_cat_row(0);
                        break;
                    default:
                        squeak();
                        return;
                }
                redisplay();
                return;
            } else if (catsect == CATSECT_DIRS_ONLY) {
                int p = get_cat_row() * 6 + menukey;
                if (p < cwd->children_count) {
                    pending_command = incomplete_command;
                    pending_command_arg.type =
                        incomplete_ind ? ARGTYPE_IND_STR : ARGTYPE_STR;
                    pending_command_arg.length = cwd->children[p].length;
                    for (int i = 0; i < pending_command_arg.length; i++)
                        pending_command_arg.val.text[i] = cwd->children[p].name[i];
                    finish_command_entry(true);
                } else {
                    squeak();
                }
                return;
            } else if (catsect == CATSECT_UNITS_1) {
                switch (menukey) {
                    case 0: set_cat_section(CATSECT_UNITS_LENG); break;
                    case 1: set_cat_section(CATSECT_UNITS_AREA); break;
                    case 2: set_cat_section(CATSECT_UNITS_VOL); break;
                    case 3: set_cat_section(CATSECT_UNITS_TIME); break;
                    case 4: set_cat_section(CATSECT_UNITS_SPEED); break;
                    case 5: set_cat_section(CATSECT_UNITS_MASS); break;
                }
                move_cat_row(0);
                redisplay();
                return;
            } else if (catsect == CATSECT_UNITS_2) {
                switch (menukey) {
                    case 0: set_cat_section(CATSECT_UNITS_FORCE); break;
                    case 1: set_cat_section(CATSECT_UNITS_ENRG); break;
                    case 2: set_cat_section(CATSECT_UNITS_POWR); break;
                    case 3: set_cat_section(CATSECT_UNITS_PRESS); break;
                    case 4: set_cat_section(CATSECT_UNITS_TEMP); break;
                    case 5: set_cat_section(CATSECT_UNITS_ELEC); break;
                }
                move_cat_row(0);
                redisplay();
                return;
            } else if (catsect == CATSECT_UNITS_3) {
                switch (menukey) {
                    case 0: set_cat_section(CATSECT_UNITS_ANGL); break;
                    case 1: set_cat_section(CATSECT_UNITS_LIGHT); break;
                    case 2: set_cat_section(CATSECT_UNITS_RAD); break;
                    case 3: set_cat_section(CATSECT_UNITS_VISC); break;
                    case 4: squeak(); return;
                    case 5: squeak(); return;
                }
                move_cat_row(0);
                redisplay();
                return;
            } else if (catsect >= CATSECT_UNITS_LENG && catsect <= CATSECT_UNITS_VISC) {
                const char *text[6];
                int length[6];
                int row;
                row = get_cat_row();
                int rows;
                get_units_cat_row(catsect, text, length, &row, &rows);
                if (length[menukey] == 0 || length[menukey] > 7) {
                    squeak();
                    return;
                } else {
                    pending_command = incomplete_command;
                    pending_command_arg.type = ARGTYPE_STR;
                    string_copy(pending_command_arg.val.text, &pending_command_arg.length, text[menukey], length[menukey]);
                    finish_command_entry(true);
                    return;
                }
            } else {
                int4 dir_id;
                int itemindex;
                if (!get_cat_item(menukey, &dir_id, &itemindex)) {
                    squeak();
                    return;
                } else if (itemindex < 0) {
                    set_cat_section(itemindex == -2 ? CATSECT_EXT_0_CMP : CATSECT_EXT_X_CMP);
                    move_cat_row(0);
                    redisplay();
                    return;
                }
                directory *dir = get_dir(dir_id);
                if (catsect == CATSECT_PGM || catsect == CATSECT_PGM_ONLY) {
                    if (dir->labels[itemindex].length == 0) {
                        /* END or .END. */
                        if (incomplete_command != CMD_GTODOT
                                && incomplete_command != CMD_PRP
                                && (flags.f.prgm_mode
                                    || (incomplete_command != CMD_GTO
                                        && incomplete_command != CMD_XEQ
                                        && incomplete_command != CMD_CLP))) {
                            squeak();
                            return;
                        }
                    }
                    pending_command = incomplete_command;
                    if (incomplete_command == CMD_GTO
                            || incomplete_command == CMD_GTODOT
                            || incomplete_command == CMD_XEQ
                            || incomplete_command == CMD_CLP
                            || incomplete_command == CMD_PRP) {
                        pending_command_arg.type = ARGTYPE_LBLINDEX;
                        pending_command_arg.val.num = itemindex;
                        pending_command_arg.target = dir_id;
                        xeq_invisible = 0;
                    } else {
                        pending_command_arg.type =
                            incomplete_ind ? ARGTYPE_IND_STR : ARGTYPE_STR;
                        string_copy(pending_command_arg.val.text, &pending_command_arg.length, dir->labels[itemindex].name, dir->labels[itemindex].length);
                    }
                    finish_command_entry(true);
                    return;
                }
                pending_command = incomplete_command;
                pending_command_arg.type =
                            incomplete_ind ? ARGTYPE_IND_STR : ARGTYPE_STR;
                if (catsect == CATSECT_FCN
                        || catsect >= CATSECT_EXT_TIME && catsect <= CATSECT_EXT_MISC) {
                    const command_spec *cs = &cmd_array[itemindex];
                    string_copy(pending_command_arg.val.text, &pending_command_arg.length, cs->name, cs->name_length);
                } else {
                    var_struct *vs;
                    if (dir_id == 0)
                        vs = local_vars + itemindex;
                    else
                        vs = get_dir(dir_id)->vars + itemindex;
                    string_copy(pending_command_arg.val.text, &pending_command_arg.length, vs->name, vs->length);
                }

                if (!incomplete_ind
                        && (pending_command == CMD_GTO
                            || pending_command == CMD_XEQ
                            || pending_command == CMD_LBL
                            || (pending_command >= CMD_KEY1G
                                && pending_command <= CMD_KEY9X))
                        && pending_command_arg.length == 1
                        && ((pending_command_arg.val.text[0] >= 'A'
                                && pending_command_arg.val.text[0] <= 'J')
                            || (pending_command_arg.val.text[0] >= 'a'
                                && pending_command_arg.val.text[0] <= 'e'))) {
                    /* Display XEQ "A" briefly before changing to XEQ A */
                    mode_command_entry = false;
                    if (flags.f.prgm_mode) {
                        flags.f.prgm_mode = 0;
                        redisplay();
                        flags.f.prgm_mode = 1;
                        shell_delay(125);
                    } else
                        redisplay();
                    pending_command_arg.type = ARGTYPE_LCLBL;
                    pending_command_arg.val.lclbl = pending_command_arg.val.text[0];
                    finish_command_entry(false);
                    return;
                }

                if (!incomplete_ind && incomplete_command == CMD_XEQ)
                    finish_xeq();
                else
                    finish_command_entry(true);
                return;
            }
        }
        if (!shift && (key == KEY_UP || key == KEY_DOWN)) {
            move_cat_row(key == KEY_UP ? -1 : 1);
            redisplay();
            return;
        }
        if (incomplete_command == CMD_ASSIGNa && key == 2048 + CMD_UNITS) {
            set_cat_section_using_units_key();
            redisplay();
            return;
        }
        if (key == KEY_EXIT) {
            if (catsect == CATSECT_PGM
                    || catsect == CATSECT_REAL
                    || catsect == CATSECT_CPX
                    || catsect == CATSECT_MAT) {
                set_cat_section(CATSECT_TOP);
                redisplay();
            } else if (catsect == CATSECT_DIRS) {
                set_cat_section((skin_flags & 1) == 0 ? CATSECT_TOP : CATSECT_MORE);
                redisplay();
            } else if (catsect >= CATSECT_UNITS_1
                        && catsect <= CATSECT_UNITS_3) {
                set_cat_section((skin_flags & 2) == 0 ? CATSECT_TOP : CATSECT_MORE);
                redisplay();
            } else if (catsect == CATSECT_LIST
                    || catsect == CATSECT_EQN
                    || catsect == CATSECT_EQN_NAMED
                    || catsect == CATSECT_OTHER) {
                set_cat_section(CATSECT_MORE);
                redisplay();
            } else if (catsect == CATSECT_FCN) {
                set_cat_section((skin_flags & 1) == 0 ? CATSECT_MORE : CATSECT_TOP);
                redisplay();
            } else if (catsect >= CATSECT_UNITS_LENG
                    && catsect <= CATSECT_UNITS_MASS) {
                set_cat_section(CATSECT_UNITS_1);
                redisplay();
            } else if (catsect >= CATSECT_UNITS_FORCE
                    && catsect <= CATSECT_UNITS_ELEC) {
                set_cat_section(CATSECT_UNITS_2);
                redisplay();
            } else if (catsect >= CATSECT_UNITS_ANGL
                    && catsect <= CATSECT_UNITS_VISC) {
                set_cat_section(CATSECT_UNITS_3);
                redisplay();
            } else if (catsect == CATSECT_EXT_TIME
                    || catsect == CATSECT_EXT_XFCN
                    || catsect == CATSECT_EXT_BASE
                    || catsect == CATSECT_EXT_PRGM
                    || catsect == CATSECT_EXT_STR
                    || catsect == CATSECT_EXT_STK) {
                set_cat_section(CATSECT_EXT_1);
                redisplay();
            } else if (catsect == CATSECT_EXT_EQN
                    || catsect == CATSECT_EXT_UNIT
                    || catsect == CATSECT_EXT_STAT
                    || catsect == CATSECT_EXT_DIR
                    || catsect == CATSECT_EXT_DISP
                    || catsect == CATSECT_EXT_MISC) {
                set_cat_section(CATSECT_EXT_2);
                redisplay();
            } else if (catsect == CATSECT_EXT_0_CMP
                    || catsect == CATSECT_EXT_X_CMP) {
                set_cat_section(CATSECT_EXT_PRGM);
                set_cat_row(3);
                redisplay();
            } else {
                pending_command = CMD_CANCELLED;
                finish_command_entry(false);
            }
            return;
        }
    }

    if (mode_commandmenu == MENU_VARMENU) {
        int menukey = find_menu_key(key);
        if (menukey != -1) {
            int i;
            if (varmenu_labellength[menukey] == 0) {
                squeak();
                return;
            }
            pending_command = incomplete_command;
            pending_command_arg.type = ARGTYPE_STR;
            pending_command_arg.length = varmenu_labellength[menukey];
            for (i = 0; i < pending_command_arg.length; i++)
                pending_command_arg.val.text[i] =
                                        varmenu_labeltext[menukey][i];
            finish_command_entry(false);
            return;
        }
        if (!shift && (key == KEY_UP || key == KEY_DOWN)) {
            if (varmenu_rows > 1) {
                if (key == KEY_UP) {
                    varmenu_row--;
                    if (varmenu_row < 0)
                        varmenu_row = varmenu_rows - 1;
                } else {
                    varmenu_row++;
                    if (varmenu_row >= varmenu_rows)
                        varmenu_row = 0;
                }
                redisplay();
            }
            return;
        }
        if (key == KEY_EXIT) {
            pending_command = CMD_CANCELLED;
            finish_command_entry(false);
            return;
        }
    } else if (mode_commandmenu == MENU_INTEG_PARAMS || mode_commandmenu == MENU_TVM_PARAMS) {
        int menukey = find_menu_key(key);
        if (menukey != -1) {
            const char *name;
            int length;
            if (mode_commandmenu == MENU_INTEG_PARAMS) {
                switch (menukey) {
                    case 0: name = "LLIM"; length = 4; break;
                    case 1: name = "ULIM"; length = 4; break;
                    case 2: name = "ACC";  length = 3; break;
                    default: squeak(); return;
                }
            } else {
                switch (menukey) {
                    case 0: name = "N";    length = 1; break;
                    case 1: name = "I%YR"; length = 4; break;
                    case 2: name = "PV";   length = 2; break;
                    case 3: name = "PMT";  length = 3; break;
                    case 4: name = "FV";   length = 2; break;
                    case 5: name = "P/YR"; length = 4; break;
                }
            }
            pending_command = incomplete_command;
            pending_command_arg.type = ARGTYPE_STR;
            string_copy(pending_command_arg.val.text, &pending_command_arg.length, name, length);
            finish_command_entry(false);
            return;
        }
        if (key == KEY_EXIT) {
            pending_command = CMD_CANCELLED;
            finish_command_entry(false);
            return;
        }
    }

    if (!incomplete_alpha) {
        if (key == KEY_EXIT) {
            pending_command = CMD_CANCELLED;
            finish_command_entry(false);
            return;
        }

        if (mode_commandmenu == MENU_IND) {
            if (!shift && key == KEY_SIGMA) {
                incomplete_command = CMD_GTO;
                incomplete_argtype = ARG_LBL;
                incomplete_ind = true;
                incomplete_maxdigits = 2;
                set_catalog_menu(CATSECT_REAL_ONLY);
                redisplay();
                return;
            } else if (key == KEY_ENTER) {
                incomplete_argtype = ARG_LBL;
                incomplete_alpha = true;
                set_menu(MENULEVEL_COMMAND, MENU_ALPHA1);
                redisplay();
                return;
            }
        }

        if (incomplete_command == CMD_STO
                && !shift && incomplete_length == 0
                && (key == KEY_DIV || key == KEY_MUL
                    || key == KEY_SUB || key == KEY_ADD)) {
            switch (key) {
                case KEY_DIV: incomplete_command = CMD_STO_DIV; break;
                case KEY_MUL: incomplete_command = CMD_STO_MUL; break;
                case KEY_SUB: incomplete_command = CMD_STO_SUB; break;
                case KEY_ADD: incomplete_command = CMD_STO_ADD; break;
            }
            redisplay();
            return;
        }
        if (incomplete_command == CMD_RCL
                && !shift && incomplete_length == 0
                && (key == KEY_DIV || key == KEY_MUL
                    || key == KEY_SUB || key == KEY_ADD)) {
            switch (key) {
                case KEY_DIV: incomplete_command = CMD_RCL_DIV; break;
                case KEY_MUL: incomplete_command = CMD_RCL_MUL; break;
                case KEY_SUB: incomplete_command = CMD_RCL_SUB; break;
                case KEY_ADD: incomplete_command = CMD_RCL_ADD; break;
            }
            redisplay();
            return;
        }
        if (incomplete_command == CMD_GTO
                && !incomplete_ind
                && !shift && incomplete_length == 0
                && key == KEY_DOT) {
            incomplete_command = CMD_GTODOT;
            incomplete_argtype = ARG_OTHER;
            incomplete_maxdigits = 4;
            set_menu(MENULEVEL_COMMAND, MENU_IND);
            redisplay();
            return;
        }
        if (incomplete_command == CMD_GTODOT
                && !shift && incomplete_length == 0
                && key == KEY_DOT) {
            pending_command = CMD_GTODOTDOT;
            pending_command_arg.type = ARGTYPE_NONE;
            finish_command_entry(false);
            return;
        }


        if (key == KEY_ENTER) {
            if (incomplete_length == 0) {
                if (incomplete_ind
                        && !flags.f.prgm_mode
                        && !vars_exist(CATSECT_REAL_ONLY))
                    squeak();
                else if (incomplete_ind
                        || incomplete_argtype == ARG_VAR
                        || incomplete_argtype == ARG_REAL
                        || incomplete_argtype == ARG_NAMED
                        || incomplete_argtype == ARG_LBL
                        || incomplete_argtype == ARG_PRGM) {
                    incomplete_alpha = true;
                    set_menu(MENULEVEL_COMMAND, MENU_ALPHA1);
                    redisplay();
                } else
                    squeak();
                return;
            } else if (!shift) {
                if (incomplete_command == CMD_GOTOROW) {
                    pending_command_arg.val.num = incomplete_num;
                    vartype *m;
                    int err = matedit_get(&m);
                    if (err == ERR_NONE && m->type == TYPE_LIST) {
                        incomplete_num = 1;
                        goto do_goto1;
                    }
                    if ((flags.f.trace_print || flags.f.normal_print) && flags.f.printer_exists) {
                        arg_struct arg;
                        arg.type = ARGTYPE_NUM;
                        arg.val.num = incomplete_num;
                        print_command(CMD_GOTOROW, &arg);
                    }
                    start_incomplete_command(CMD_GOTOCOLUMN);
                    return;
                } else if (incomplete_command == CMD_GOTOCOLUMN) {
                    do_goto1:
                    if ((flags.f.trace_print || flags.f.normal_print) && flags.f.printer_exists) {
                        arg_struct arg;
                        arg.type = ARGTYPE_NUM;
                        arg.val.num = incomplete_num;
                        print_command(CMD_GOTOCOLUMN, &arg);
                    }
                    matedit_goto(pending_command_arg.val.num, incomplete_num);
                    pending_command = CMD_NONE;
                    finish_command_entry(true);
                    return;
                }
                pending_command = incomplete_command;
                pending_command_arg.type =
                            incomplete_ind ? ARGTYPE_IND_NUM : ARGTYPE_NUM;
                pending_command_arg.length = incomplete_maxdigits;
                pending_command_arg.val.num = incomplete_num;
                finish_command_entry(false);
                return;
            }
        }

        if (incomplete_length == 0 && !shift && key == KEY_DOT) {
            if (incomplete_ind) {
                if (incomplete_argtype == ARG_VAR
                        || incomplete_argtype == ARG_REAL
                        || incomplete_argtype == ARG_MAT
                        || incomplete_argtype == ARG_M_STK
                        || incomplete_argtype == ARG_L_STK
                        || incomplete_argtype == ARG_RVAR
                        || incomplete_argtype == ARG_NAMED
                        || incomplete_argtype == ARG_LBL
                        || incomplete_argtype == ARG_PRGM
                        || incomplete_argtype == ARG_NUM9
                        || incomplete_argtype == ARG_NUM11
                        || incomplete_argtype == ARG_NUM99
                        || incomplete_argtype == ARG_EQN
                        || incomplete_argtype == ARG_DIR) {
                    set_menu(MENULEVEL_COMMAND, MENU_ST);
                    redisplay();
                }
            } else {
                if (incomplete_argtype == ARG_VAR
                        || incomplete_argtype == ARG_REAL) {
                    set_menu(MENULEVEL_COMMAND, MENU_IND_ST);
                    redisplay();
                } else if (incomplete_argtype == ARG_NUM9
                        || incomplete_argtype == ARG_NUM11
                        || incomplete_argtype == ARG_NUM99
                        || incomplete_argtype == ARG_LBL) {
                    incomplete_ind = true;
                    incomplete_maxdigits = 2;
                    set_catalog_menu(CATSECT_REAL_ONLY);
                    redisplay();
                } else {
                    squeak();
                }
            }
            return;
        }

        if (incomplete_length < incomplete_maxdigits && !shift &&
                (key == KEY_0 || key == KEY_1 || key == KEY_2
                    || key == KEY_3 || key == KEY_4 || key == KEY_5
                    || key == KEY_6 || key == KEY_7 || key == KEY_8
                    || key == KEY_9)) {
            int digit;
            switch (key) {
                case KEY_0: digit = 0; break;
                case KEY_1: digit = 1; break;
                case KEY_2: digit = 2; break;
                case KEY_3: digit = 3; break;
                case KEY_4: digit = 4; break;
                case KEY_5: digit = 5; break;
                case KEY_6: digit = 6; break;
                case KEY_7: digit = 7; break;
                case KEY_8: digit = 8; break;
                case KEY_9: digit = 9; break;
            }
            if (incomplete_argtype == ARG_FUNC && digit > 4) {
                squeak();
                return;
            }
            if ((incomplete_command == CMD_RTNERR || incomplete_command == CMD_RAISE)
                    && !incomplete_ind && digit > 8) {
                squeak();
                return;
            }
            incomplete_num = incomplete_num * 10 + digit;
            incomplete_length++;
            if (incomplete_length == incomplete_maxdigits) {
                if (incomplete_command == CMD_GOTOROW) {
                    pending_command_arg.val.num = incomplete_num;
                    vartype *m;
                    int err = matedit_get(&m);
                    if (err == ERR_NONE && m->type == TYPE_LIST) {
                        incomplete_num = 1;
                        goto do_goto2;
                    }
                    if ((flags.f.trace_print || flags.f.normal_print) && flags.f.printer_exists) {
                        arg_struct arg;
                        arg.type = ARGTYPE_NUM;
                        arg.val.num = incomplete_num;
                        print_command(CMD_GOTOROW, &arg);
                    }
                    start_incomplete_command(CMD_GOTOCOLUMN);
                    return;
                } else if (incomplete_command == CMD_GOTOCOLUMN) {
                    do_goto2:
                    if ((flags.f.trace_print || flags.f.normal_print) && flags.f.printer_exists) {
                        arg_struct arg;
                        arg.type = ARGTYPE_NUM;
                        arg.val.num = incomplete_num;
                        print_command(CMD_GOTOCOLUMN, &arg);
                    }
                    matedit_goto(pending_command_arg.val.num, incomplete_num);
                    pending_command = CMD_NONE;
                    finish_command_entry(true);
                    return;
                }
                pending_command = incomplete_command;
                pending_command_arg.type =
                            incomplete_ind ? ARGTYPE_IND_NUM : ARGTYPE_NUM;
                pending_command_arg.length = incomplete_maxdigits;
                if (!incomplete_ind &&
                        incomplete_argtype == ARG_NUM11 && incomplete_num > 11)
                    incomplete_num = 11;
                pending_command_arg.val.num = incomplete_num;
                finish_command_entry(true);
                return;
            } else
                set_menu(MENULEVEL_COMMAND, MENU_NONE);
            redisplay();
            return;
        }

        if (incomplete_length < incomplete_maxdigits
                    && !shift && key == KEY_BSP) {
            if (incomplete_length == 0) {
                pending_command = CMD_NULL;
                finish_command_entry(false);
                return;
            } else {
                incomplete_length--;
                incomplete_num /= 10;
                if (incomplete_length == 0) {
                    if (incomplete_command >= CMD_KEY1G
                            && incomplete_command <= CMD_KEY9X)
                        start_incomplete_command(
                                incomplete_command <= CMD_KEY9G ? CMD_KEYG
                                                                : CMD_KEYX);
                    else if (incomplete_argtype == ARG_VAR)
                        if (mode_appmenu == MENU_VARMENU)
                            set_menu(MENULEVEL_COMMAND, MENU_VARMENU);
                        else if (mode_appmenu == MENU_INTEG_PARAMS)
                            set_menu(MENULEVEL_COMMAND, MENU_INTEG_PARAMS);
                        else if (mode_appmenu >= MENU_TVM_APP1 && mode_appmenu <= MENU_TVM_TABLE)
                            set_menu(MENULEVEL_COMMAND, MENU_TVM_PARAMS);
                        else
                            set_catalog_menu(CATSECT_VARS_ONLY);
                    else if (incomplete_ind)
                        set_catalog_menu(CATSECT_REAL_ONLY);
                    else if (incomplete_argtype == ARG_REAL)
                        if (mode_appmenu == MENU_VARMENU)
                            set_menu(MENULEVEL_COMMAND, MENU_VARMENU);
                        else if (mode_appmenu == MENU_INTEG_PARAMS)
                            set_menu(MENULEVEL_COMMAND, MENU_INTEG_PARAMS);
                        else if (mode_appmenu >= MENU_TVM_APP1 && mode_appmenu <= MENU_TVM_TABLE)
                            set_menu(MENULEVEL_COMMAND, MENU_TVM_PARAMS);
                        else
                            set_catalog_menu(CATSECT_REAL_ONLY);
                    else if (incomplete_argtype == ARG_LBL)
                        set_catalog_menu(CATSECT_PGM_ONLY);
                    else if (incomplete_command == CMD_GTODOT)
                        set_menu(MENULEVEL_COMMAND, MENU_IND);
                    else if (incomplete_command == CMD_LBL)
                        set_menu(MENULEVEL_COMMAND, MENU_ALPHA1);
                }
                redisplay();
                return;
            }
        }

        /* Some bad key... */
        squeak();
        return;

    } else {
        /* incomplete_alpha */

        int menukey;
        const menu_spec *m;
        char c;

        do_incomplete_alpha:
        m = NULL;

        if (key >= 1024 && key < 2048) {
            c = key - 1024;
            goto handle_char;
        } else if (mode_commandmenu != MENU_NONE
                && (menukey = find_menu_key(key)) != -1) {
            const menu_item_spec *mi;
            m = menus + mode_commandmenu;
            mi = m->child + menukey;
            if (mi->menuid != MENU_NONE) {
                set_menu(MENULEVEL_COMMAND, mi->menuid);
                redisplay();
                return;
            }
            c = mi->title[0];
            if (shift && c >= 'A' && c <= 'Z')
                c += 'a' - 'A';
            handle_char:
            if (incomplete_length < (incomplete_argtype == ARG_XSTR ? 50 : 7))
                incomplete_str[incomplete_length++] = c;
            if (m != NULL)
                set_menu(MENULEVEL_COMMAND, m->parent);
            if (core_settings.auto_repeat) {
                repeating = 2;
                repeating_key = c + 1024;
                repeating_shift = 0;
            }
            /* incomplete_alpha can be 0 at this point if
             * the command is CMD_LBL. */
            incomplete_alpha = true;
            redisplay();
            return;
        }

        if ((incomplete_argtype == ARG_NAMED
                    || incomplete_argtype == ARG_PRGM
                    || incomplete_argtype == ARG_RVAR
                    || incomplete_argtype == ARG_MAT
                    || incomplete_argtype == ARG_DIR)
                && incomplete_command != CMD_ASSIGNa
                && incomplete_command != CMD_CLP
                && incomplete_command != CMD_PRP
                && incomplete_command != CMD_MVAR
                && incomplete_command != CMD_GSTO
                && incomplete_command != CMD_GRCL
                && !incomplete_ind
                && incomplete_length == 0
                && (mode_commandmenu < MENU_ALPHA1
                    || mode_commandmenu > MENU_ALPHA_MISC2)
                && !shift && key == KEY_DOT) {
            incomplete_ind = true;
            incomplete_alpha = false;
            set_catalog_menu(CATSECT_REAL_ONLY);
            redisplay();
            return;
        } else if ((incomplete_argtype == ARG_M_STK
                    || incomplete_argtype == ARG_L_STK)
                && !incomplete_ind
                && incomplete_length == 0
                && (mode_commandmenu < MENU_ALPHA1
                    || mode_commandmenu > MENU_ALPHA_MISC2)
                && !shift && key == KEY_DOT) {
            set_menu(MENULEVEL_COMMAND, MENU_IND_ST);
            redisplay();
            return;
        }

        if (incomplete_argtype == ARG_EQN
                && !incomplete_ind
                && incomplete_length == 0
                /* Note that we're letting KEY_DOT go to the IND/ST
                 * menu if on the first row of ALPHA; otherwise, if
                 * no EQN variables existed, we wouldn't be able to
                 * do this att all.
                 */
                && (mode_commandmenu < MENU_ALPHA2
                    || mode_commandmenu > MENU_ALPHA_MISC2)
                && !shift && key == KEY_DOT) {
            incomplete_ind = false;
            incomplete_alpha = false;
            set_menu(MENULEVEL_COMMAND, MENU_IND_ST);
            redisplay();
            return;
        }

        if (shift && key == KEY_ADD) {
            if (mode_commandmenu == MENU_CATALOG)
                squeak();
            else {
                set_catalog_menu(CATSECT_TOP);
                redisplay();
            }
            return;
        }

        /* Handle keys that represent characters */
        if (mode_commandmenu == MENU_CATALOG)
            goto nocharkey1;
        if (!shift) {
            switch (key) {
                case KEY_0:   c = '0'; break;
                case KEY_1:   c = '1'; break;
                case KEY_2:   c = '2'; break;
                case KEY_3:   c = '3'; break;
                case KEY_4:   c = '4'; break;
                case KEY_5:   c = '5'; break;
                case KEY_6:   c = '6'; break;
                case KEY_7:   c = '7'; break;
                case KEY_8:   c = '8'; break;
                case KEY_9:   c = '9'; break;
                case KEY_DOT: c = '.'; break;
                case KEY_E:   c = 24;  break;
                case KEY_DIV: c = 0;   break;
                case KEY_MUL: c = 1;   break;
                case KEY_SUB: c = '-'; break;
                case KEY_ADD: c = '+'; break;
                default: goto nocharkey1;
            }
        } else {
            switch (key) {
                case KEY_RCL: c = '%'; break;
                case KEY_RDN: c = 7;   break;
                default: goto nocharkey1;
            }
        }
        if (incomplete_length < (incomplete_argtype == ARG_XSTR ? 50 : 7))
            incomplete_str[incomplete_length++] = c;
        if (core_settings.auto_repeat) {
            repeating = 2;
            repeating_key = c + 1024;
            repeating_shift = 0;
        }
        /* incomplete_alpha can be 0 at this point if
         * the command is CMD_LBL. */
        incomplete_alpha = true;
        redisplay();
        return;
        nocharkey1:
        /* End of handling keys that represent characters */

        if (!shift && (key == KEY_UP || key == KEY_DOWN)) {
            const menu_spec *m = menus + mode_commandmenu;
            int nextmenu = key == KEY_UP ? m->prev : m->next;
            if (nextmenu != MENU_NONE) {
                set_menu(MENULEVEL_COMMAND, nextmenu);
                redisplay();
            }
            return;
        }

        if (key == KEY_EXIT) {
            const menu_spec *m;
            if (mode_commandmenu == MENU_NONE) {
                pending_command = CMD_CANCELLED;
                finish_command_entry(false);
                return;
            }
            if (mode_commandmenu == MENU_CATALOG) {
                int catsect = get_cat_section();
                if (catsect == CATSECT_PGM
                        || catsect == CATSECT_REAL
                        || catsect == CATSECT_CPX
                        || catsect == CATSECT_MAT) {
                    set_cat_section(CATSECT_TOP);
                    redisplay();
                    return;
                } else if (catsect == CATSECT_DIRS) {
                    set_cat_section((skin_flags & 1) == 0 ? CATSECT_TOP : CATSECT_MORE);
                    redisplay();
                    return;
                } else if (catsect >= CATSECT_UNITS_1
                        || catsect <= CATSECT_UNITS_3) {
                    set_cat_section((skin_flags & 2) == 0 ? CATSECT_TOP : CATSECT_MORE);
                    redisplay();
                    return;
                } else if (catsect == CATSECT_LIST
                        || catsect == CATSECT_EQN
                        || catsect == CATSECT_OTHER) {
                    set_cat_section(CATSECT_MORE);
                    redisplay();
                    return;
                } else if (catsect == CATSECT_FCN) {
                    set_cat_section((skin_flags & 1) == 0 ? CATSECT_MORE : CATSECT_TOP);
                    redisplay();
                    return;
                }
            }
            m = menus + mode_commandmenu;
            set_menu(MENULEVEL_COMMAND, m->parent);
            if (mode_commandmenu == MENU_NONE) {
                pending_command = CMD_CANCELLED;
                finish_command_entry(false);
            } else
                redisplay();
            return;
        }

        if (!shift && key == KEY_BSP) {
            if (incomplete_command >= CMD_KEY1G
                    && incomplete_command <= CMD_KEY9X) {
                if (incomplete_length == 0) {
                    if (mode_commandmenu >= MENU_ALPHA1
                            && mode_commandmenu <= MENU_ALPHA_MISC2)
                        start_incomplete_command(
                                incomplete_command <= CMD_KEY9G
                                        ? CMD_KEYG : CMD_KEYX);
                    else {
                        pending_command = CMD_NULL;
                        finish_command_entry(false);
                    }
                } else {
                    incomplete_length--;
                    redisplay();
                }
                return;
            }
            if (incomplete_length == 0) {
                int catsect;
                if (mode_commandmenu >= MENU_ALPHA1
                        && mode_commandmenu <= MENU_ALPHA_MISC2) {
                    if (incomplete_ind)
                        goto out_of_alpha;
                    if (incomplete_command == CMD_GTODOT) {
                        incomplete_argtype = ARG_OTHER;
                        incomplete_maxdigits = 4;
                        incomplete_alpha = false;
                        set_menu(MENULEVEL_COMMAND, MENU_IND);
                        redisplay();
                        return;
                    } else if (incomplete_argtype == ARG_NAMED) {
                        if (incomplete_command == CMD_ASSIGNa)
                            set_catalog_menu(CATSECT_TOP);
                        else
                            set_catalog_menu(CATSECT_VARS_ONLY);
                        if (incomplete_ind)
                            goto out_of_alpha;
                    } else if (incomplete_argtype == ARG_RVAR) {
                        if (incomplete_command == CMD_MVAR) {
                            pending_command = CMD_NULL;
                            finish_command_entry(false);
                        } else
                            goto out_of_alpha;
                    } else if (incomplete_argtype == ARG_MAT) {
                        if (vars_exist(CATSECT_MAT_LIST_ONLY))
                            set_catalog_menu(CATSECT_MAT_LIST_ONLY);
                        else
                            set_menu(MENULEVEL_COMMAND, MENU_NONE);
                    } else if (incomplete_argtype == ARG_M_STK) {
                        if (vars_exist(CATSECT_MAT))
                            set_catalog_menu(CATSECT_MAT_ONLY);
                        else
                            set_menu(MENULEVEL_COMMAND, MENU_NONE);
                    } else if (incomplete_argtype == ARG_L_STK) {
                        if (vars_exist(CATSECT_LIST))
                            set_catalog_menu(CATSECT_LIST_ONLY);
                        else
                            set_menu(MENULEVEL_COMMAND, MENU_NONE);
                    } else if (incomplete_argtype == ARG_DIR) {
                        if (cwd->children_count != 0)
                            set_catalog_menu(CATSECT_DIRS_ONLY);
                        else
                            set_menu(MENULEVEL_COMMAND, MENU_NONE);
                    } else if (incomplete_argtype == ARG_EQN) {
                        if (vars_exist(CATSECT_EQN))
                            set_catalog_menu(CATSECT_EQN_ONLY);
                        else
                            set_menu(MENULEVEL_COMMAND, MENU_NONE);
                    } else if (incomplete_argtype == ARG_PRGM)
                        set_catalog_menu(CATSECT_PGM_ONLY);
                    else if (incomplete_argtype == ARG_XSTR) {
                        pending_command = CMD_NULL;
                        finish_command_entry(false);
                    } else
                        goto out_of_alpha;
                    redisplay();
                } else if (mode_commandmenu == MENU_CATALOG
                        && ((catsect = get_cat_section()) == CATSECT_PGM
                                || catsect == CATSECT_REAL
                                || catsect == CATSECT_CPX
                                || catsect == CATSECT_MAT)) {
                    set_catalog_menu(CATSECT_TOP);
                    redisplay();
                } else if (mode_commandmenu == MENU_CATALOG
                        && catsect == CATSECT_DIRS) {
                    set_catalog_menu((skin_flags & 1) == 0 ? CATSECT_TOP : CATSECT_MORE);
                    redisplay();
                } else if (mode_commandmenu == MENU_CATALOG
                        && catsect >= CATSECT_UNITS_1
                        && catsect <= CATSECT_UNITS_3) {
                    set_catalog_menu((skin_flags & 2) == 0 ? CATSECT_TOP : CATSECT_MORE);
                    redisplay();
                } else if (mode_commandmenu == MENU_CATALOG
                        && catsect >= CATSECT_UNITS_LENG
                        && catsect <= CATSECT_UNITS_MASS) {
                    set_catalog_menu(CATSECT_UNITS_1);
                    redisplay();
                } else if (mode_commandmenu == MENU_CATALOG
                        && catsect >= CATSECT_UNITS_FORCE
                        && catsect <= CATSECT_UNITS_ELEC) {
                    set_catalog_menu(CATSECT_UNITS_2);
                    redisplay();
                } else if (mode_commandmenu == MENU_CATALOG
                        && catsect >= CATSECT_UNITS_ANGL
                        && catsect <= CATSECT_UNITS_VISC) {
                    set_catalog_menu(CATSECT_UNITS_3);
                    redisplay();
                } else if (mode_commandmenu == MENU_CATALOG
                        && (catsect == CATSECT_LIST
                                || catsect == CATSECT_EQN
                                || catsect == CATSECT_EQN_NAMED
                                || catsect == CATSECT_OTHER)) {
                    set_catalog_menu(CATSECT_MORE);
                    redisplay();
                } else if (mode_commandmenu == MENU_CATALOG
                        && catsect == CATSECT_FCN) {
                    set_catalog_menu((skin_flags & 1) == 0 ? CATSECT_MORE : CATSECT_TOP);
                    redisplay();
                } else if (mode_commandmenu == MENU_CATALOG
                        && (catsect == CATSECT_EXT_TIME
                                || catsect == CATSECT_EXT_XFCN
                                || catsect == CATSECT_EXT_BASE
                                || catsect == CATSECT_EXT_PRGM
                                || catsect == CATSECT_EXT_STR
                                || catsect == CATSECT_EXT_STK)) {
                    set_catalog_menu(CATSECT_EXT_1);
                    redisplay();
                } else if (mode_commandmenu == MENU_CATALOG
                        && (catsect == CATSECT_EXT_EQN
                                || catsect == CATSECT_EXT_UNIT
                                || catsect == CATSECT_EXT_STAT
                                || catsect == CATSECT_EXT_DIR
                                || catsect == CATSECT_EXT_DISP
                                || catsect == CATSECT_EXT_MISC)) {
                    set_catalog_menu(CATSECT_EXT_2);
                    redisplay();
                } else if (mode_commandmenu == MENU_CATALOG
                        && (catsect == CATSECT_EXT_0_CMP
                                || catsect == CATSECT_EXT_X_CMP)) {
                    set_catalog_menu(CATSECT_EXT_PRGM);
                    set_cat_row(3);
                    redisplay();
                } else {
                    pending_command = CMD_NULL;
                    finish_command_entry(false);
                }
                return;
            }
            incomplete_length--;
            if (incomplete_length == 0) {
                if (incomplete_ind
                        && mode_commandmenu >= MENU_ALPHA1
                        && mode_commandmenu <= MENU_ALPHA_MISC2)
                    goto out_of_alpha;
                if (incomplete_command == CMD_GTODOT) {
                    incomplete_argtype = ARG_OTHER;
                    incomplete_maxdigits = 4;
                    incomplete_alpha = false;
                    set_menu(MENULEVEL_COMMAND, MENU_IND);
                    redisplay();
                    return;
                } else if (incomplete_argtype == ARG_NAMED) {
                    if (incomplete_command == CMD_ASSIGNa)
                        set_catalog_menu(CATSECT_TOP);
                    else
                        set_catalog_menu(CATSECT_VARS_ONLY);
                    if (incomplete_ind)
                        goto out_of_alpha;
                } else if (incomplete_argtype == ARG_RVAR) {
                    if (vars_exist(CATSECT_REAL_ONLY))
                        set_catalog_menu(CATSECT_REAL_ONLY);
                } else if (incomplete_argtype == ARG_MAT) {
                    if (vars_exist(CATSECT_MAT_LIST_ONLY))
                        set_catalog_menu(CATSECT_MAT_LIST_ONLY);
                } else if (incomplete_argtype == ARG_M_STK) {
                    if (vars_exist(CATSECT_MAT))
                        set_catalog_menu(CATSECT_MAT_ONLY);
                } else if (incomplete_argtype == ARG_L_STK) {
                    if (vars_exist(CATSECT_LIST))
                        set_catalog_menu(CATSECT_LIST_ONLY);
                } else if (incomplete_argtype == ARG_DIR) {
                    if (cwd->children_count != 0)
                        set_catalog_menu(CATSECT_DIRS_ONLY);
                } else if (incomplete_argtype == ARG_EQN) {
                    if (vars_exist(CATSECT_EQN_ONLY))
                        set_catalog_menu(CATSECT_EQN_ONLY);
                } else if (incomplete_argtype == ARG_PRGM)
                    set_catalog_menu(CATSECT_PGM_ONLY);
                else if (incomplete_argtype == ARG_XSTR) {
                    /* Stay in ALPHA mode */
                } else {
                    out_of_alpha:
                    if (incomplete_ind
                            || incomplete_argtype != ARG_RVAR)
                        incomplete_alpha = false;
                    if (incomplete_ind)
                        set_catalog_menu(CATSECT_REAL_ONLY);
                    else if (incomplete_argtype == ARG_VAR)
                        if (mode_appmenu == MENU_VARMENU)
                            set_menu(MENULEVEL_COMMAND, MENU_VARMENU);
                        else if (mode_appmenu == MENU_INTEG_PARAMS)
                            set_menu(MENULEVEL_COMMAND, MENU_INTEG_PARAMS);
                        else if (mode_appmenu >= MENU_TVM_APP1 && mode_appmenu <= MENU_TVM_TABLE)
                            set_menu(MENULEVEL_COMMAND, MENU_TVM_PARAMS);
                        else
                            set_catalog_menu(CATSECT_VARS_ONLY);
                    else if (incomplete_argtype == ARG_REAL)
                        if (mode_appmenu == MENU_VARMENU)
                            set_menu(MENULEVEL_COMMAND, MENU_VARMENU);
                        else if (mode_appmenu == MENU_INTEG_PARAMS)
                            set_menu(MENULEVEL_COMMAND, MENU_INTEG_PARAMS);
                        else if (mode_appmenu >= MENU_TVM_APP1 && mode_appmenu <= MENU_TVM_TABLE)
                            set_menu(MENULEVEL_COMMAND, MENU_TVM_PARAMS);
                        else
                            set_catalog_menu(CATSECT_REAL_ONLY);
                    else if (incomplete_argtype == ARG_LBL)
                        set_catalog_menu(CATSECT_PGM_ONLY);
                    else if (incomplete_command == CMD_GTODOT)
                        set_menu(MENULEVEL_COMMAND, MENU_IND);
                    else if (incomplete_command == CMD_LBL)
                        set_menu(MENULEVEL_COMMAND, MENU_ALPHA1);
                    else
                        set_menu(MENULEVEL_COMMAND, MENU_NONE);
                }
            } else if (incomplete_alpha && core_settings.auto_repeat) {
                repeating = 2;
                repeating_key = KEY_BSP;
                repeating_shift = 0;
            }
            redisplay();
            return;
        }

        if (key == KEY_ENTER) {
            int i;
            if (incomplete_length == 0) {
                int catsect;
                if (mode_commandmenu == MENU_NONE
                        || (mode_commandmenu == MENU_CATALOG
                            && ((catsect = get_cat_section()) == CATSECT_TOP
                            || catsect == CATSECT_MORE
                            || catsect == CATSECT_EXT_1
                            || catsect == CATSECT_EXT_2
                            || catsect == CATSECT_PGM_ONLY
                            || catsect == CATSECT_REAL_ONLY
                            || catsect == CATSECT_MAT_ONLY
                            || catsect == CATSECT_MAT_LIST_ONLY
                            || catsect == CATSECT_LIST_ONLY
                            || catsect == CATSECT_EQN_ONLY
                            || catsect == CATSECT_VARS_ONLY
                            || catsect == CATSECT_LIST_STR_ONLY
                            || catsect == CATSECT_DIRS_ONLY))) {
                    set_menu(MENULEVEL_COMMAND, MENU_ALPHA1);
                    redisplay();
                    return;
                } else if ((incomplete_command != CMD_ASSIGNa
                        && incomplete_command != CMD_CLP
                        && incomplete_command != CMD_PRP
                        && incomplete_command != CMD_XSTR)
                        || mode_commandmenu < MENU_ALPHA1
                        || mode_commandmenu > MENU_ALPHA_MISC2) {
                    squeak();
                    return;
                }
                /* ASSIGN, CLP, or PRP, XSTR, alpha menu active, zero-length string:
                 * these are the only cases where an empty string is allowed
                 * as an argument. We fall through to the command completion
                 * code below.
                 */
            }

            pending_command = incomplete_command;

            if (!incomplete_ind
                    && (incomplete_command == CMD_GTO
                        || incomplete_command == CMD_XEQ
                        || incomplete_command == CMD_LBL
                        || (incomplete_command >= CMD_KEY1G
                            && incomplete_command <= CMD_KEY9X))
                    && incomplete_length == 1
                    && ((incomplete_str[0] >= 'A'
                            && incomplete_str[0] <= 'J')
                        || (incomplete_str[0] >= 'a'
                            && incomplete_str[0] <= 'e'))) {
                /* Display XEQ "A" briefly before changing to XEQ A */
                mode_command_entry = false;
                pending_command_arg.type = ARGTYPE_STR;
                pending_command_arg.length = 1;
                pending_command_arg.val.text[0] = incomplete_str[0];
                if (flags.f.prgm_mode) {
                    flags.f.prgm_mode = 0;
                    redisplay();
                    flags.f.prgm_mode = 1;
                    shell_delay(125);
                } else
                    redisplay();
                pending_command_arg.type = ARGTYPE_LCLBL;
                pending_command_arg.val.lclbl = incomplete_str[0];
                set_menu(MENULEVEL_COMMAND, MENU_NONE);
                finish_command_entry(false);
                return;
            } else {
                if (incomplete_argtype == ARG_XSTR) {
                    pending_command_arg.type = ARGTYPE_XSTR;
                    pending_command_arg.val.xstr = incomplete_str;
                } else {
                    pending_command_arg.type =
                            incomplete_ind ? ARGTYPE_IND_STR : ARGTYPE_STR;
                    for (i = 0; i < incomplete_length; i++)
                        pending_command_arg.val.text[i] = incomplete_str[i];
                }
                pending_command_arg.length = incomplete_length;

                if (!incomplete_ind && incomplete_command == CMD_XEQ)
                    finish_xeq();
                else
                    finish_command_entry(true);
                return;
            }
        }

        squeak();
        return;
    }
}

void keydown_alpha_mode(int shift, int key) {
    int menukey;
    const menu_spec *m = NULL;
    char c;
    int command;

    if (key >= 1024 && key < 2048) {
        c = key - 1024;
        goto handle_char;
    }

    menukey = find_menu_key(key);
    if (menukey != -1) {
        const menu_item_spec *mi;
        m = menus + mode_alphamenu;
        mi = m->child + menukey;
        if (mi->menuid != MENU_NONE) {
            set_menu(MENULEVEL_ALPHA, mi->menuid);
            redisplay();
            return;
        }
        c = mi->title[0];
        if (shift && c >= 'A' && c <= 'Z')
            c += 'a' - 'A';

        handle_char:
        if (flags.f.prgm_mode) {
            if (!mode_alpha_entry) {
                if (!start_alpha_prgm_line()) {
                    if (!current_prgm.is_editable())
                        display_error(ERR_RESTRICTED_OPERATION);
                    else
                        display_error(ERR_PROGRAM_LOCKED);
                    redisplay();
                    return;
                }
            }
            if ((c & 128) != 0 && entered_string_length == 0)
                squeak();
            else if (entered_string_length < 15)
                entered_string[entered_string_length++] = c;
        } else {
            if (!mode_alpha_entry) {
                reg_alpha_length = 0;
                flags.f.alpha_data_input = 1;
                mode_alpha_entry = true;
            }
            append_alpha_char(c);
            if (reg_alpha_length == 44)
                squeak();
        }
        if (core_settings.auto_repeat) {
            repeating = 2;
            repeating_key = c + 1024;
            repeating_shift = 0;
        }

        if (m != NULL)
            set_menu(MENULEVEL_ALPHA, m->parent);
        redisplay();
        return;
    }

    /* Handle keys that represent characters */
    if (!shift) {
        switch (key) {
            case KEY_0:   c = '0'; break;
            case KEY_1:   c = '1'; break;
            case KEY_2:   c = '2'; break;
            case KEY_3:   c = '3'; break;
            case KEY_4:   c = '4'; break;
            case KEY_5:   c = '5'; break;
            case KEY_6:   c = '6'; break;
            case KEY_7:   c = '7'; break;
            case KEY_8:   c = '8'; break;
            case KEY_9:   c = '9'; break;
            case KEY_DOT: c = '.'; break;
            case KEY_E:   c = 24;  break;
            case KEY_DIV: c = 0;   break;
            case KEY_MUL: c = 1;   break;
            case KEY_SUB: c = '-'; break;
            case KEY_ADD: c = '+'; break;
            default: goto nocharkey2;
        }
    } else {
        switch (key) {
            case KEY_RCL: c = '%'; break;
            case KEY_RDN: c = 7;   break;
            default: goto nocharkey2;
        }
    }
    if (flags.f.prgm_mode) {
        if (!mode_alpha_entry) {
            if (!start_alpha_prgm_line()) {
                if (!current_prgm.is_editable())
                    display_error(ERR_RESTRICTED_OPERATION);
                else
                    display_error(ERR_PROGRAM_LOCKED);
                redisplay();
                return;
            }
        }
        if (entered_string_length < 15)
            entered_string[entered_string_length++] = c;
    } else {
        if (!mode_alpha_entry) {
            reg_alpha_length = 0;
            mode_alpha_entry = true;
            flags.f.alpha_data_input = 1;
        }
        append_alpha_char(c);
        if (reg_alpha_length == 44)
            squeak();
    }
    if (core_settings.auto_repeat) {
        repeating = 2;
        repeating_key = key;
        repeating_shift = shift;
    }
    redisplay();
    return;
    nocharkey2:
    /* End of handling keys that represent characters */

    if (!shift && (key == KEY_UP || key == KEY_DOWN)) {
        const menu_spec *m = menus + mode_alphamenu;
        int nextmenu = key == KEY_UP ? m->prev : m->next;
        if (nextmenu != MENU_NONE) {
            set_menu(MENULEVEL_ALPHA, nextmenu);
            redisplay();
        }
        return;
    }

    if (key == KEY_EXIT) {
        const menu_spec *m = menus + mode_alphamenu;
        set_menu(MENULEVEL_ALPHA, m->parent);
        if (mode_alphamenu == MENU_NONE) {
            if (mode_alpha_entry) {
                if (flags.f.prgm_mode)
                    finish_alpha_prgm_line();
                else if ((flags.f.trace_print || flags.f.normal_print)
                        && flags.f.printer_exists)
                    docmd_pra(NULL);
                mode_alpha_entry = false;
            }
            print_menu_trace("EXIT", 4);
            pending_command = CMD_CANCELLED;
        } else
            redisplay();
        return;
    }

    if (!shift && key == KEY_BSP) {
        if (flags.f.prgm_mode) {
            if (mode_alpha_entry) {
                if (entered_string_length > 0) {
                    if (core_settings.auto_repeat) {
                        repeating = 2;
                        repeating_key = key;
                        repeating_shift = shift;
                    }
                    entered_string_length--;
                } else
                    finish_alpha_prgm_line();
            } else {
                int4 line = pc2line(pc);
                if (line != 0) {
                    if (current_prgm.idx == dir_list[current_prgm.dir]->prgms_count - 1
                            && dir_list[current_prgm.dir]->prgms[current_prgm.idx].is_end(pc)) {
                        // .END.
                        pc = line2pc(line - 1);
                        move_prgm_highlight(-1);
                    } else if (!current_prgm.is_editable()) {
                        display_error(ERR_RESTRICTED_OPERATION);
                    } else if (current_prgm.is_locked()) {
                        display_error(ERR_PROGRAM_LOCKED);
                    } else if (current_prgm.idx < dir_list[current_prgm.dir]->prgms_count - 1
                            && dir_list[current_prgm.dir]->prgms[current_prgm.idx].is_end(pc)
                            && dir_list[current_prgm.dir]->prgms[current_prgm.idx + 1].locked) {
                        display_error(ERR_NEXT_PROGRAM_LOCKED);
                    } else {
                        delete_command(pc);
                        pc = line2pc(line - 1);
                        move_prgm_highlight(-1);
                    }
                }
                if (mode_alphamenu != MENU_ALPHA1
                        && mode_alphamenu != MENU_ALPHA2)
                    set_menu(MENULEVEL_ALPHA, menus[mode_alphamenu].parent);
            }
            redisplay();
            return;
        } else {
            if (mode_alpha_entry && reg_alpha_length > 0) {
                if (core_settings.auto_repeat) {
                    repeating = 2;
                    repeating_key = key;
                    repeating_shift = shift;
                }
                reg_alpha_length--;
                redisplay();
            } else
                pending_command = CMD_CLA;
            return;
        }
    }

    if (key == KEY_ENTER) {
        if (flags.f.prgm_mode) {
            if (mode_alpha_entry) {
                finish_alpha_prgm_line();
                set_menu(MENULEVEL_ALPHA, MENU_NONE);
            } else if (shift) {
                set_menu(MENULEVEL_ALPHA, MENU_NONE);
                print_menu_trace("ALPHA", 5);
            } else {
                if (start_alpha_prgm_line()) {
                    entered_string[0] = 127;
                    entered_string_length = 1;
                } else if (!current_prgm.is_editable())
                    display_error(ERR_RESTRICTED_OPERATION);
                else
                    display_error(ERR_PROGRAM_LOCKED);
            }
        } else {
            if (shift || mode_alpha_entry) {
                if (mode_alpha_entry
                        && (flags.f.trace_print || flags.f.normal_print)
                        && flags.f.printer_exists)
                    docmd_pra(NULL);
                mode_alpha_entry = false;
                set_menu(MENULEVEL_ALPHA, MENU_NONE);
            } else
                mode_alpha_entry = true;
        }
        redisplay();
        return;
    }

    if (key == 2048 + CMD_NULL) {
        handle_dcm_xeq();
        return;
    }

    command = CMD_CANCELLED;
    if (!shift) {
        switch (key) {
            case KEY_STO: command = CMD_ASTO; break;
            case KEY_RCL: command = CMD_ARCL; break;
            case KEY_RUN: command = CMD_RUN; break;
            default: command = key >= 2048 ? key - 2048 : CMD_NONE; break;
        }
    } else {
        switch (key) {
            case KEY_CHS: set_plainmenu(MENU_MODES1, "MODES", 5); break;
            case KEY_E: set_plainmenu(MENU_DISP1, "DISP", 4); break;
            case KEY_BSP: set_plainmenu(MENU_CLEAR1, "CLEAR", 5); break;
            case KEY_7: set_solve_integ(1); break;
            case KEY_8: set_solve_integ(0); break;
            case KEY_9: print_menu_trace("MATRIX", 6);
                        set_menu(MENULEVEL_APP, MENU_MATRIX1);
                        break;
            case KEY_DIV: print_menu_trace("STAT", 4);
                          set_menu(MENULEVEL_APP, MENU_STAT1);
                          break;
            case KEY_DOWN: command = CMD_SST; break;
            case KEY_4: print_menu_trace("BASE", 4);
                        set_menu(MENULEVEL_APP, MENU_BASE1);
                        if (mode_appmenu == MENU_BASE1) {
                            set_appmenu_exitcallback(2);
                            baseapp = 1;
                        }
                        break;
            case KEY_5: set_plainmenu(MENU_CONVERT1, "CONVERT", 7); break;
            case KEY_6: set_plainmenu(MENU_FLAGS, "FLAGS", 5); break;
            case KEY_MUL: set_plainmenu(MENU_PROB, "PROB", 4); break;
            case KEY_2: set_plainmenu(MENU_NONE, NULL, 0);
                        if (flags.f.prgm_mode) {
                            pending_command = CMD_CUSTOM;
                            return;
                        } else {
                            command = CMD_CUSTOM;
                            break;
                        }
            case KEY_3: set_plainmenu(MENU_PGM_FCN1, "PGM.FCN", 7); break;
            case KEY_SUB: set_plainmenu(MENU_PRINT1, "PRINT", 5); break;
            case KEY_0:
                if ((skin_flags & 4) == 0)
                    set_plainmenu(MENU_TOP_FCN, "TOP.FCN", 7);
                else
                    command = CMD_TVM;
                break;
            case KEY_DOT:
                show();
                pending_command = CMD_LINGER1;
                shell_request_timeout3(2000);
                return;
            case KEY_ADD: set_plainmenu(MENU_CATALOG, "CATALOG", 7); break;
            default: command = key >= 2048 ? key - 2048 : CMD_NONE; break;
        }
    }

    if (command == CMD_NONE) {
        squeak();
        return;
    }
    if (mode_alpha_entry) {
        if (flags.f.prgm_mode)
            finish_alpha_prgm_line();
        else if ((flags.f.trace_print || flags.f.normal_print)
                && flags.f.printer_exists)
            docmd_pra(NULL);
        mode_alpha_entry = false;
    }

    if (command == CMD_CANCELLED) {
        /* plainmenu or appmenu switch */
        set_menu(MENULEVEL_ALPHA, MENU_NONE);
        redisplay();
        return;
    } else
        do_interactive(command);
}

static bool ref_action_possible(bool lists_allowed) {
    if (flags.f.prgm_mode || sp < 0)
        return false;
    vartype *x = stack[sp];
    if (x->type == TYPE_DIR_REF || x->type == TYPE_PGM_REF || x->type == TYPE_VAR_REF)
        return true;
    if (!lists_allowed || x->type != TYPE_LIST)
        return false;
    vartype_list *list = (vartype_list *) x;
    if (list->size == 0)
        return false;
    for (int i = 0; i < list->size; i++) {
        x = list->array->data[i];
        if (x->type != TYPE_DIR_REF && x->type != TYPE_PGM_REF && x->type != TYPE_VAR_REF)
            return false;
    }
    return true;
}
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
