barnabyosborne-cmyk/Hp42s_calc/firmware/components/plus42core/core_main.h

/*****************************************************************************
 * Plus42 -- an enhanced HP-42S calculator simulator
 * Copyright (C) 2004-2026  Thomas Okken
 *
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
 * You should have received a copy of the GNU General Public License
 * along with this program; if not, see http://www.gnu.org/licenses/.
 *****************************************************************************/

#ifndef CORE_MAIN_H
#define CORE_MAIN_H 1

#include "free42.h"


/**********************************/
/* Shell/Core interface functions */
/**********************************/

/* core_init()
 *
 * This function initializes the emulator core.
 * The display size is communicated by 'rows' and 'cols', which are two-way
 * parameters. The shell will set these to whatever it prefers, given the
 * previous state or the requirements of the skin or whatever; the core will
 * accept these preferences if it performs a cold start, or it will replace
 * them with what it read from the state. If the shell can't accept the new size,
 * it will respond by calling core_repaint_display() with whatever is the
 * closest size it can manage.
 * If the read_state parameter is 1, the core should read saved state from the
 * file named by the state_file_name parameter; if read_state is 0, or if there
 * is a problem reading the saved state, it should perform a hard reset.
 */
void core_init(int *rows, int *cols, int read_state, const char *state_file_name);

/* core_save_state()
 *
 * This function is called by the mobile apps when they are placed in
 * background mode, and by the desktop apps when they are shutting down.
 * It writes all the simulator's persistent state to a file given by the
 * state_file_name parameter, creating it if it doesn't already exist.
 */
void core_save_state(const char *state_file_name);

/* core_cleanup()
 *
 * This function deletes the emulator core state from memory. It may be called
 * during app shutdown, although that's not really necessary unless you are
 * checking for memory leaks. It should be called between saving state and
 * loading a new state, that is, when switching states.
 */
void core_cleanup();

/* core_repaint_display()
 *
 * This function asks the emulator core to repaint the display. The core will
 * respond by immediately calling shell_blitter() to repaint the entire
 * display.
 * The shell uses this function to re-generate the display after switching
 * skins. It passes the number of character rows and columns to use for the
 * display, just like core_init(); the core should resize the display
 * accordingly, if needed.
 * The flags parameter is the value from the layout's Flags: line; it is
 * a combination of: 1 = don't swap FCN and DIRS; 2 = don't swap MEM and UNITS;
 * and 4 = do replace TOP.FCN with TVM.
 */
void core_repaint_display(int rows, int cols, int flags);

/* core_menu()
 *
 * The shell uses this function to check if a menu is active. This affects
 * whether or not clicking in the display, to activate menu keys, is
 * enabled.
 */
bool core_menu();

/* core_alpha_menu()
 *
 * The shell uses this function to check if the core is in "alpha" mode (i.e.
 * the ALPHA menu or any of its submenus is active). This affects how events
 * from the keyboard (the real PC keyboard, not the on-screen one emulated by
 * Free42) are handled: in alpha mode, printable ASCII characters are sent
 * straight to the core; outside alpha mode, all key events are translated
 * sequences of HP-42S key events according to the keymap file.
 * Returns: 0: ALPHA menu not active; 1: ALPHA menu active; 2: equation editor
 * active.
 */
int core_alpha_menu();

/* core_hex_menu()
 *
 * The shell uses this function to check if the core is in "hex" mode (i.e.
 * the A..F submenu of the BASE application is active). This affects how events
 * from the keyboard (the real PC keyboard, not the on-screen one emulated by
 * Free42) are handled: in hex mode, 'A' through 'F' and 'a' through 'f' are
 * translated to keycodes 1 through 6, regardless of the keyboard map.
 */
bool core_hex_menu();

/* core_special_menu_key()
 *
 * The shell can call this function if the physical cursor left, cursor right,
 * or delete keys have been pressed; the core will return the appropriate
 * menu key to trigger. This is to support menus like the matrix editor.
 * Which can be: 1=left, 2=shift left, 3=right, 4=shift right, 5=del.
 * The return value is a menu key number 1-6, or 0 if no special menu key
 * is available.
 */
int core_special_menu_key(int which);

/* core_keydown()
 *
 * This function informs the emulator core that an HP-42S key was pressed. Keys
 * are identified using a numeric key code, which corresponds to the key
 * numbers returned by the HP-42S 'GETKEY' function: 'Sigma+' is 1, '1/x' is 2,
 * and so on. The shift key is 28 -- 'shift' handling is performed by the
 * emulator core, so it needs to receive raw key codes, unlike the 'GETKEY'
 * function, which handles the shift key itself and then returns key codes in
 * the range 38..74 for shifted keys. The core_keydown() function should only
 * be called with key codes from 1 to 37, inclusive.
 * Keys that cause immediate action should be handled immediately when this
 * function is called, and calls to core_keytimeout1(), core_keytimeout2(),
 * and core_keyup() should be ignored (until the next core_keydown(), that
 * is!). Keys that are handled only when *released* should not be handled
 * immediately when this function is called; the emulator core should store the
 * key code, handle core_keytimeout1() and core_keytimeout2() as appropriate,
 * and not perform any action until core_keyup() is called.
 * RETURNS: a flag indicating whether or not the front end should call this
 * function again as soon as possible. This will be 1 if the calculator is
 * running a user program, and is only returning execution to the shell because
 * it has detected that there is a pending event.
 * The 'enqueued' pointer is a return parameter that the emulator core uses to
 * tell the shell if it has enqueued the keystroke. If this is 1, the shell
 * should not send call timeout1(), timeout2(), or keyup() for this keystroke.
 * NOTE: a key code of 0 (zero) signifies 'no key'; this is needed if the shell
 * is calling this function because it asked to be called (by returning 1 the
 * last time) but no keystrokes are available. It is not necessary to balance
 * the keydown call with a keyup in this case.
 * The 'repeat' pointer is a return parameter that the emulator core uses to
 * ask the shell to auto-repeat the current key. If this is set to 1 or 2, the
 * shell will not call timeout1() and timeout2(), but will repeatedly call
 * core_repeat() until the key is released. (1 requests a slow repeat rate, for
 * SST/BST; 2 requests a fast repeat rate, for number/alpha entry, and 3
 * requests an extra-slow repeat rate, for up/down in the equation editor's
 * list view.)
 */
bool core_keydown(int key, bool *enqueued, int *repeat);

/* core_keydown_command()
 *
 * This function is equivalent to core_keydown(), except that instead of a key
 * number, it expects a command name. This can be used to implement skins that
 * map skin keys or keyboard keys directly to calculator commands, which is
 * useful if you want to assign commands to the keyboard that aren't directly
 * mapped on the original calculator. Without this, you'd have to create such a
 * mapping by creating a macro that performs XEQ and spells out the command
 * name, or selects the command from a menu or the FCN catalog, all of which
 * have potentially undesirable side effects.
 * The type parameter indicates the type of the name parameter: 0 means a
 * built-in function, as described above; 1 means a LBL name, requesting an
 * XEQ "name" to be performed; and 2 requests to insert literal text. Type 2
 * will only happen when ALPHA mode is active.
 * Type 0 names are specified in the layout file by using "" delimiters,
 * type 1 is specified using `` delimiters, and type 2 is specified using ''
 * delimiters.
 */
bool core_keydown_command(const char *name, int type, bool *enqueued, int *repeat);

/* core_repeat()
 *
 * This function is called by the shell to signal auto-repeating key events.
 * It is the core's responsibility to keep track of *which* key is repeating.
 * The function can return 0, to request repeating to stop; 1, which requests
 * a slow repeat rate, for SST/BST; or 2, which requests a fast repeat rate,
 * for number/alpha entry; or 3, for an extra-slow repeat rate, for the
 * equation editor's list view.
 */
int core_repeat();

/* core_keytimeout1()
 *
 * This function informs the emulator core that the currently pressed key has
 * been held down for 1/4 of a second. (If the key is released less than 1/4
 * second after being pressed, this function is not called.)
 * For keys that do not execute immediately, this marks the moment when the
 * calculator displays the key's function name.
 */
void core_keytimeout1();

/* core_keytimeout2()
 *
 * This function informs the emulator core that 2 seconds have passed since
 * core_keytimeout1() was called. (If the key is released less than 2 seconds
 * after core_keytimeout1() is called, this function is not called.)
 * This marks the moment when the calculator switches from displaying the key's
 * function name to displaying 'NULL' (informing the user that the key has been
 * annulled and so no operation will be performed when it is released).
 */
void core_keytimeout2();

/* core_timeout3()
 *
 * A wakeup call that the core can request by calling shell_request_timeout3().
 * Used to implement PSE and the brief linger period after MEM, SHOW, and
 * shift-VARMENU. The 'repaint' parameter says whether the callback is invoked
 * because the timeout period expired (1), or because a key event is on its
 * way (0); if a key event is on its way, the emulator core should not repaint
 * the screen, in order to avoid flashing.
 * If the function returns 'true', this means that the timeout was used for
 * PSE, and the shell should resume program execution.
 */
bool core_timeout3(bool repaint);

/* core_keyup()
 *
 * This function informs the emulator core that the currently pressed key (that
 * is, the one whose key code was given to it in the most recent call to
 * core_keydown()) has been released.
 * This function is always called when a key is released, regardless of how
 * long it was held down, and regardless of whether or not core_keytimeout1()
 * and core_keytimeout2() were called following the most recent
 * core_keydown().
 * RETURNS: a flag indicating whether or not the front end should call this
 * function again as soon as possible. This will be 1 if the calculator is
 * running a user program, and is only returning execution to the shell because
 * it has detected that there is a pending event.
 */
bool core_keyup();

/* core_powercycle()
 *
 * This tells the core to pretend that a power cycle has just taken place.
 * Usually called right after core_init().
 * The core should respond by performing power-down activities, immediately
 * followed by power-up activities. (The emulator core is never expected to
 * actually emulate the state of *being* off -- the host environment can handle
 * being off just fine by itself, thank you very much -- it's just the side
 * effects of the *transitions* of a power cycle we want emulated (stopping
 * program execution, restarting it if flag 11 is set, clearing flags 11 and
 * 44, and maybe other stuff once I discover it).
 * This function returns a flag telling the shell whether or not the core wants
 * to run again -- this will be true if flag 11 was set, so there's program
 * execution to be done.
 */
bool core_powercycle();

/* core_list_programs()
 *
 * This function is called by the shell when the user activates the Export
 * Program command. The core returns a list of program names, corresponding to
 * the programs as they appear in the PGM catalog, but in reverse order (the
 * .END. is last). Each item corresponds to one program, and consists of the
 * names of all the global labels in that program. Programs that contain no
 * global labels are given the name END (or .END.).
 * The indexes into the list of program names should be used to identify
 * programs to core_export_programs().
 * The function returns a dynamically allocated buffer. The first four bytes
 * are the number of programs returned (as a big-endian int) which is
 * guaranteed to always be at least 1. This is followed by a sequence of
 * 'program_count' null-terminated strings.
 * This function will return NULL if it fails to allocate the buffer.
 * The caller should free() the buffer once it is finished using it.
 */
char *core_list_programs();

/* core_program_size()
 * This function returns the size of a program, specified by its index.
 * The indexes correspond to those returned by core_list_programs(). The caller
 * should *only* use those indexes; any indexes outside of that range will
 * cause weirdness and mayhem.
 * The size returned by this function does not include the 3 bytes for the
 * END; this matches what the HP-42S displays on line 00, but the caller should
 * be aware that the actual byte stream produced by core_export_programs() will
 * be 3 bytes longer.
 */
int4 core_program_size(int prgm_index);

/* core_export_programs()
 *
 * This function is called by the shell after the user has selected a nonempty
 * set of programs (from the list returned by core_list_programs()) and
 * confirmed the operation (supplied a file name etc.).
 * The 'count' parameter indicates how many programs are to be exported; the
 * 'indexes' parameter is an array of program indexes.
 * When called by the core during state file saving, raw_file_name will be
 * NULL, which tells it to write to the already-opened state file.
 */
void core_export_programs(int count, const int *indexes, const char *raw_file_name);

/* core_import_programs()
 *
 * This function imports programs from the file named by the raw_file_name
 * parameter. It will read at most num_progs programs. When called by the
 * shell, num_progs should be 0, which tells it to load the entire file.
 * When called by the core during state file loading, raw_file_name will be
 * NULL, which tells it to read from the already-opened state file.
 */
void core_import_programs(int num_progs, const char *raw_file_name);

/* core_copy()
 *
 * Returns a string representation of the contents of the X register. In
 * program mode, returns a listing of the current program. I alpha mode,
 * returns the contents of the alpha register.
 * Used by the shell to implement the Copy command.
 * The caller should free the returned text using free(3).
 */
char *core_copy();

/* core_paste()
 *
 * In normal mode, puts the given value on the stack, parsing it as tab-
 * delimited spreadsheet cells, complex or real scalars, or, if nothing
 * matches, as a simple string. In program mode, attempts to parse the text as
 * a program listing, and adds the converted code as a new program at the end
 * of program memory. In alpha mode, pastes the text in the alpha register,
 * appending it to whatever is already there.
 * Used by the shell to implement the Paste command.
 */
void core_paste(const char *s);

#if defined(ANDROID) || defined(IPHONE)

/* core_get_char_pixels()
 *
 * Gets character pixels from the calculator's 8x5 characters, for the
 * given UTF-8 encoded character, provided as a null-terminated string.
 */
void core_get_char_pixels(const char *ch, char *pixels);

#endif

/* core_settings
 *
 * This is a struct that stores user-configurable core settings. The shell
 * should provide the appropriate controls in a "Preferences" dialog box to
 * allow the user to view and change these settings.
 */
struct core_settings_struct {
    bool matrix_singularmatrix;
    bool matrix_outofrange;
    bool auto_repeat;
    bool localized_copy_paste;
};

extern core_settings_struct core_settings;


/*******************/
/* Keyboard repeat */
/*******************/

extern int repeating;
extern int repeating_shift;
extern int repeating_key;


/*******************/
/* Other functions */
/*******************/

extern bool force_redisplay;
extern int skin_flags;
extern bool start_eqn_cursor;
extern bool quitting;

int ascii2hp(char *dst, int dstlen, const char *src, int srclen = -1);
void set_shift(bool shift);
void set_alpha_entry(bool state);
void set_running(bool state);
bool program_running();
bool alpha_active();
void set_annunciators(int updn, int shf, int prt, int run, int g, int rad);
int dequeue_key();

void do_interactive(int command);
int find_builtin(const char *name, int namelen);

void sst();
void bst();

int find_menu_key(int key);
void start_incomplete_command(int cmd_id);
void finish_command_entry(bool refresh);
void finish_xeq();
bool start_alpha_prgm_line();
void finish_alpha_prgm_line();
int shiftcharacter(char c);
void set_old_pc(int4 pc);
const char *number_format();


#endif
