barnabyosborne-cmyk/Hp42s_calc/firmware/components/plus42core/core_commands5.cc

/*****************************************************************************
 * Plus42 -- an enhanced HP-42S calculator simulator
 * Copyright (C) 2004-2026  Thomas Okken
 *
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
 * You should have received a copy of the GNU General Public License
 * along with this program; if not, see http://www.gnu.org/licenses/.
 *****************************************************************************/

#include <string.h>
#include <stdlib.h>
#include "bid_conf.h"
#include "bid_functions.h"

#include "core_commands2.h"
#include "core_commands5.h"
#include "core_display.h"
#include "core_equations.h"
#include "core_helpers.h"
#include "core_main.h"
#include "core_math1.h"
#include "core_parser.h"
#include "core_sto_rcl.h"
#include "core_variables.h"

/********************************************************/
/* Implementations of HP-42S built-in functions, part 5 */
/********************************************************/

int docmd_linf(arg_struct *arg) {
    flags.f.lin_fit = 1;
    flags.f.log_fit = 0;
    flags.f.exp_fit = 0;
    flags.f.pwr_fit = 0;
    return ERR_NONE;
}

int docmd_logf(arg_struct *arg) {
    flags.f.lin_fit = 0;
    flags.f.log_fit = 1;
    flags.f.exp_fit = 0;
    flags.f.pwr_fit = 0;
    return ERR_NONE;
}

int docmd_expf(arg_struct *arg) {
    flags.f.lin_fit = 0;
    flags.f.log_fit = 0;
    flags.f.exp_fit = 1;
    flags.f.pwr_fit = 0;
    return ERR_NONE;
}

int docmd_pwrf(arg_struct *arg) {
    flags.f.lin_fit = 0;
    flags.f.log_fit = 0;
    flags.f.exp_fit = 0;
    flags.f.pwr_fit = 1;
    return ERR_NONE;
}

int docmd_allsigma(arg_struct *arg) {
    flags.f.all_sigma = 1;
    return ERR_NONE;
}

static struct sum_struct {
    phloat x;
    phloat x2;
    phloat y;
    phloat y2;
    phloat xy;
    phloat n;
    phloat lnx;
    phloat lnx2;
    phloat lny;
    phloat lny2;
    phloat lnxlny;
    phloat xlny;
    phloat ylnx;
} sum;

static int get_summation() {
    /* Check if summation registers are OK */
    int4 first = mode_sigma_reg;
    int4 last = first + (flags.f.all_sigma ? 13 : 6);
    int4 size, i;
    vartype *regs = recall_var("REGS", 4);
    vartype_realmatrix *r;
    phloat *sigmaregs;
    if (regs == NULL)
        return ERR_SIZE_ERROR;
    if (regs->type != TYPE_REALMATRIX)
        return ERR_INVALID_TYPE;
    r = (vartype_realmatrix *) regs;
    size = r->rows * r->columns;
    if (last > size)
        return ERR_SIZE_ERROR;
    for (i = first; i < last; i++)
        if (r->array->is_string[i] != 0)
            return ERR_ALPHA_DATA_IS_INVALID;
    sigmaregs = r->array->data + first;
    sum.x = sigmaregs[0];
    sum.x2 = sigmaregs[1];
    sum.y = sigmaregs[2];
    sum.y2 = sigmaregs[3];
    sum.xy = sigmaregs[4];
    sum.n = sigmaregs[5];
    if (flags.f.all_sigma) {
        sum.lnx = sigmaregs[6];
        sum.lnx2 = sigmaregs[7];
        sum.lny = sigmaregs[8];
        sum.lny2 = sigmaregs[9];
        sum.lnxlny = sigmaregs[10];
        sum.xlny = sigmaregs[11];
        sum.ylnx = sigmaregs[12];
    }
    return ERR_NONE;
}

static struct model_struct {
    phloat x;
    phloat x2;
    phloat y;
    phloat y2;
    phloat xy;
    phloat n;
    int ln_before;
    int exp_after;
    int valid;
    phloat slope;
    phloat yint;
} model;

#define MODEL_NONE -1
#define MODEL_LIN 0
#define MODEL_LOG 1
#define MODEL_EXP 2
#define MODEL_PWR 3

static int get_model_summation(int modl) {
    int err = get_summation();
    if (err != ERR_NONE)
        return err;
    switch (modl) {
        case MODEL_LIN:
            model.xy = sum.xy;
            model.ln_before = 0;
            model.exp_after = 0;
            break;
        case MODEL_LOG:
            if (flags.f.log_fit_invalid)
                return ERR_INVALID_FORECAST_MODEL;
            model.xy = sum.ylnx;
            model.ln_before = 1;
            model.exp_after = 0;
            break;
        case MODEL_EXP:
            if (flags.f.exp_fit_invalid)
                return ERR_INVALID_FORECAST_MODEL;
            model.xy = sum.xlny;
            model.ln_before = 0;
            model.exp_after = 1;
            break;
        case MODEL_PWR:
            if (flags.f.pwr_fit_invalid)
                return ERR_INVALID_FORECAST_MODEL;
            model.xy = sum.lnxlny;
            model.ln_before = 1;
            model.exp_after = 1;
            break;
        default:
            return ERR_INVALID_FORECAST_MODEL;
    }
    if (model.ln_before) {
        model.x = sum.lnx;
        model.x2 = sum.lnx2;
    } else {
        model.x = sum.x;
        model.x2 = sum.x2;
    }
    if (model.exp_after) {
        model.y = sum.lny;
        model.y2 = sum.lny2;
    } else {
        model.y = sum.y;
        model.y2 = sum.y2;
    }
    model.n = sum.n;
    return ERR_NONE;
}

static int corr_helper(int modl, phloat *r) {
    phloat cov, varx, vary, v, tr;
    int err = get_model_summation(modl);
    if (err != ERR_NONE)
        return err;
    if (model.n == 0 || model.n == 1)
        return ERR_STAT_MATH_ERROR;
    cov = model.xy - model.x * model.y / model.n;
    varx = model.x2 - model.x * model.x / model.n;
    vary = model.y2 - model.y * model.y / model.n;
    if (varx <= 0 || vary <= 0)
        return ERR_STAT_MATH_ERROR;
    v = varx * vary;
    if (v == 0)
        return ERR_STAT_MATH_ERROR;
    tr = cov / sqrt(v);
    if (tr < -1)
        tr = -1;
    else if (tr > 1)
        tr = 1;
    *r = tr;
    return ERR_NONE;
}

static int slope_yint_helper() {
    /* The caller should have made sure that 'model' is up to date
     * by calling get_model_summation() first.
     */
    phloat cov, varx, meanx, meany;
    int inf;
    if (model.n == 0 || model.n == 1)
        return ERR_STAT_MATH_ERROR;
    cov = model.xy - model.x * model.y / model.n;
    varx = model.x2 - model.x * model.x / model.n;
    if (varx == 0)
        return ERR_STAT_MATH_ERROR;
    model.slope = cov / varx;
    if ((inf = p_isinf(model.slope)) != 0)
        model.slope = inf < 0 ? NEG_HUGE_PHLOAT : POS_HUGE_PHLOAT;
    meanx = model.x / model.n;
    meany = model.y / model.n;
    model.yint = meany - model.slope * meanx;
    if ((inf = p_isinf(model.yint)) != 0)
        model.yint = inf < 0 ? NEG_HUGE_PHLOAT : POS_HUGE_PHLOAT;
    return ERR_NONE;
}

static int get_model() {
    if (flags.f.lin_fit)
        return MODEL_LIN;
    else if (flags.f.log_fit)
        return MODEL_LOG;
    else if (flags.f.exp_fit)
        return MODEL_EXP;
    else if (flags.f.pwr_fit)
        return MODEL_PWR;
    else
        return MODEL_NONE;
}

int docmd_best(arg_struct *arg) {
    int best = MODEL_NONE;
    phloat bestr = 0;
    int firsterr = ERR_NONE;
    int i;
    for (i = MODEL_LIN; i <= MODEL_PWR; i++) {
        phloat r;
        int err = corr_helper(i, &r);
        if (err == ERR_NONE) {
            if (r < 0)
                r = -r;
            if (r > bestr) {
                best = i;
                bestr = r;
            }
        } else {
            if (firsterr == ERR_NONE)
                firsterr = err;
        }
    }
    if (best == MODEL_NONE)
        best = MODEL_LIN;
    else
        firsterr = ERR_NONE;
    flags.f.lin_fit = best == MODEL_LIN;
    flags.f.log_fit = best == MODEL_LOG;
    flags.f.exp_fit = best == MODEL_EXP;
    flags.f.pwr_fit = best == MODEL_PWR;
    return firsterr;
}

int docmd_corr(arg_struct *arg) {
    phloat r;
    int err;
    vartype *rv;
    err = corr_helper(get_model(), &r);
    if (err != ERR_NONE)
        return err;
    rv = new_real(r);
    if (rv == NULL)
        return ERR_INSUFFICIENT_MEMORY;
    return recall_result(rv);
}

static int mappable_fcstx(phloat x, phloat *y) {
    int inf;
    if (model.exp_after) {
        if (x <= 0)
            return ERR_INVALID_FORECAST_MODEL;
        x = log(x);
    }
    if (model.slope == 0)
        return ERR_STAT_MATH_ERROR;
    x = (x - model.yint) / model.slope;
    if (model.ln_before)
        x = exp(x);
    if ((inf = p_isinf(x)) != 0)
        x = inf < 0 ? NEG_HUGE_PHLOAT : POS_HUGE_PHLOAT;
    *y = x;
    return ERR_NONE;
}

int docmd_fcstx(arg_struct *arg) {
    int err = get_model_summation(get_model());
    vartype *v;
    if (err != ERR_NONE)
        return err;
    err = slope_yint_helper();
    if (err != ERR_NONE)
        return err;
    if (stack[sp]->type == TYPE_REAL || stack[sp]->type == TYPE_REALMATRIX) {
        err = map_unary(stack[sp], &v, mappable_fcstx, NULL);
        if (err == ERR_NONE)
            unary_result(v);
        return err;
    } else if (stack[sp]->type == TYPE_STRING)
        return ERR_ALPHA_DATA_IS_INVALID;
    else
        return ERR_INVALID_TYPE;
}

static int mappable_fcsty(phloat x, phloat *y) {
    int inf;
    if (model.ln_before) {
        if (x <= 0)
            return ERR_INVALID_FORECAST_MODEL;
        x = log(x);
    }
    x = x * model.slope + model.yint;
    if (model.exp_after)
        x = exp(x);
    if ((inf = p_isinf(x)) != 0)
        x = inf < 0 ? NEG_HUGE_PHLOAT : POS_HUGE_PHLOAT;
    *y = x;
    return ERR_NONE;
}

int docmd_fcsty(arg_struct *arg) {
    int err = get_model_summation(get_model());
    vartype *v;
    if (err != ERR_NONE)
        return err;
    err = slope_yint_helper();
    if (err != ERR_NONE)
        return err;
    if (stack[sp]->type == TYPE_REAL || stack[sp]->type == TYPE_REALMATRIX) {
        err = map_unary(stack[sp], &v, mappable_fcsty, NULL);
        if (err == ERR_NONE)
            unary_result(v);
        return err;
    } else if (stack[sp]->type == TYPE_STRING)
        return ERR_ALPHA_DATA_IS_INVALID;
    else
        return ERR_INVALID_TYPE;
}

int docmd_mean(arg_struct *arg) {
    phloat m;
    int inf;
    vartype *mx, *my;
    int err = get_summation();
    if (err != ERR_NONE)
        return err;
    if (sum.n == 0)
        return ERR_STAT_MATH_ERROR;
    m = sum.x / sum.n;
    if ((inf = p_isinf(m)) != 0)
        m = inf < 0 ? NEG_HUGE_PHLOAT : POS_HUGE_PHLOAT;
    mx = new_real(m);
    if (mx == NULL)
        return ERR_INSUFFICIENT_MEMORY;
    m = sum.y / sum.n;
    if ((inf = p_isinf(m)) != 0)
        m = inf < 0 ? NEG_HUGE_PHLOAT : POS_HUGE_PHLOAT;
    my = new_real(m);
    if (my == NULL) {
        free_vartype(mx);
        return ERR_INSUFFICIENT_MEMORY;
    }
    if (flags.f.big_stack) {
        return recall_two_results(mx, my);
    } else {
        binary_two_results(mx, my);
        return ERR_NONE;
    }
}

int docmd_sdev(arg_struct *arg) {
    int err = get_summation();
    phloat var;
    vartype *sx, *sy;
    if (err != ERR_NONE)
        return err;
    if (sum.n == 0 || sum.n == 1)
        return ERR_STAT_MATH_ERROR;
    var = (sum.x2 - (sum.x * sum.x / sum.n)) / (sum.n - 1);
    if (var < 0)
        return ERR_STAT_MATH_ERROR;
    if (p_isinf(var))
        sx = new_real(POS_HUGE_PHLOAT);
    else
        sx = new_real(sqrt(var));
    if (sx == NULL)
        return ERR_INSUFFICIENT_MEMORY;
    var = (sum.y2 - (sum.y * sum.y / sum.n)) / (sum.n - 1);
    if (var < 0)
        return ERR_STAT_MATH_ERROR;
    if (p_isinf(var))
        sy = new_real(POS_HUGE_PHLOAT);
    else
        sy = new_real(sqrt(var));
    if (sy == NULL) {
        free_vartype(sx);
        return ERR_INSUFFICIENT_MEMORY;
    }
    if (flags.f.big_stack) {
        return recall_two_results(sx, sy);
    } else {
        binary_two_results(sx, sy);
        return ERR_NONE;
    }
}

int docmd_slope(arg_struct *arg) {
    int err = get_model_summation(get_model());
    vartype *v;
    if (err != ERR_NONE)
        return err;
    err = slope_yint_helper();
    if (err != ERR_NONE)
        return err;
    v = new_real(model.slope);
    if (v == NULL)
        return ERR_INSUFFICIENT_MEMORY;
    return recall_result(v);
}

int docmd_sum(arg_struct *arg) {
    int err = get_summation();
    vartype *sx, *sy;
    if (err != ERR_NONE)
        return err;
    sx = new_real(sum.x);
    if (sx == NULL)
        return ERR_INSUFFICIENT_MEMORY;
    sy = new_real(sum.y);
    if (sy == NULL) {
        free_vartype(sx);
        return ERR_INSUFFICIENT_MEMORY;
    }
    if (flags.f.big_stack) {
        return recall_two_results(sx, sy);
    } else {
        binary_two_results(sx, sy);
        return ERR_NONE;
    }
}

int docmd_wmean(arg_struct *arg) {
    phloat wm;
    int inf;
    vartype *v;
    int err = get_summation();
    if (err != ERR_NONE)
        return err;
    if (sum.y == 0)
        return ERR_STAT_MATH_ERROR;
    wm = sum.xy / sum.y;
    if ((inf = p_isinf(wm)) != 0)
        wm = inf < 0 ? NEG_HUGE_PHLOAT : POS_HUGE_PHLOAT;
    v = new_real(wm);
    if (v == NULL)
        return ERR_INSUFFICIENT_MEMORY;
    return recall_result(v);
}

int docmd_yint(arg_struct *arg) {
    int err = get_model_summation(get_model());
    phloat yint;
    vartype *v;
    if (err != ERR_NONE)
        return err;
    err = slope_yint_helper();
    if (err != ERR_NONE)
        return err;
    if (model.exp_after) {
        yint = exp(model.yint);
        if (p_isinf(yint) != 0)
            yint = POS_HUGE_PHLOAT;
    } else
        yint = model.yint;
    v = new_real(yint);
    if (v == NULL)
        return ERR_INSUFFICIENT_MEMORY;
    return recall_result(v);
}

int docmd_integ(arg_struct *arg) {
    int err;
    if (arg->type == ARGTYPE_IND_NUM
            || arg->type == ARGTYPE_IND_STK
            || arg->type == ARGTYPE_IND_STR) {
        err = resolve_ind_arg(arg);
        if (err != ERR_NONE)
            return err;
    }
    if (arg->type != ARGTYPE_STR)
        return ERR_INVALID_TYPE;
    if (!program_running())
        clear_all_rtns();
    string_copy(reg_alpha, &reg_alpha_length, arg->val.text, arg->length);
    return start_integ(0, arg->val.text, arg->length);
}

int docmd_linsigma(arg_struct *arg) {
    flags.f.all_sigma = 0;
    return ERR_NONE;
}

int docmd_pgmslv(arg_struct *arg) {
    if (arg->type == ARGTYPE_IND_NUM
            || arg->type == ARGTYPE_IND_STK
            || arg->type == ARGTYPE_IND_STR) {
        int err = resolve_ind_arg(arg);
        if (err != ERR_NONE)
            return err;
    }
    if (arg->type == ARGTYPE_STR) {
        pgm_index prgm;
        int4 pc;
        if (!find_global_label(arg, &prgm, &pc))
            return ERR_LABEL_NOT_FOUND;
        set_solve_prgm(arg->val.text, arg->length);
        return ERR_NONE;
    } else
        return ERR_INVALID_TYPE;
}

int docmd_eqnslv(arg_struct *arg) {
    vartype_equation *eq;
    int err = get_arg_equation(arg, &eq);
    if (err != ERR_NONE)
        return err;
    return set_solve_eqn((vartype *) eq);
}

int docmd_pgmint(arg_struct *arg) {
    if (arg->type == ARGTYPE_IND_NUM
            || arg->type == ARGTYPE_IND_STK
            || arg->type == ARGTYPE_IND_STR) {
        int err = resolve_ind_arg(arg);
        if (err != ERR_NONE)
            return err;
    }
    if (arg->type == ARGTYPE_STR) {
        pgm_index prgm;
        int4 pc;
        if (!find_global_label(arg, &prgm, &pc))
            return ERR_LABEL_NOT_FOUND;
        set_integ_prgm(arg->val.text, arg->length);
        return ERR_NONE;
    } else
        return ERR_INVALID_TYPE;
}

int docmd_eqnint(arg_struct *arg) {
    vartype_equation *eq;
    int err = get_arg_equation(arg, &eq);
    if (err != ERR_NONE)
        return err;
    return set_integ_eqn((vartype *) eq);
}

int appmenu_exitcallback_3(int menuid, bool exitall) {
    if (menuid == MENU_NONE && !exitall) {
        if (varmenu_eqn != NULL) {
            if (mode_varmenu_whence == CATSECT_TOP)
                set_menu(MENULEVEL_APP, MENU_NONE);
            return eqn_start(-1);
        }
        set_menu(MENULEVEL_APP, MENU_CATALOG);
        set_cat_section(CATSECT_PGM_SOLVE);
    } else
        mode_appmenu = menuid;
    return ERR_NONE;
}

int docmd_pgmslvi(arg_struct *arg) {
    if (arg->type == ARGTYPE_STR) {
        eqn_end();
        pgm_index prgm;
        int4 pc;
        int idx;
        if (!find_global_label(arg, &prgm, &pc, &idx))
            return ERR_LABEL_NOT_FOUND;
        if (!label_has_mvar(prgm.dir, idx))
            return ERR_NO_MENU_VARIABLES;
        set_solve_prgm(arg->val.text, arg->length);
        config_varmenu_lbl(arg->val.text, arg->length);
        varmenu_row = 0;
        varmenu_role = 1;
        set_menu(MENULEVEL_APP, MENU_VARMENU);
        set_appmenu_exitcallback(3);
        return ERR_NONE;
    } else
        return ERR_INVALID_TYPE;
}

int docmd_eqnslvi(arg_struct *arg) {
    if (arg->type == ARGTYPE_EQN) {
        eqn_end();
        int idx = arg->val.num;
        if (!has_parameters(eq_dir->prgms[idx].eq_data))
            return ERR_NO_MENU_VARIABLES;
        vartype *eq = new_equation(eq_dir->prgms[idx].eq_data);
        int err = set_solve_eqn(eq);
        if (err != ERR_NONE) {
            free_vartype(eq);
            return err;
        }
        config_varmenu_eqn(eq);
        free_vartype(eq);
        varmenu_row = 0;
        varmenu_role = 1;
        mode_varmenu = true;
        set_menu(MENULEVEL_APP, MENU_VARMENU);
        set_appmenu_exitcallback(3);
        return ERR_NONE;
    } else
        return ERR_INVALID_TYPE;
}

int appmenu_exitcallback_4(int menuid, bool exitall) {
    if (menuid == MENU_NONE && !exitall) {
        if (varmenu_eqn != NULL)
            return eqn_start(-1);
        set_menu(MENULEVEL_APP, MENU_CATALOG);
        set_cat_section(CATSECT_PGM_INTEG);
    } else
        mode_appmenu = menuid;
    return ERR_NONE;
}

int appmenu_exitcallback_5(int menuid, bool exitall) {
    if (menuid == MENU_NONE && !exitall) {
        free_vartype(varmenu_eqn);
        get_integ_prgm_eqn(varmenu, &varmenu_length, &varmenu_eqn);
        varmenu_row = 0;
        varmenu_role = 2;
        set_menu(MENULEVEL_APP, MENU_VARMENU);
        set_appmenu_exitcallback(4);
    } else
        mode_appmenu = menuid;
    return ERR_NONE;
}

int docmd_pgminti(arg_struct *arg) {
    if (arg->type == ARGTYPE_STR) {
        eqn_end();
        pgm_index prgm;
        int4 pc;
        int idx;
        if (!find_global_label(arg, &prgm, &pc, &idx))
            return ERR_LABEL_NOT_FOUND;
        if (!label_has_mvar(prgm.dir, idx))
            return ERR_NO_MENU_VARIABLES;
        set_integ_prgm(arg->val.text, arg->length);
        config_varmenu_lbl(arg->val.text, arg->length);
        varmenu_row = 0;
        varmenu_role = 2;
        set_menu(MENULEVEL_APP, MENU_VARMENU);
        set_appmenu_exitcallback(4);
        draw_message(0, "Set Vars; Select \3var", 21, false);
        mode_varmenu = true;
        return ERR_NONE;
    } else
        return ERR_INVALID_TYPE;
}
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
